NikhilVeeram/MEEN-305-FINAL/best-designs-20/ranked-designs/01_overall_rank__continuous_uniform_both_load_cases_9in_corrected__eval_0370__w_0.02815__fos_1.642/README.md

# Rank 01: continuous_uniform_both_load_cases_9in_corrected eval 370

- Weight-first rank score: `0.028149`
- Weight: `0.02815 lbf`
- Minimum FoS: `1.642`
- Max deflection: `0.09484 in`
- LC2 FoS, x=3..7: mean `2.259`, std `0.426`, range `1.581`
- Print checks: wall `0.040 in`, max opening `0.000`, min ligament `0.105 in`
- Governing case/location: `Load Case 2` at `x = 5.500 in`
- Source run: `continuous_uniform_both_load_cases_9in_corrected`
- Source evaluation id: `370`

This folder is a ranked report artifact generated from a feasible, corrected 9 in design candidate.
