NikhilVeeram/MEEN-305-FINAL/best-designs-20/ranked-designs/02_overall_rank__ultra_light_full_strength_seed2433__eval_1528__w_0.02894__fos_1.732/README.md

# Rank 02: ultra_light_full_strength_seed2433 eval 1528

- Weight-first rank score: `0.028936`
- Weight: `0.02894 lbf`
- Minimum FoS: `1.732`
- Max deflection: `0.16497 in`
- LC2 FoS, x=3..7: mean `2.686`, std `0.476`, range `1.786`
- Print checks: wall `0.040 in`, max opening `0.000`, min ligament `0.112 in`
- Governing case/location: `Load Case 1` at `x = 4.500 in`
- Source run: `ultra_light_full_strength_seed2433`
- Source evaluation id: `1528`

This folder is a ranked report artifact generated from a feasible, corrected 9 in design candidate.
