NikhilVeeram/MEEN-305-FINAL/best-designs-20/ranked-designs/03_overall_rank__ultra_light_run4_asymmetric_seed2427__eval_1102__w_0.02958__fos_2.116/README.md

# Rank 03: ultra_light_run4_asymmetric_seed2427 eval 1102

- Weight-first rank score: `0.029585`
- Weight: `0.02958 lbf`
- Minimum FoS: `2.116`
- Max deflection: `0.09429 in`
- LC2 FoS, x=3..7: mean `2.951`, std `0.675`, range `2.234`
- Print checks: wall `0.040 in`, max opening `0.000`, min ligament `0.147 in`
- Governing case/location: `Load Case 2` at `x = 5.500 in`
- Source run: `ultra_light_run4_asymmetric_seed2427`
- Source evaluation id: `1102`

This folder is a ranked report artifact generated from a feasible, corrected 9 in design candidate.
