NikhilVeeram/MEEN-305-FINAL/best-designs-20/ranked-designs/04_overall_rank__ultra_light_full_strength_seed2433__eval_2458__w_0.02971__fos_1.562/README.md

# Rank 04: ultra_light_full_strength_seed2433 eval 2458

- Weight-first rank score: `0.029710`
- Weight: `0.02971 lbf`
- Minimum FoS: `1.562`
- Max deflection: `0.14261 in`
- LC2 FoS, x=3..7: mean `2.116`, std `0.381`, range `1.238`
- Print checks: wall `0.040 in`, max opening `0.000`, min ligament `0.218 in`
- Governing case/location: `Load Case 2` at `x = 5.500 in`
- Source run: `ultra_light_full_strength_seed2433`
- Source evaluation id: `2458`

This folder is a ranked report artifact generated from a feasible, corrected 9 in design candidate.
