NikhilVeeram/MEEN-305-FINAL/best-designs-20/ranked-designs/05_overall_rank__ultra_light_full_infill_seed2432__eval_2924__w_0.03074__fos_1.789/README.md

# Rank 05: ultra_light_full_infill_seed2432 eval 2924

- Weight-first rank score: `0.030736`
- Weight: `0.03074 lbf`
- Minimum FoS: `1.789`
- Max deflection: `0.08733 in`
- LC2 FoS, x=3..7: mean `2.456`, std `0.451`, range `1.695`
- Print checks: wall `0.040 in`, max opening `0.000`, min ligament `0.199 in`
- Governing case/location: `Load Case 2` at `x = 5.500 in`
- Source run: `ultra_light_full_infill_seed2432`
- Source evaluation id: `2924`

This folder is a ranked report artifact generated from a feasible, corrected 9 in design candidate.
