NikhilVeeram/MEEN-305-FINAL/best-designs-20/ranked-designs/06_overall_rank__ultra_light_full_strength_seed2433__eval_1532__w_0.03127__fos_1.712/README.md

# Rank 06: ultra_light_full_strength_seed2433 eval 1532

- Weight-first rank score: `0.031265`
- Weight: `0.03127 lbf`
- Minimum FoS: `1.712`
- Max deflection: `0.11368 in`
- LC2 FoS, x=3..7: mean `2.360`, std `0.452`, range `1.663`
- Print checks: wall `0.046 in`, max opening `0.000`, min ligament `0.138 in`
- Governing case/location: `Load Case 2` at `x = 5.500 in`
- Source run: `ultra_light_full_strength_seed2433`
- Source evaluation id: `1532`

This folder is a ranked report artifact generated from a feasible, corrected 9 in design candidate.
