NikhilVeeram/MEEN-305-FINAL/best-designs-20/ranked-designs/07_overall_rank__ultra_light_full_infill_seed2432__eval_2497__w_0.03158__fos_1.751/README.md

# Rank 07: ultra_light_full_infill_seed2432 eval 2497

- Weight-first rank score: `0.031578`
- Weight: `0.03158 lbf`
- Minimum FoS: `1.751`
- Max deflection: `0.12404 in`
- LC2 FoS, x=3..7: mean `2.389`, std `0.416`, range `1.544`
- Print checks: wall `0.051 in`, max opening `0.000`, min ligament `0.122 in`
- Governing case/location: `Load Case 2` at `x = 5.500 in`
- Source run: `ultra_light_full_infill_seed2432`
- Source evaluation id: `2497`

This folder is a ranked report artifact generated from a feasible, corrected 9 in design candidate.
