NikhilVeeram/MEEN-305-FINAL/best-designs-20/ranked-designs/08_overall_rank__ultra_light_full_infill_seed2432__eval_2852__w_0.03254__fos_1.713/README.md

# Rank 08: ultra_light_full_infill_seed2432 eval 2852

- Weight-first rank score: `0.032545`
- Weight: `0.03254 lbf`
- Minimum FoS: `1.713`
- Max deflection: `0.14508 in`
- LC2 FoS, x=3..7: mean `2.474`, std `0.432`, range `1.617`
- Print checks: wall `0.052 in`, max opening `0.000`, min ligament `0.096 in`
- Governing case/location: `Load Case 1` at `x = 4.500 in`
- Source run: `ultra_light_full_infill_seed2432`
- Source evaluation id: `2852`

This folder is a ranked report artifact generated from a feasible, corrected 9 in design candidate.
