NikhilVeeram/MEEN-305-FINAL/best-designs-20/ranked-designs/09_overall_rank__ultra_light_full_infill_seed2432__eval_2251__w_0.03329__fos_1.595/README.md

# Rank 09: ultra_light_full_infill_seed2432 eval 2251

- Weight-first rank score: `0.033289`
- Weight: `0.03329 lbf`
- Minimum FoS: `1.595`
- Max deflection: `0.11348 in`
- LC2 FoS, x=3..7: mean `2.198`, std `0.417`, range `1.539`
- Print checks: wall `0.056 in`, max opening `0.000`, min ligament `0.111 in`
- Governing case/location: `Load Case 2` at `x = 5.500 in`
- Source run: `ultra_light_full_infill_seed2432`
- Source evaluation id: `2251`

This folder is a ranked report artifact generated from a feasible, corrected 9 in design candidate.
