NikhilVeeram/MEEN-305-FINAL/best-designs-20/ranked-designs/10_overall_rank__ultra_light_full_infill_seed2432__eval_2514__w_0.03483__fos_1.572/README.md

# Rank 10: ultra_light_full_infill_seed2432 eval 2514

- Weight-first rank score: `0.034829`
- Weight: `0.03483 lbf`
- Minimum FoS: `1.572`
- Max deflection: `0.11648 in`
- LC2 FoS, x=3..7: mean `2.176`, std `0.440`, range `1.578`
- Print checks: wall `0.055 in`, max opening `0.000`, min ligament `0.156 in`
- Governing case/location: `Load Case 2` at `x = 5.500 in`
- Source run: `ultra_light_full_infill_seed2432`
- Source evaluation id: `2514`

This folder is a ranked report artifact generated from a feasible, corrected 9 in design candidate.
