NikhilVeeram/MEEN-305-FINAL/best-designs-20/ranked-designs/11_overall_rank__continuous_uniform_both_load_cases_9in_corrected__eval_0572__w_0.03504__fos_1.877/README.md

# Rank 11: continuous_uniform_both_load_cases_9in_corrected eval 572

- Weight-first rank score: `0.035042`
- Weight: `0.03504 lbf`
- Minimum FoS: `1.877`
- Max deflection: `0.11531 in`
- LC2 FoS, x=3..7: mean `2.533`, std `0.474`, range `1.439`
- Print checks: wall `0.045 in`, max opening `0.000`, min ligament `0.274 in`
- Governing case/location: `Load Case 2` at `x = 5.500 in`
- Source run: `continuous_uniform_both_load_cases_9in_corrected`
- Source evaluation id: `572`

This folder is a ranked report artifact generated from a feasible, corrected 9 in design candidate.
