NikhilVeeram/MEEN-305-FINAL/best-designs-20/ranked-designs/12_overall_rank__continuous_uniform_both_load_cases_9in_corrected__eval_0680__w_0.03546__fos_2.902/README.md

# Rank 12: continuous_uniform_both_load_cases_9in_corrected eval 680

- Weight-first rank score: `0.035456`
- Weight: `0.03546 lbf`
- Minimum FoS: `2.902`
- Max deflection: `0.05080 in`
- LC2 FoS, x=3..7: mean `3.964`, std `0.689`, range `2.585`
- Print checks: wall `0.040 in`, max opening `0.000`, min ligament `0.158 in`
- Governing case/location: `Load Case 2` at `x = 5.500 in`
- Source run: `continuous_uniform_both_load_cases_9in_corrected`
- Source evaluation id: `680`

This folder is a ranked report artifact generated from a feasible, corrected 9 in design candidate.
