NikhilVeeram/MEEN-305-FINAL/best-designs-20/ranked-designs/13_overall_rank__ultra_light_runa_seed2430__eval_2464__w_0.03652__fos_2.154/README.md

# Rank 13: ultra_light_runA_seed2430 eval 2464

- Weight-first rank score: `0.036523`
- Weight: `0.03652 lbf`
- Minimum FoS: `2.154`
- Max deflection: `0.08366 in`
- LC2 FoS, x=3..7: mean `2.841`, std `0.393`, range `1.373`
- Print checks: wall `0.049 in`, max opening `0.000`, min ligament `0.218 in`
- Governing case/location: `Load Case 2` at `x = 5.500 in`
- Source run: `ultra_light_runA_seed2430`
- Source evaluation id: `2464`

This folder is a ranked report artifact generated from a feasible, corrected 9 in design candidate.
