NikhilVeeram/MEEN-305-FINAL/best-designs-20/ranked-designs/14_overall_rank__continuous_uniform_both_load_cases_9in_corrected__eval_0402__w_0.03782__fos_2.022/README.md

# Rank 14: continuous_uniform_both_load_cases_9in_corrected eval 402

- Weight-first rank score: `0.037825`
- Weight: `0.03782 lbf`
- Minimum FoS: `2.022`
- Max deflection: `0.09886 in`
- LC2 FoS, x=3..7: mean `2.773`, std `0.511`, range `1.940`
- Print checks: wall `0.040 in`, max opening `0.000`, min ligament `0.263 in`
- Governing case/location: `Load Case 2` at `x = 5.500 in`
- Source run: `continuous_uniform_both_load_cases_9in_corrected`
- Source evaluation id: `402`

This folder is a ranked report artifact generated from a feasible, corrected 9 in design candidate.
