NikhilVeeram/MEEN-305-FINAL/best-designs-20/ranked-designs/15_overall_rank__continuous_uniform_both_load_cases_9in_corrected__eval_0364__w_0.03983__fos_1.695/README.md

# Rank 15: continuous_uniform_both_load_cases_9in_corrected eval 364

- Weight-first rank score: `0.039828`
- Weight: `0.03983 lbf`
- Minimum FoS: `1.695`
- Max deflection: `0.10435 in`
- LC2 FoS, x=3..7: mean `2.337`, std `0.477`, range `1.711`
- Print checks: wall `0.063 in`, max opening `0.000`, min ligament `0.106 in`
- Governing case/location: `Load Case 2` at `x = 5.500 in`
- Source run: `continuous_uniform_both_load_cases_9in_corrected`
- Source evaluation id: `364`

This folder is a ranked report artifact generated from a feasible, corrected 9 in design candidate.
