NikhilVeeram/MEEN-305-FINAL/best-designs-20/ranked-designs/16_overall_rank__continuous_uniform_both_load_cases_9in_corrected__eval_0219__w_0.03983__fos_1.761/README.md

# Rank 16: continuous_uniform_both_load_cases_9in_corrected eval 219

- Weight-first rank score: `0.039828`
- Weight: `0.03983 lbf`
- Minimum FoS: `1.761`
- Max deflection: `0.11057 in`
- LC2 FoS, x=3..7: mean `2.406`, std `0.427`, range `1.617`
- Print checks: wall `0.061 in`, max opening `0.000`, min ligament `0.175 in`
- Governing case/location: `Load Case 2` at `x = 5.500 in`
- Source run: `continuous_uniform_both_load_cases_9in_corrected`
- Source evaluation id: `219`

This folder is a ranked report artifact generated from a feasible, corrected 9 in design candidate.
