NikhilVeeram/MEEN-305-FINAL/best-designs-20/ranked-designs/18_overall_rank__continuous_uniform_both_load_cases_9in_corrected__eval_0441__w_0.04079__fos_1.503/README.md

# Rank 18: continuous_uniform_both_load_cases_9in_corrected eval 441

- Weight-first rank score: `0.040794`
- Weight: `0.04079 lbf`
- Minimum FoS: `1.503`
- Max deflection: `0.16121 in`
- LC2 FoS, x=3..7: mean `2.118`, std `0.592`, range `2.147`
- Print checks: wall `0.051 in`, max opening `0.000`, min ligament `0.278 in`
- Governing case/location: `Load Case 2` at `x = 5.500 in`
- Source run: `continuous_uniform_both_load_cases_9in_corrected`
- Source evaluation id: `441`

This folder is a ranked report artifact generated from a feasible, corrected 9 in design candidate.
