NikhilVeeram/MEEN-305-FINAL/best-designs-20/ranked-designs/19_overall_rank__ultra_light_full_infill_seed2432__eval_2513__w_0.04121__fos_1.565/README.md

# Rank 19: ultra_light_full_infill_seed2432 eval 2513

- Weight-first rank score: `0.041215`
- Weight: `0.04121 lbf`
- Minimum FoS: `1.565`
- Max deflection: `0.14041 in`
- LC2 FoS, x=3..7: mean `2.134`, std `0.384`, range `1.456`
- Print checks: wall `0.062 in`, max opening `0.000`, min ligament `0.176 in`
- Governing case/location: `Load Case 2` at `x = 5.500 in`
- Source run: `ultra_light_full_infill_seed2432`
- Source evaluation id: `2513`

This folder is a ranked report artifact generated from a feasible, corrected 9 in design candidate.
