NikhilVeeram/MEEN-305-FINAL/best-designs-20/ranked-designs/20_overall_rank__ultra_light_run3_lowheight_seed2426__eval_1611__w_0.04175__fos_2.633/README.md

# Rank 20: ultra_light_run3_lowheight_seed2426 eval 1611

- Weight-first rank score: `0.041748`
- Weight: `0.04175 lbf`
- Minimum FoS: `2.633`
- Max deflection: `0.06265 in`
- LC2 FoS, x=3..7: mean `3.553`, std `0.714`, range `1.912`
- Print checks: wall `0.071 in`, max opening `0.000`, min ligament `0.077 in`
- Governing case/location: `Load Case 2` at `x = 5.500 in`
- Source run: `ultra_light_run3_lowheight_seed2426`
- Source evaluation id: `1611`

This folder is a ranked report artifact generated from a feasible, corrected 9 in design candidate.
