NikhilVeeram/MEEN-305-FINAL/designs/model_exports/continuous_mesh_exports_9in_corrected/README.md

# 3D Beam Models

This folder contains generated 3D models and preview renders for the beam designs found in the repo.

## Generated designs

### continuous_uniform_both_load_cases_9in_corrected

- STL: [continuous_uniform_both_load_cases_9in_corrected.stl](continuous_uniform_both_load_cases_9in_corrected.stl)
- OBJ: [continuous_uniform_both_load_cases_9in_corrected.obj](continuous_uniform_both_load_cases_9in_corrected.obj)
- Preview: [continuous_uniform_both_load_cases_9in_corrected_preview.png](continuous_uniform_both_load_cases_9in_corrected_preview.png)
- DXF sketch: [continuous_uniform_both_load_cases_9in_corrected.dxf](continuous_uniform_both_load_cases_9in_corrected.dxf)

## How to view them

- Double-click an `.obj` or `.stl` file in a local 3D viewer if you have one installed.
- Use the `.png` previews for quick comparison inside the repo.
- Re-run `python scripts/beam_3d_models.py` after optimization updates to refresh the models.
