NikhilVeeram/MEEN-305-FINAL/designs/model_exports/continuous_mesh_exports/README.md

# 3D Beam Models

This folder contains generated 3D models and preview renders for the beam designs found in the repo.

## Generated designs

### continuous_uniform_load_case_1

- STL: [continuous_uniform_load_case_1.stl](continuous_uniform_load_case_1.stl)
- OBJ: [continuous_uniform_load_case_1.obj](continuous_uniform_load_case_1.obj)
- Preview: [continuous_uniform_load_case_1_preview.png](continuous_uniform_load_case_1_preview.png)
- DXF sketch: [continuous_uniform_load_case_1.dxf](continuous_uniform_load_case_1.dxf)

### continuous_uniform_load_case_2

- STL: [continuous_uniform_load_case_2.stl](continuous_uniform_load_case_2.stl)
- OBJ: [continuous_uniform_load_case_2.obj](continuous_uniform_load_case_2.obj)
- Preview: [continuous_uniform_load_case_2_preview.png](continuous_uniform_load_case_2_preview.png)
- DXF sketch: [continuous_uniform_load_case_2.dxf](continuous_uniform_load_case_2.dxf)

### continuous_uniform_both_load_cases

- STL: [continuous_uniform_both_load_cases.stl](continuous_uniform_both_load_cases.stl)
- OBJ: [continuous_uniform_both_load_cases.obj](continuous_uniform_both_load_cases.obj)
- Preview: [continuous_uniform_both_load_cases_preview.png](continuous_uniform_both_load_cases_preview.png)
- DXF sketch: [continuous_uniform_both_load_cases.dxf](continuous_uniform_both_load_cases.dxf)

## How to view them

- Double-click an `.obj` or `.stl` file in a local 3D viewer if you have one installed.
- Use the `.png` previews for quick comparison inside the repo.
- Re-run `python scripts/beam_3d_models.py` after optimization updates to refresh the models.
