NikhilVeeram/MEEN-305-FINAL/best-designs-20/design-packages/01_overall_rank__continuous_uniform_both_load_cases_9in_corrected__eval_0370__w_0.02815__fos_1.642/README.md

# 01_overall_rank__continuous_uniform_both_load_cases_9in_corrected__eval_0370__w_0.02815__fos_1.642

- Included files:
  - `01_overall_rank__continuous_uniform_both_load_cases_9in_corrected__eval_0370__w_0.02815__fos_1.642.stl`
  - `01_overall_rank__continuous_uniform_both_load_cases_9in_corrected__eval_0370__w_0.02815__fos_1.642.obj`
  - `01_overall_rank__continuous_uniform_both_load_cases_9in_corrected__eval_0370__w_0.02815__fos_1.642_preview.png`
  - `01_overall_rank__continuous_uniform_both_load_cases_9in_corrected__eval_0370__w_0.02815__fos_1.642.dxf`
  - `best_design.json`
  - `optimization_report.md`
  - `optimization_report.tex`
  - `beam_parameter_map.png`
  - `best_design/*.png`

The PNG preview is the 3D look. The DXF file is a lightweight 2D sketch export.
