NikhilVeeram/MEEN-305-FINAL/best-designs-20/design-packages/02_overall_rank__ultra_light_full_strength_seed2433__eval_1528__w_0.02894__fos_1.732/README.md

# 02_overall_rank__ultra_light_full_strength_seed2433__eval_1528__w_0.02894__fos_1.732

- Included files:
  - `02_overall_rank__ultra_light_full_strength_seed2433__eval_1528__w_0.02894__fos_1.732.stl`
  - `02_overall_rank__ultra_light_full_strength_seed2433__eval_1528__w_0.02894__fos_1.732.obj`
  - `02_overall_rank__ultra_light_full_strength_seed2433__eval_1528__w_0.02894__fos_1.732_preview.png`
  - `02_overall_rank__ultra_light_full_strength_seed2433__eval_1528__w_0.02894__fos_1.732.dxf`
  - `best_design.json`
  - `optimization_report.md`
  - `optimization_report.tex`
  - `beam_parameter_map.png`
  - `best_design/*.png`

The PNG preview is the 3D look. The DXF file is a lightweight 2D sketch export.
