NikhilVeeram/MEEN-305-FINAL/best-designs-20/design-packages/03_overall_rank__ultra_light_run4_asymmetric_seed2427__eval_1102__w_0.02958__fos_2.116/README.md

# 03_overall_rank__ultra_light_run4_asymmetric_seed2427__eval_1102__w_0.02958__fos_2.116

- Included files:
  - `03_overall_rank__ultra_light_run4_asymmetric_seed2427__eval_1102__w_0.02958__fos_2.116.stl`
  - `03_overall_rank__ultra_light_run4_asymmetric_seed2427__eval_1102__w_0.02958__fos_2.116.obj`
  - `03_overall_rank__ultra_light_run4_asymmetric_seed2427__eval_1102__w_0.02958__fos_2.116_preview.png`
  - `03_overall_rank__ultra_light_run4_asymmetric_seed2427__eval_1102__w_0.02958__fos_2.116.dxf`
  - `best_design.json`
  - `optimization_report.md`
  - `optimization_report.tex`
  - `beam_parameter_map.png`
  - `best_design/*.png`

The PNG preview is the 3D look. The DXF file is a lightweight 2D sketch export.
