NikhilVeeram/MEEN-305-FINAL/best-designs-20/design-packages/04_overall_rank__ultra_light_full_strength_seed2433__eval_2458__w_0.02971__fos_1.562/README.md

# 04_overall_rank__ultra_light_full_strength_seed2433__eval_2458__w_0.02971__fos_1.562

- Included files:
  - `04_overall_rank__ultra_light_full_strength_seed2433__eval_2458__w_0.02971__fos_1.562.stl`
  - `04_overall_rank__ultra_light_full_strength_seed2433__eval_2458__w_0.02971__fos_1.562.obj`
  - `04_overall_rank__ultra_light_full_strength_seed2433__eval_2458__w_0.02971__fos_1.562_preview.png`
  - `04_overall_rank__ultra_light_full_strength_seed2433__eval_2458__w_0.02971__fos_1.562.dxf`
  - `best_design.json`
  - `optimization_report.md`
  - `optimization_report.tex`
  - `beam_parameter_map.png`
  - `best_design/*.png`

The PNG preview is the 3D look. The DXF file is a lightweight 2D sketch export.
