NikhilVeeram/MEEN-305-FINAL/best-designs-20/design-packages/05_overall_rank__ultra_light_full_infill_seed2432__eval_2924__w_0.03074__fos_1.789/README.md

# 05_overall_rank__ultra_light_full_infill_seed2432__eval_2924__w_0.03074__fos_1.789

- Included files:
  - `05_overall_rank__ultra_light_full_infill_seed2432__eval_2924__w_0.03074__fos_1.789.stl`
  - `05_overall_rank__ultra_light_full_infill_seed2432__eval_2924__w_0.03074__fos_1.789.obj`
  - `05_overall_rank__ultra_light_full_infill_seed2432__eval_2924__w_0.03074__fos_1.789_preview.png`
  - `05_overall_rank__ultra_light_full_infill_seed2432__eval_2924__w_0.03074__fos_1.789.dxf`
  - `best_design.json`
  - `optimization_report.md`
  - `optimization_report.tex`
  - `beam_parameter_map.png`
  - `best_design/*.png`

The PNG preview is the 3D look. The DXF file is a lightweight 2D sketch export.
