NikhilVeeram/MEEN-305-FINAL/best-designs-20/design-packages/06_overall_rank__ultra_light_full_strength_seed2433__eval_1532__w_0.03127__fos_1.712/README.md

# 06_overall_rank__ultra_light_full_strength_seed2433__eval_1532__w_0.03127__fos_1.712

- Included files:
  - `06_overall_rank__ultra_light_full_strength_seed2433__eval_1532__w_0.03127__fos_1.712.stl`
  - `06_overall_rank__ultra_light_full_strength_seed2433__eval_1532__w_0.03127__fos_1.712.obj`
  - `06_overall_rank__ultra_light_full_strength_seed2433__eval_1532__w_0.03127__fos_1.712_preview.png`
  - `06_overall_rank__ultra_light_full_strength_seed2433__eval_1532__w_0.03127__fos_1.712.dxf`
  - `best_design.json`
  - `optimization_report.md`
  - `optimization_report.tex`
  - `beam_parameter_map.png`
  - `best_design/*.png`

The PNG preview is the 3D look. The DXF file is a lightweight 2D sketch export.
