NikhilVeeram/MEEN-305-FINAL/best-designs-20/design-packages/07_overall_rank__ultra_light_full_infill_seed2432__eval_2497__w_0.03158__fos_1.751/README.md

# 07_overall_rank__ultra_light_full_infill_seed2432__eval_2497__w_0.03158__fos_1.751

- Included files:
  - `07_overall_rank__ultra_light_full_infill_seed2432__eval_2497__w_0.03158__fos_1.751.stl`
  - `07_overall_rank__ultra_light_full_infill_seed2432__eval_2497__w_0.03158__fos_1.751.obj`
  - `07_overall_rank__ultra_light_full_infill_seed2432__eval_2497__w_0.03158__fos_1.751_preview.png`
  - `07_overall_rank__ultra_light_full_infill_seed2432__eval_2497__w_0.03158__fos_1.751.dxf`
  - `best_design.json`
  - `optimization_report.md`
  - `optimization_report.tex`
  - `beam_parameter_map.png`
  - `best_design/*.png`

The PNG preview is the 3D look. The DXF file is a lightweight 2D sketch export.
