NikhilVeeram/MEEN-305-FINAL/best-designs-20/design-packages/08_overall_rank__ultra_light_full_infill_seed2432__eval_2852__w_0.03254__fos_1.713/README.md

# 08_overall_rank__ultra_light_full_infill_seed2432__eval_2852__w_0.03254__fos_1.713

- Included files:
  - `08_overall_rank__ultra_light_full_infill_seed2432__eval_2852__w_0.03254__fos_1.713.stl`
  - `08_overall_rank__ultra_light_full_infill_seed2432__eval_2852__w_0.03254__fos_1.713.obj`
  - `08_overall_rank__ultra_light_full_infill_seed2432__eval_2852__w_0.03254__fos_1.713_preview.png`
  - `08_overall_rank__ultra_light_full_infill_seed2432__eval_2852__w_0.03254__fos_1.713.dxf`
  - `best_design.json`
  - `optimization_report.md`
  - `optimization_report.tex`
  - `beam_parameter_map.png`
  - `best_design/*.png`

The PNG preview is the 3D look. The DXF file is a lightweight 2D sketch export.
