NikhilVeeram/MEEN-305-FINAL/best-designs-20/design-packages/09_overall_rank__ultra_light_full_infill_seed2432__eval_2251__w_0.03329__fos_1.595/README.md

# 09_overall_rank__ultra_light_full_infill_seed2432__eval_2251__w_0.03329__fos_1.595

- Included files:
  - `09_overall_rank__ultra_light_full_infill_seed2432__eval_2251__w_0.03329__fos_1.595.stl`
  - `09_overall_rank__ultra_light_full_infill_seed2432__eval_2251__w_0.03329__fos_1.595.obj`
  - `09_overall_rank__ultra_light_full_infill_seed2432__eval_2251__w_0.03329__fos_1.595_preview.png`
  - `09_overall_rank__ultra_light_full_infill_seed2432__eval_2251__w_0.03329__fos_1.595.dxf`
  - `best_design.json`
  - `optimization_report.md`
  - `optimization_report.tex`
  - `beam_parameter_map.png`
  - `best_design/*.png`

The PNG preview is the 3D look. The DXF file is a lightweight 2D sketch export.
