NikhilVeeram/MEEN-305-FINAL/best-designs-20/design-packages/10_overall_rank__ultra_light_full_infill_seed2432__eval_2514__w_0.03483__fos_1.572/README.md

# 10_overall_rank__ultra_light_full_infill_seed2432__eval_2514__w_0.03483__fos_1.572

- Included files:
  - `10_overall_rank__ultra_light_full_infill_seed2432__eval_2514__w_0.03483__fos_1.572.stl`
  - `10_overall_rank__ultra_light_full_infill_seed2432__eval_2514__w_0.03483__fos_1.572.obj`
  - `10_overall_rank__ultra_light_full_infill_seed2432__eval_2514__w_0.03483__fos_1.572_preview.png`
  - `10_overall_rank__ultra_light_full_infill_seed2432__eval_2514__w_0.03483__fos_1.572.dxf`
  - `best_design.json`
  - `optimization_report.md`
  - `optimization_report.tex`
  - `beam_parameter_map.png`
  - `best_design/*.png`

The PNG preview is the 3D look. The DXF file is a lightweight 2D sketch export.
