NikhilVeeram/MEEN-305-FINAL/best-designs-20/design-packages/11_overall_rank__continuous_uniform_both_load_cases_9in_corrected__eval_0572__w_0.03504__fos_1.877/README.md

# 11_overall_rank__continuous_uniform_both_load_cases_9in_corrected__eval_0572__w_0.03504__fos_1.877

- Included files:
  - `11_overall_rank__continuous_uniform_both_load_cases_9in_corrected__eval_0572__w_0.03504__fos_1.877.stl`
  - `11_overall_rank__continuous_uniform_both_load_cases_9in_corrected__eval_0572__w_0.03504__fos_1.877.obj`
  - `11_overall_rank__continuous_uniform_both_load_cases_9in_corrected__eval_0572__w_0.03504__fos_1.877_preview.png`
  - `11_overall_rank__continuous_uniform_both_load_cases_9in_corrected__eval_0572__w_0.03504__fos_1.877.dxf`
  - `best_design.json`
  - `optimization_report.md`
  - `optimization_report.tex`
  - `beam_parameter_map.png`
  - `best_design/*.png`

The PNG preview is the 3D look. The DXF file is a lightweight 2D sketch export.
