NikhilVeeram/MEEN-305-FINAL/best-designs-20/design-packages/12_overall_rank__continuous_uniform_both_load_cases_9in_corrected__eval_0680__w_0.03546__fos_2.902/README.md

# 12_overall_rank__continuous_uniform_both_load_cases_9in_corrected__eval_0680__w_0.03546__fos_2.902

- Included files:
  - `12_overall_rank__continuous_uniform_both_load_cases_9in_corrected__eval_0680__w_0.03546__fos_2.902.stl`
  - `12_overall_rank__continuous_uniform_both_load_cases_9in_corrected__eval_0680__w_0.03546__fos_2.902.obj`
  - `12_overall_rank__continuous_uniform_both_load_cases_9in_corrected__eval_0680__w_0.03546__fos_2.902_preview.png`
  - `12_overall_rank__continuous_uniform_both_load_cases_9in_corrected__eval_0680__w_0.03546__fos_2.902.dxf`
  - `best_design.json`
  - `optimization_report.md`
  - `optimization_report.tex`
  - `beam_parameter_map.png`
  - `best_design/*.png`

The PNG preview is the 3D look. The DXF file is a lightweight 2D sketch export.
