NikhilVeeram/MEEN-305-FINAL/best-designs-20/design-packages/13_overall_rank__ultra_light_runa_seed2430__eval_2464__w_0.03652__fos_2.154/README.md

# 13_overall_rank__ultra_light_runa_seed2430__eval_2464__w_0.03652__fos_2.154

- Included files:
  - `13_overall_rank__ultra_light_runa_seed2430__eval_2464__w_0.03652__fos_2.154.stl`
  - `13_overall_rank__ultra_light_runa_seed2430__eval_2464__w_0.03652__fos_2.154.obj`
  - `13_overall_rank__ultra_light_runa_seed2430__eval_2464__w_0.03652__fos_2.154_preview.png`
  - `13_overall_rank__ultra_light_runa_seed2430__eval_2464__w_0.03652__fos_2.154.dxf`
  - `best_design.json`
  - `optimization_report.md`
  - `optimization_report.tex`
  - `beam_parameter_map.png`
  - `best_design/*.png`

The PNG preview is the 3D look. The DXF file is a lightweight 2D sketch export.
