NikhilVeeram/MEEN-305-FINAL/best-designs-20/design-packages/14_overall_rank__continuous_uniform_both_load_cases_9in_corrected__eval_0402__w_0.03782__fos_2.022/README.md

# 14_overall_rank__continuous_uniform_both_load_cases_9in_corrected__eval_0402__w_0.03782__fos_2.022

- Included files:
  - `14_overall_rank__continuous_uniform_both_load_cases_9in_corrected__eval_0402__w_0.03782__fos_2.022.stl`
  - `14_overall_rank__continuous_uniform_both_load_cases_9in_corrected__eval_0402__w_0.03782__fos_2.022.obj`
  - `14_overall_rank__continuous_uniform_both_load_cases_9in_corrected__eval_0402__w_0.03782__fos_2.022_preview.png`
  - `14_overall_rank__continuous_uniform_both_load_cases_9in_corrected__eval_0402__w_0.03782__fos_2.022.dxf`
  - `best_design.json`
  - `optimization_report.md`
  - `optimization_report.tex`
  - `beam_parameter_map.png`
  - `best_design/*.png`

The PNG preview is the 3D look. The DXF file is a lightweight 2D sketch export.
