NikhilVeeram/MEEN-305-FINAL/best-designs-20/design-packages/15_overall_rank__continuous_uniform_both_load_cases_9in_corrected__eval_0364__w_0.03983__fos_1.695/README.md

# 15_overall_rank__continuous_uniform_both_load_cases_9in_corrected__eval_0364__w_0.03983__fos_1.695

- Included files:
  - `15_overall_rank__continuous_uniform_both_load_cases_9in_corrected__eval_0364__w_0.03983__fos_1.695.stl`
  - `15_overall_rank__continuous_uniform_both_load_cases_9in_corrected__eval_0364__w_0.03983__fos_1.695.obj`
  - `15_overall_rank__continuous_uniform_both_load_cases_9in_corrected__eval_0364__w_0.03983__fos_1.695_preview.png`
  - `15_overall_rank__continuous_uniform_both_load_cases_9in_corrected__eval_0364__w_0.03983__fos_1.695.dxf`
  - `best_design.json`
  - `optimization_report.md`
  - `optimization_report.tex`
  - `beam_parameter_map.png`
  - `best_design/*.png`

The PNG preview is the 3D look. The DXF file is a lightweight 2D sketch export.
