NikhilVeeram/MEEN-305-FINAL/best-designs-20/design-packages/16_overall_rank__continuous_uniform_both_load_cases_9in_corrected__eval_0219__w_0.03983__fos_1.761/README.md

# 16_overall_rank__continuous_uniform_both_load_cases_9in_corrected__eval_0219__w_0.03983__fos_1.761

- Included files:
  - `16_overall_rank__continuous_uniform_both_load_cases_9in_corrected__eval_0219__w_0.03983__fos_1.761.stl`
  - `16_overall_rank__continuous_uniform_both_load_cases_9in_corrected__eval_0219__w_0.03983__fos_1.761.obj`
  - `16_overall_rank__continuous_uniform_both_load_cases_9in_corrected__eval_0219__w_0.03983__fos_1.761_preview.png`
  - `16_overall_rank__continuous_uniform_both_load_cases_9in_corrected__eval_0219__w_0.03983__fos_1.761.dxf`
  - `best_design.json`
  - `optimization_report.md`
  - `optimization_report.tex`
  - `beam_parameter_map.png`
  - `best_design/*.png`

The PNG preview is the 3D look. The DXF file is a lightweight 2D sketch export.
