NikhilVeeram/MEEN-305-FINAL/best-designs-20/design-packages/18_overall_rank__continuous_uniform_both_load_cases_9in_corrected__eval_0441__w_0.04079__fos_1.503/README.md

# 18_overall_rank__continuous_uniform_both_load_cases_9in_corrected__eval_0441__w_0.04079__fos_1.503

- Included files:
  - `18_overall_rank__continuous_uniform_both_load_cases_9in_corrected__eval_0441__w_0.04079__fos_1.503.stl`
  - `18_overall_rank__continuous_uniform_both_load_cases_9in_corrected__eval_0441__w_0.04079__fos_1.503.obj`
  - `18_overall_rank__continuous_uniform_both_load_cases_9in_corrected__eval_0441__w_0.04079__fos_1.503_preview.png`
  - `18_overall_rank__continuous_uniform_both_load_cases_9in_corrected__eval_0441__w_0.04079__fos_1.503.dxf`
  - `best_design.json`
  - `optimization_report.md`
  - `optimization_report.tex`
  - `beam_parameter_map.png`
  - `best_design/*.png`

The PNG preview is the 3D look. The DXF file is a lightweight 2D sketch export.
