NikhilVeeram/MEEN-305-FINAL/best-designs-20/design-packages/19_overall_rank__ultra_light_full_infill_seed2432__eval_2513__w_0.04121__fos_1.565/README.md

# 19_overall_rank__ultra_light_full_infill_seed2432__eval_2513__w_0.04121__fos_1.565

- Included files:
  - `19_overall_rank__ultra_light_full_infill_seed2432__eval_2513__w_0.04121__fos_1.565.stl`
  - `19_overall_rank__ultra_light_full_infill_seed2432__eval_2513__w_0.04121__fos_1.565.obj`
  - `19_overall_rank__ultra_light_full_infill_seed2432__eval_2513__w_0.04121__fos_1.565_preview.png`
  - `19_overall_rank__ultra_light_full_infill_seed2432__eval_2513__w_0.04121__fos_1.565.dxf`
  - `best_design.json`
  - `optimization_report.md`
  - `optimization_report.tex`
  - `beam_parameter_map.png`
  - `best_design/*.png`

The PNG preview is the 3D look. The DXF file is a lightweight 2D sketch export.
