NikhilVeeram/MEEN-305-FINAL/best-designs-20/design-packages/20_overall_rank__ultra_light_run3_lowheight_seed2426__eval_1611__w_0.04175__fos_2.633/README.md

# 20_overall_rank__ultra_light_run3_lowheight_seed2426__eval_1611__w_0.04175__fos_2.633

- Included files:
  - `20_overall_rank__ultra_light_run3_lowheight_seed2426__eval_1611__w_0.04175__fos_2.633.stl`
  - `20_overall_rank__ultra_light_run3_lowheight_seed2426__eval_1611__w_0.04175__fos_2.633.obj`
  - `20_overall_rank__ultra_light_run3_lowheight_seed2426__eval_1611__w_0.04175__fos_2.633_preview.png`
  - `20_overall_rank__ultra_light_run3_lowheight_seed2426__eval_1611__w_0.04175__fos_2.633.dxf`
  - `best_design.json`
  - `optimization_report.md`
  - `optimization_report.tex`
  - `beam_parameter_map.png`
  - `best_design/*.png`

The PNG preview is the 3D look. The DXF file is a lightweight 2D sketch export.
