NikhilVeeram/MEEN-305-FINAL/designs/packages/continuous_design_deliverables_9in_practical_buffer/continuous_uniform_both_load_cases_9in_practical_buffer/README.md

# continuous_uniform_both_load_cases_9in_practical_buffer

- Included files:
  - `continuous_uniform_both_load_cases_9in_practical_buffer.stl`
  - `continuous_uniform_both_load_cases_9in_practical_buffer.obj`
  - `continuous_uniform_both_load_cases_9in_practical_buffer_preview.png`
  - `continuous_uniform_both_load_cases_9in_practical_buffer.dxf`
  - `best_design.json`
  - `optimization_report.md`
  - `optimization_report.tex`
  - `beam_parameter_map.png`
  - `best_design/*.png`

The PNG preview is the 3D look. The DXF file is a lightweight 2D sketch export.
