NikhilVeeram/MEEN-305-FINAL/designs/packages/continuous_design_deliverables_9in_corrected/continuous_uniform_both_load_cases_9in_corrected/README.md

# continuous_uniform_both_load_cases_9in_corrected

- Included files:
  - `continuous_uniform_both_load_cases_9in_corrected.stl`
  - `continuous_uniform_both_load_cases_9in_corrected.obj`
  - `continuous_uniform_both_load_cases_9in_corrected_preview.png`
  - `continuous_uniform_both_load_cases_9in_corrected.dxf`
  - `best_design.json`
  - `optimization_report.md`
  - `optimization_report.tex`
  - `beam_parameter_map.png`
  - `best_design/*.png`

The PNG preview is the 3D look. The DXF file is a lightweight 2D sketch export.
