NikhilVeeram/MEEN-305-FINAL/designs/packages/continuous_design_deliverables/continuous_uniform_both_load_cases/README.md

# continuous_uniform_both_load_cases

- Included files:
  - `continuous_uniform_both_load_cases.stl`
  - `continuous_uniform_both_load_cases.obj`
  - `continuous_uniform_both_load_cases_preview.png`
  - `continuous_uniform_both_load_cases.dxf`
  - `best_design.json`
  - `optimization_report.md`
  - `optimization_report.tex`
  - `beam_parameter_map.png`
  - `best_design/*.png`

The PNG preview is the 3D look. The DXF file is a lightweight 2D sketch export.
