NikhilVeeram/MEEN-305-FINAL/designs/packages/continuous_design_deliverables/continuous_uniform_load_case_1/README.md

# continuous_uniform_load_case_1

- Included files:
  - `continuous_uniform_load_case_1.stl`
  - `continuous_uniform_load_case_1.obj`
  - `continuous_uniform_load_case_1_preview.png`
  - `continuous_uniform_load_case_1.dxf`
  - `best_design.json`
  - `optimization_report.md`
  - `optimization_report.tex`
  - `beam_parameter_map.png`
  - `best_design/*.png`

The PNG preview is the 3D look. The DXF file is a lightweight 2D sketch export.
