NikhilVeeram/MEEN-305-FINAL/optimization_smoke_test/optimization_report.md

# Beam Optimization Report

## Search Summary

- Search method: stratified global sampling with elite local refinement
- Total evaluated designs: 144
- Feasible designs found: 144
- Minimum required factor of safety: 1.500
- Maximum allowed deflection: not enforced in this run
- Random seed: 305

## Best Design

- Weight: 0.10285 lbf
- Minimum factor of safety: 13.855
- Maximum deflection: 0.00763 in
- Constraint status: feasible

### Geometry Variables

| Variable | Value |
| --- | ---: |
| $L$ [in] | 8.000 |
| $L_{total}$ [in] | 9.000 |
| $b_L$ [in] | 0.755 |
| $b_M$ [in] | 1.205 |
| $b_R$ [in] | 1.162 |
| $h_L$ [in] | 0.700 |
| $h_M$ [in] | 0.706 |
| $h_R$ [in] | 1.222 |
| $t$ [in] | 0.082 |
| $E_{eff}$ [psi] | 297500.0 |
| $\sigma_{allow,eff}$ [psi] | 2380.0 |

### Best-Design Load-Case Metrics

| Load Case | Orientation | Load [lbf] | Location [in] | Min FoS | Max Deflection [in] | Max von Mises [psi] |
| --- | --- | ---: | ---: | ---: | ---: | ---: |
| Load Case 1 | upright | 5.000 | 4.000 | 13.855 | 0.00763 | 171.8 |
| Load Case 2 | side | 3.000 | 2.500 | 29.869 | 0.00214 | 79.7 |

## Beam Structure and Parameters

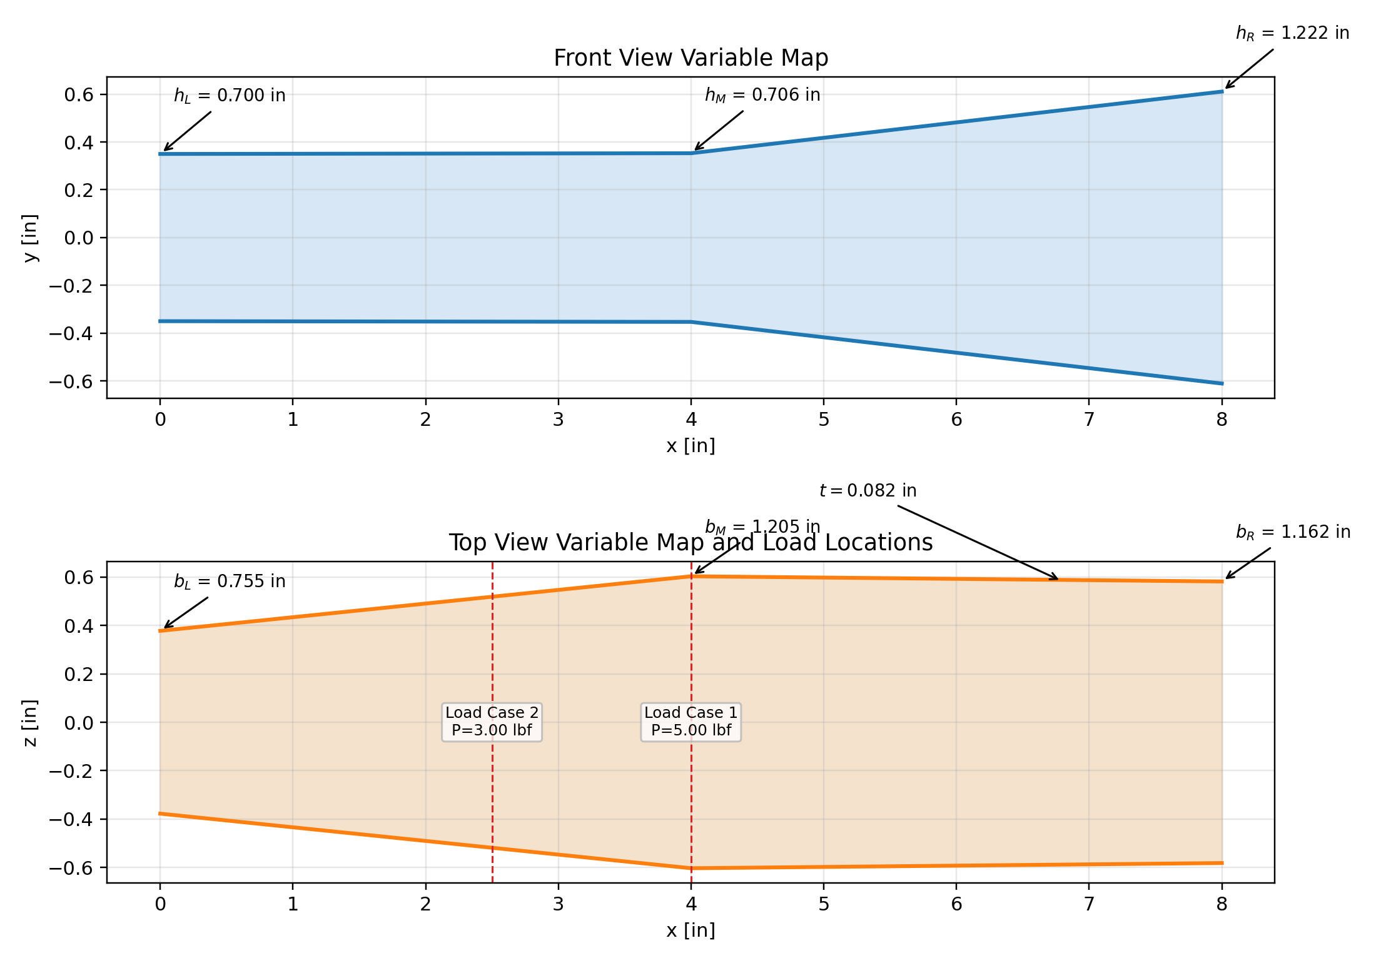
[picture p70: optimization_smoke_test/beam_parameter_map.png]
Beam parameter map


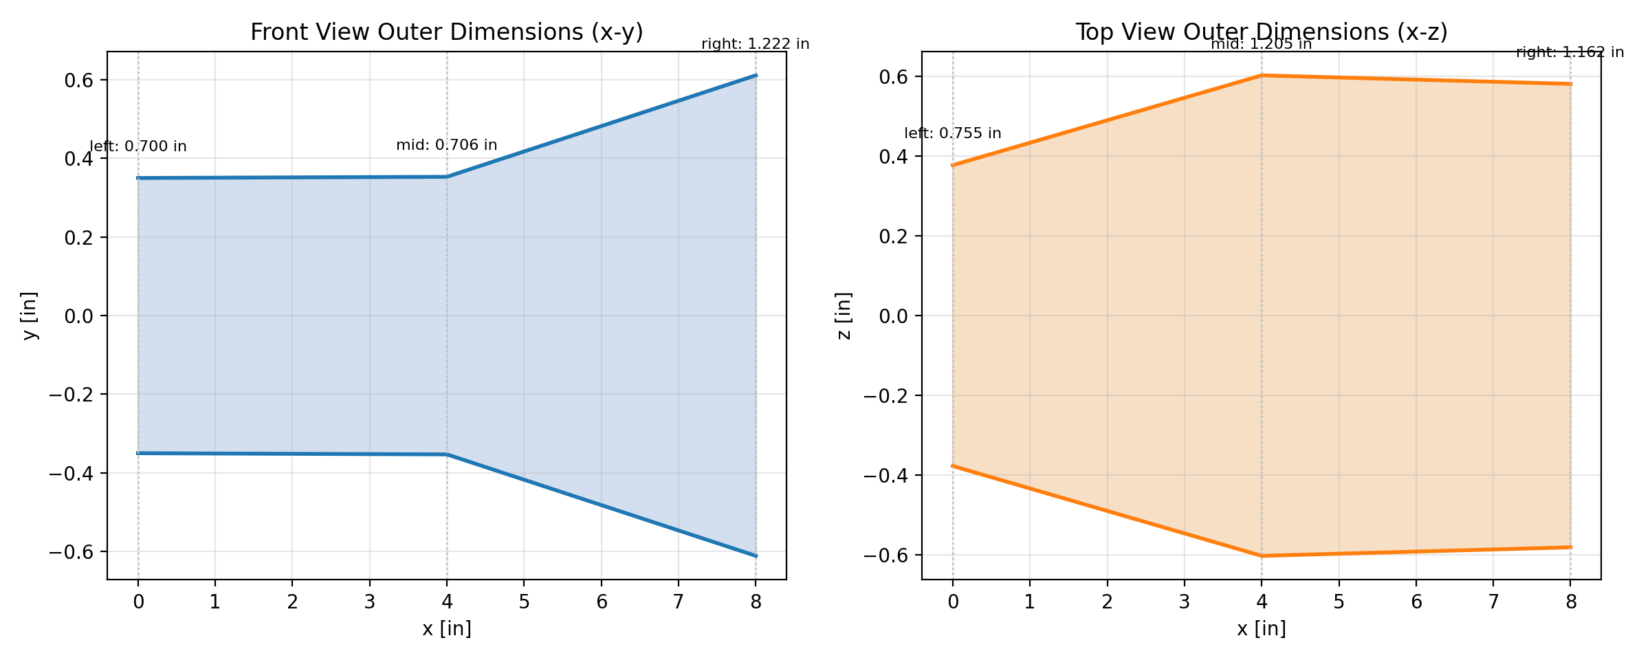
[picture p71: optimization_smoke_test/best_design/outer_dimension_views.png]
Outer dimension views


## General Equations

### Geometry

- $$b(x)=\begin{cases}0.7545 + (0.1126)x, & 0 \le x \le 4.0000\\1.2051 + (-0.0107)(x-4.0000), & 4.0000 < x \le 8.0000\end{cases}$$
- $$h(x)=\begin{cases}0.7000 + (0.0015)x, & 0 \le x \le 4.0000\\0.7060 + (0.1290)(x-4.0000), & 4.0000 < x \le 8.0000\end{cases}$$
- Hollow tube area: $A(x)=b(x)h(x)-[b(x)-2t][h(x)-2t]$
- Upright bending second moment: $I(x)=\frac{b(x)h(x)^3-[b(x)-2t][h(x)-2t]^3}{12}$
- Side-rotated bending second moment: $I_{side}(x)=\frac{h(x)b(x)^3-[h(x)-2t][b(x)-2t]^3}{12}$
- Section modulus: $S(x)=I(x)/c(x)$ with $c(x)=\text{outer vertical dimension}/2$

### Statics and Stress

- Reactions for a point load $P$ at $x=a$: $R_A=P(L-a)/L$, $R_B=Pa/L$
- Shear and moment: $V(x)$ and $M(x)$ are computed piecewise from the reactions and applied load
- Bending stress: $\sigma_b(x)=|M(x)|/S(x)$
- Shear stress estimate: $\tau(x)=|V(x)|/A_{shear}(x)$ with $A_{shear}(x)=2t\,h_{clear}(x)$ for the active orientation
- von Mises stress: $\sigma_{vm}(x)=\sqrt{\sigma_b(x)^2+3\tau(x)^2}$
- Factor of safety: $FoS(x)=\sigma_{allow,eff}/\sigma_{vm}(x)$

### Deflection and Objective

- Euler-Bernoulli relation: $E_{eff}I(x)v''(x)=M(x)$
- Weight objective: $W=\rho\int_0^L A(x)\,dx$
- Search objective used here: minimize weight while enforcing factor-of-safety and optional deflection constraints

## Automatic Trail of Tried Designs

- Full design study table: `design_study.csv`
- Best design record: `best_design.json`
- Best-design plots folder: `best_design/`
