NikhilVeeram/MEEN-305-FINAL/designs/active_runs/ultra_light_run4_asymmetric_seed2427/optimization_report.tex

\documentclass[11pt]{article}
\usepackage[margin=1in]{geometry}
\usepackage{amsmath}
\usepackage{booktabs}
\usepackage{graphicx}
\usepackage{float}
\title{Beam Optimization Report}
\date{}
\begin{document}
\maketitle

\section*{Search Summary}
\begin{itemize}
\item Search method: stratified global sampling with elite local refinement
\item Total evaluated designs: 1880
\item Feasible designs found: 465
\item Minimum required factor of safety: 1.500
\item Objective shaping: penalize excess FoS margin and underutilized stress envelope so the design approaches the 1.5 target more closely
\item Maximum allowed deflection: not enforced
\item Random seed: 2427
\end{itemize}

\section*{Best Design}
\begin{itemize}
\item Weight: 0.02225 lbf
\item Minimum factor of safety: 1.687
\item Excess FoS above target: 0.187
\item Governing minimum-FoS load case: Load Case 1 at $x=4.500$ in
\item Maximum deflection: 0.15763 in
\item Uniformity score toward FoS target (0 is best): 0.245114
\item Symmetry score (0 is best): 0.192914
\item Smoothness score (0 is best): 0.075101
\item Durability score (0 is best): 0.000000
\item Effective modulus: 297500.0 psi
\item Effective allowable stress: 2380.0 psi
\end{itemize}

\subsection*{Geometry Variables}
\begin{center}
\begin{tabular}{lr}
\toprule
Variable & Value \\
\midrule
Support span $L$ [in] & 8.000 \\
Total beam length $L_{total}$ [in] & 9.000 \\
$x_A$ [in] & 0.500 \\
$x_B$ [in] & 8.500 \\
$b_L$ [in] & 0.220 \\
$b_M$ [in] & 0.800 \\
$b_R$ [in] & 0.220 \\
$h_L$ [in] & 0.358 \\
$h_M$ [in] & 0.292 \\
$h_R$ [in] & 0.512 \\
$t$ [in] & 0.040 \\
$r_L$ [-] & 0.000 \\
$r_M$ [-] & 0.387 \\
$r_R$ [-] & 0.629 \\
\bottomrule
\end{tabular}
\end{center}

\subsection*{Beam Structure and Parameters}
\begin{figure}[H]
\centering

\caption{Variable map used in the optimization run.}
\end{figure}

\begin{figure}[H]
\centering

\caption{Outer dimension views for the best design.}
\end{figure}

\subsection*{Best-Design Load-Case Metrics}
\begin{center}
\begin{tabular}{lllllllll}
\toprule
Load Case & Orientation & Load [lbf] & From A [in] & Global $x$ [in] & Min FoS & FoS x [in] & Max Defl. [in] & Max $\sigma_{vm}$ [psi] \\
\midrule
Load Case 1 & upright & 5.000 & 4.000 & 4.500 & 1.687 & 4.500 & 0.15763 & 1410.5 \\
Load Case 2 & side & 8.000 & 5.000 & 5.500 & 1.787 & 8.500 & 0.07752 & 1331.8 \\
\bottomrule
\end{tabular}
\end{center}
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
