NikhilVeeram/MEEN-305-FINAL/best-designs-20/3d-models/02_overall_rank__ultra_light_full_strength_seed2433__eval_1528__w_0.02894__fos_1.732_preview.png

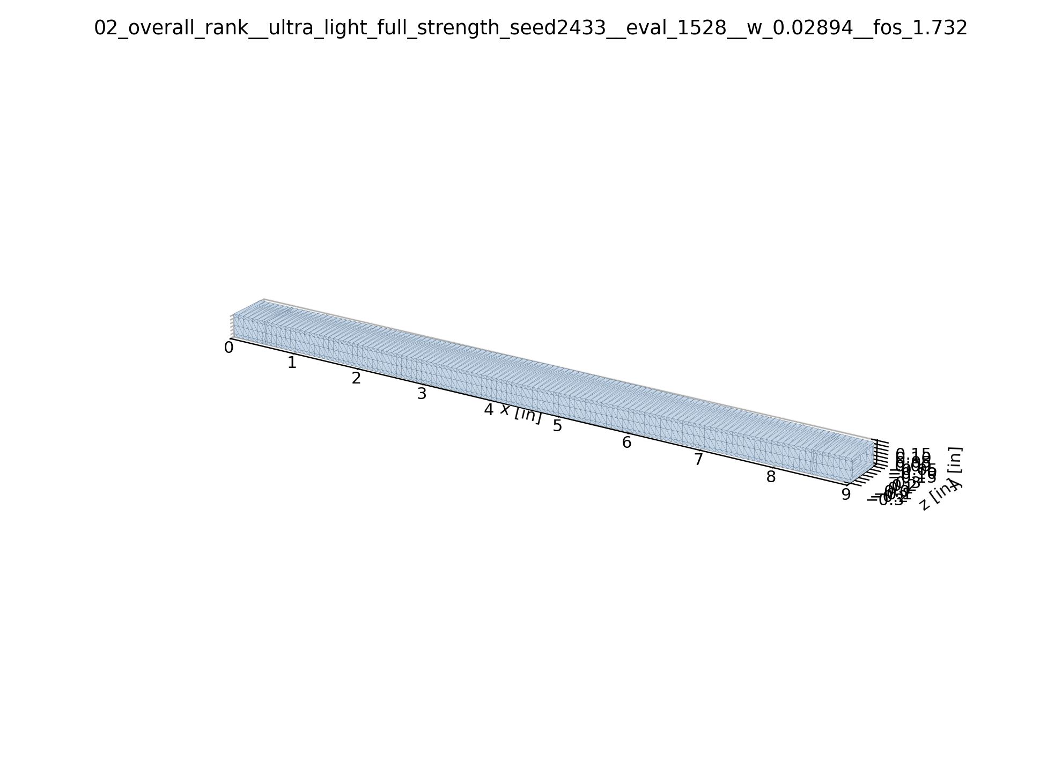
best-designs-20/3d-models/02_overall_rank__ultra_light_full_strength_seed2433__eval_1528__w_0.02894__fos_1.732_preview.png
