NikhilVeeram/MEEN-305-FINAL/best-designs-20/design-packages/02_overall_rank__ultra_light_full_strength_seed2433__eval_1528__w_0.02894__fos_1.732/best_design/geometry_properties.png

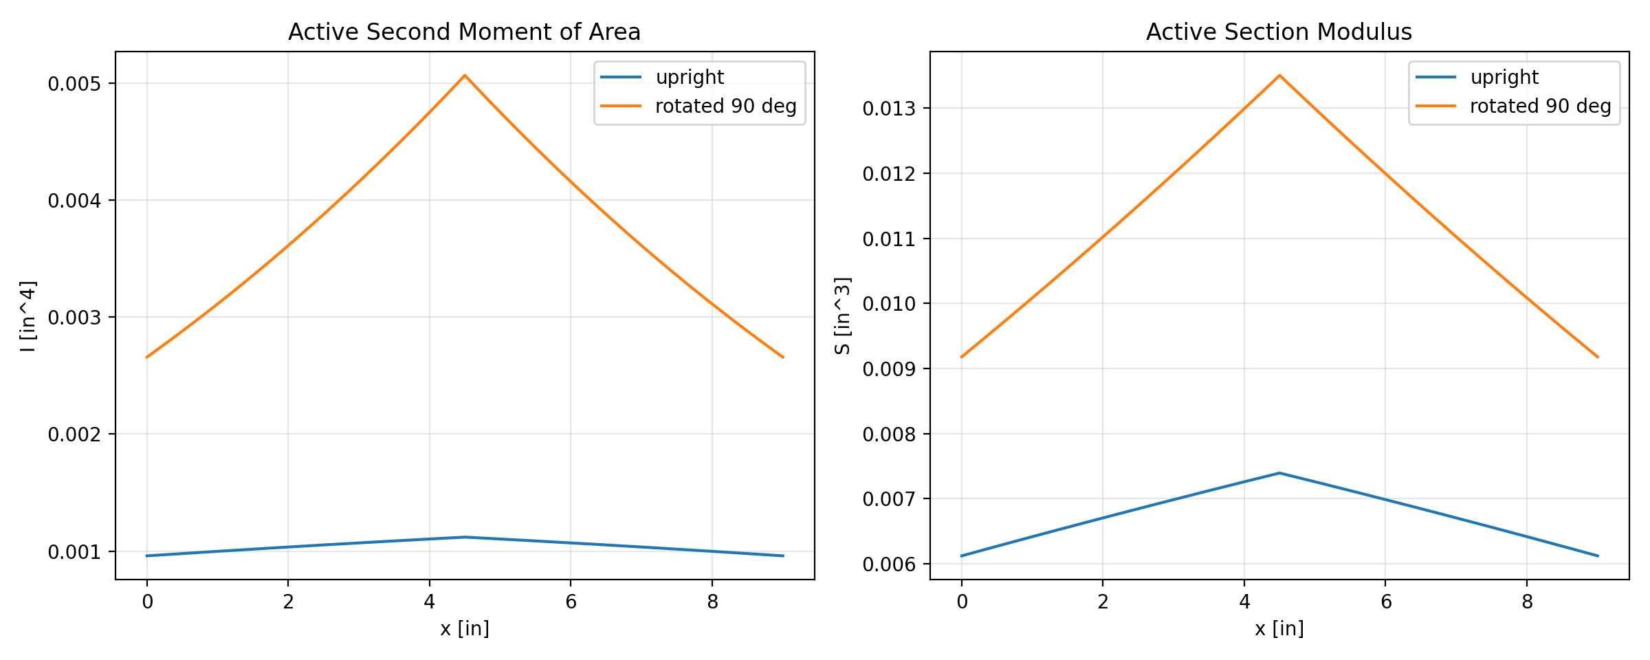
best-designs-20/design-packages/02_overall_rank__ultra_light_full_strength_seed2433__eval_1528__w_0.02894__fos_1.732/best_design/geometry_properties.png
