NikhilVeeram/MEEN-305-FINAL/best-designs-20/design-packages/03_overall_rank__ultra_light_run4_asymmetric_seed2427__eval_1102__w_0.02958__fos_2.116/best_design/geometry_properties.png

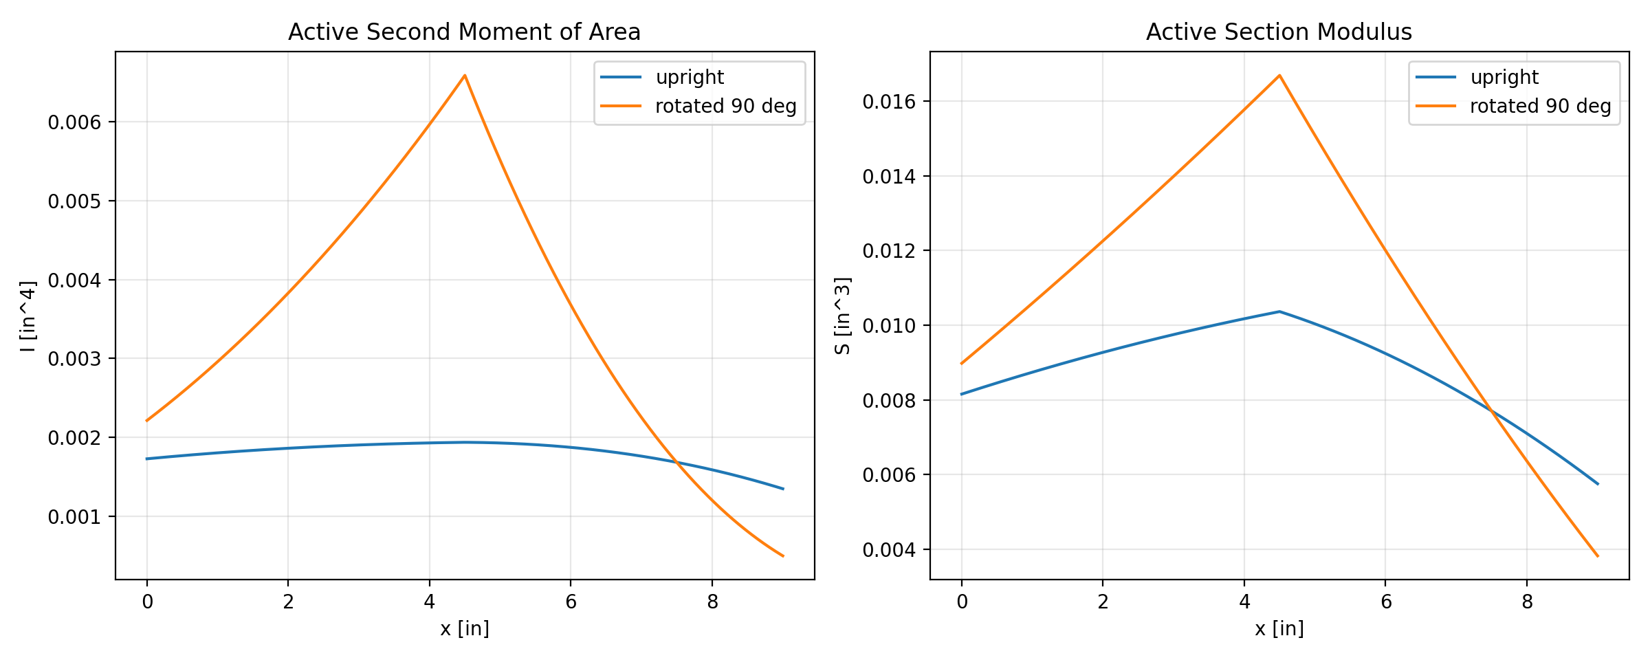
best-designs-20/design-packages/03_overall_rank__ultra_light_run4_asymmetric_seed2427__eval_1102__w_0.02958__fos_2.116/best_design/geometry_properties.png
