NikhilVeeram/MEEN-305-FINAL/best-designs-20/design-packages/04_overall_rank__ultra_light_full_strength_seed2433__eval_2458__w_0.02971__fos_1.562/beam_parameter_map.png

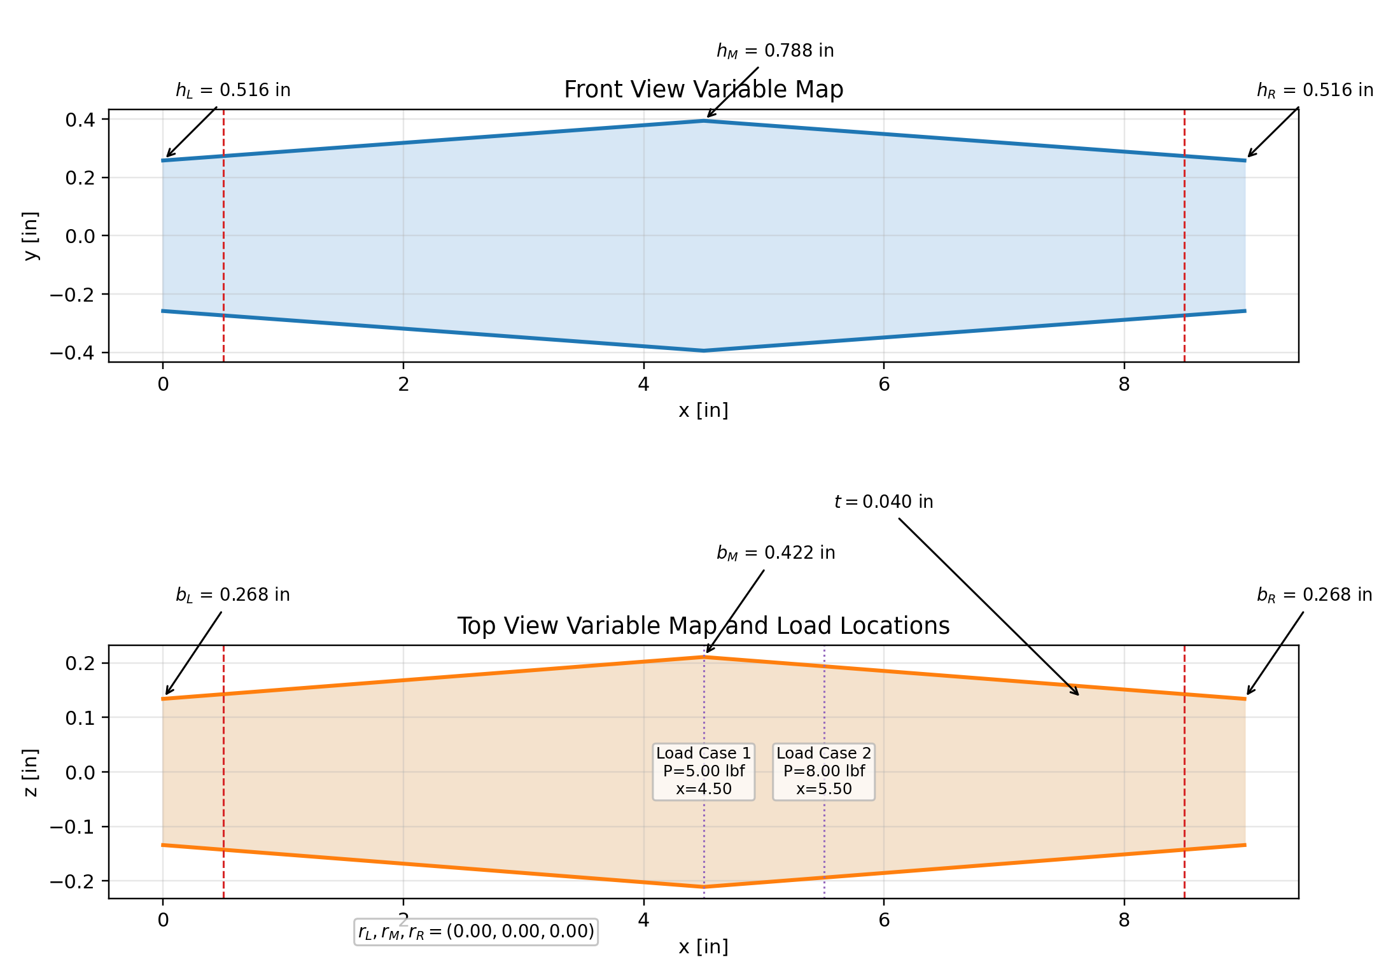
best-designs-20/design-packages/04_overall_rank__ultra_light_full_strength_seed2433__eval_2458__w_0.02971__fos_1.562/beam_parameter_map.png
