NikhilVeeram/MEEN-305-FINAL/best-designs-20/design-packages/06_overall_rank__ultra_light_full_strength_seed2433__eval_1532__w_0.03127__fos_1.712/best_design/geometry_properties.png

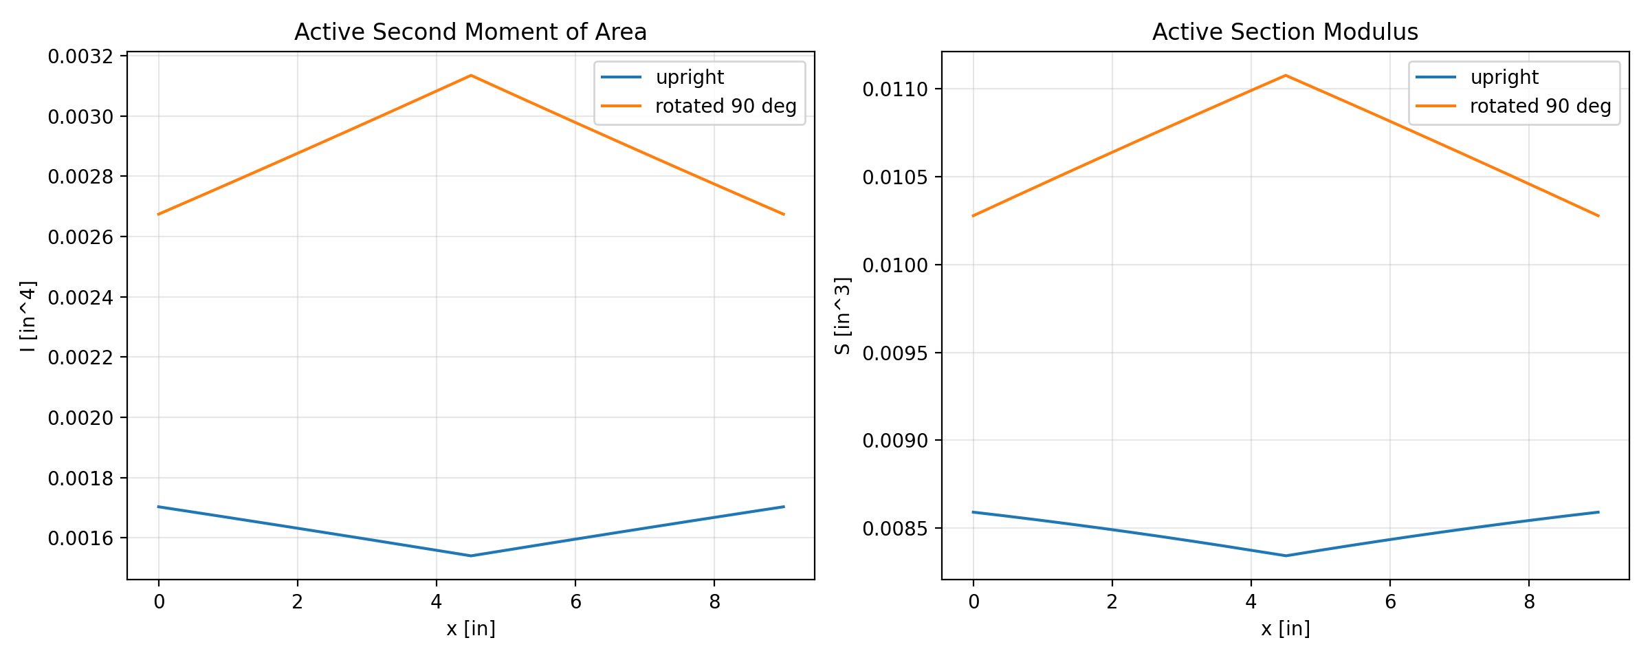
best-designs-20/design-packages/06_overall_rank__ultra_light_full_strength_seed2433__eval_1532__w_0.03127__fos_1.712/best_design/geometry_properties.png
