NikhilVeeram/MEEN-305-FINAL/best-designs-20/design-packages/07_overall_rank__ultra_light_full_infill_seed2432__eval_2497__w_0.03158__fos_1.751/beam_parameter_map.png

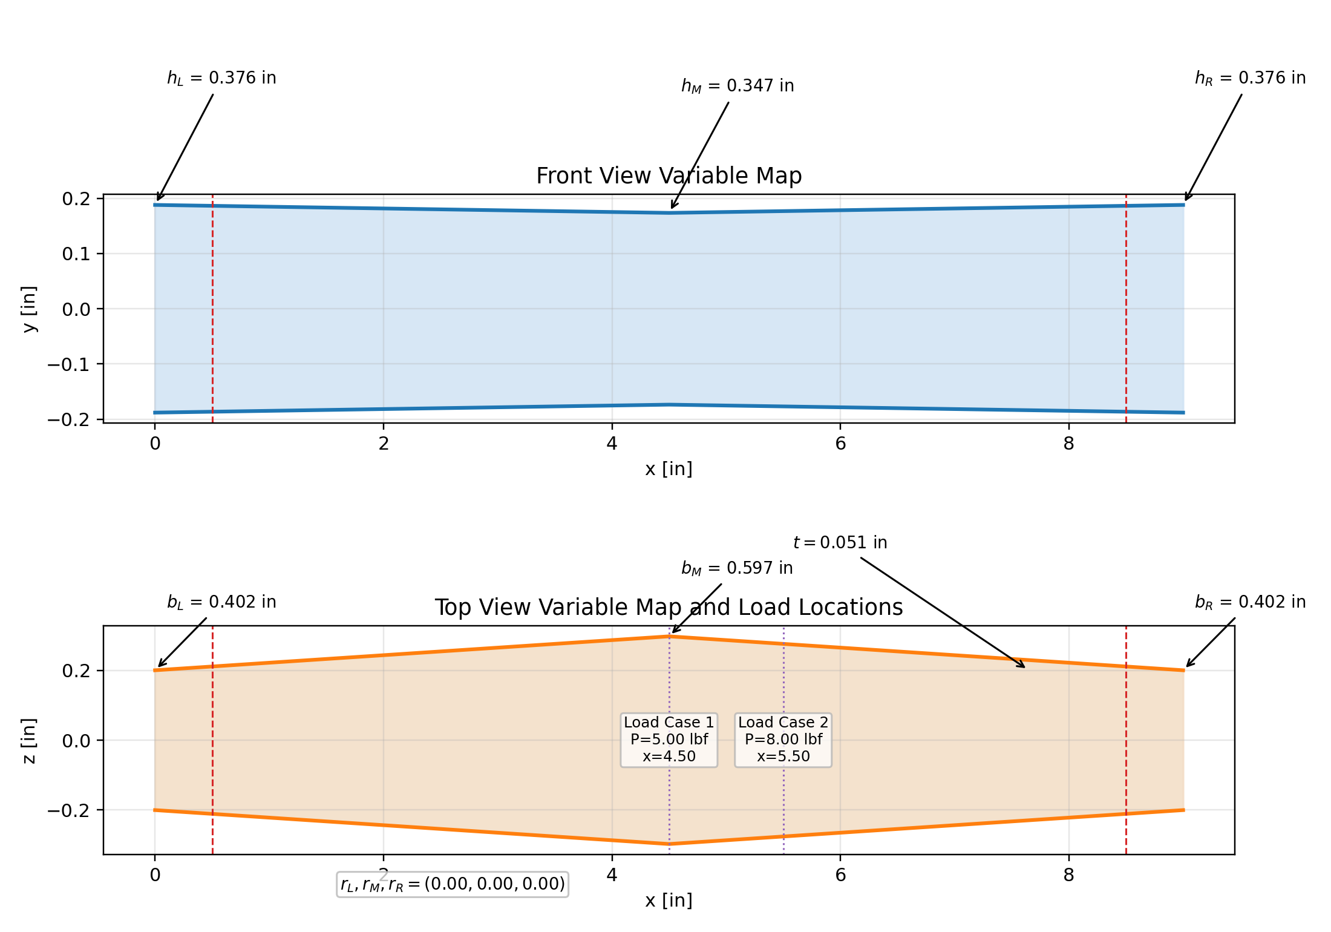
best-designs-20/design-packages/07_overall_rank__ultra_light_full_infill_seed2432__eval_2497__w_0.03158__fos_1.751/beam_parameter_map.png
