NikhilVeeram/MEEN-305-FINAL/best-designs-20/design-packages/09_overall_rank__ultra_light_full_infill_seed2432__eval_2251__w_0.03329__fos_1.595/best_design/geometry_properties.png

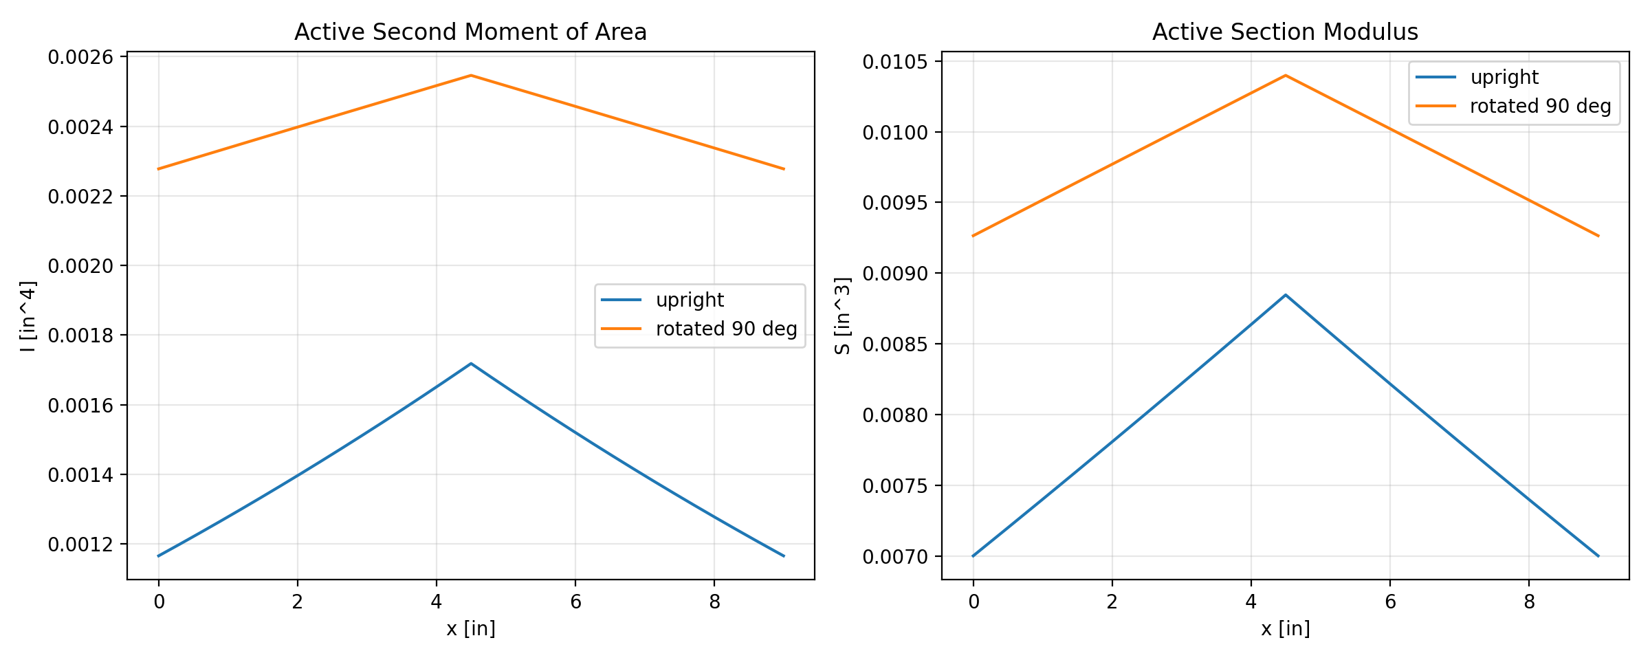
best-designs-20/design-packages/09_overall_rank__ultra_light_full_infill_seed2432__eval_2251__w_0.03329__fos_1.595/best_design/geometry_properties.png
