NikhilVeeram/MEEN-305-FINAL/best-designs-20/design-packages/10_overall_rank__ultra_light_full_infill_seed2432__eval_2514__w_0.03483__fos_1.572/best_design/geometry_properties.png

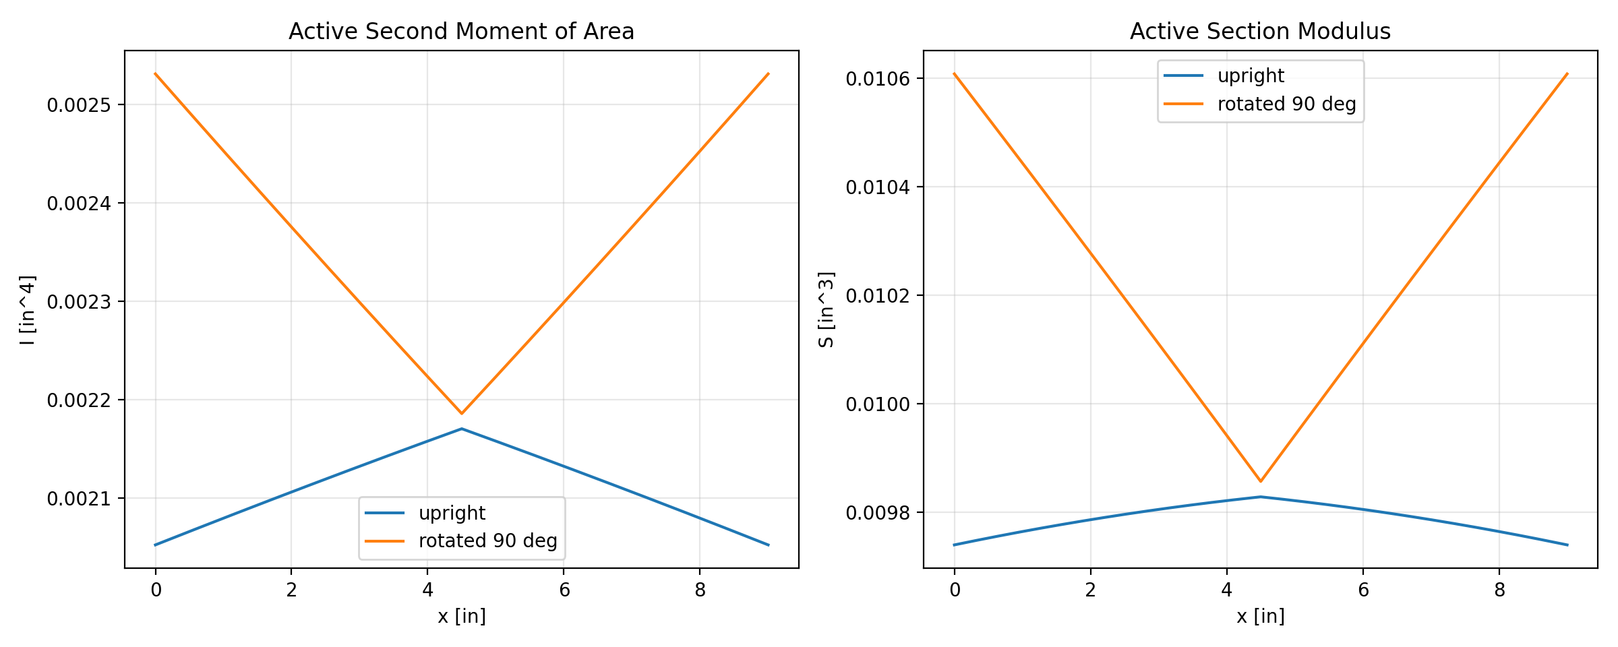
best-designs-20/design-packages/10_overall_rank__ultra_light_full_infill_seed2432__eval_2514__w_0.03483__fos_1.572/best_design/geometry_properties.png
