NikhilVeeram/MEEN-305-FINAL/best-designs-20/design-packages/12_overall_rank__continuous_uniform_both_load_cases_9in_corrected__eval_0680__w_0.03546__fos_2.902/best_design/geometry_properties.png

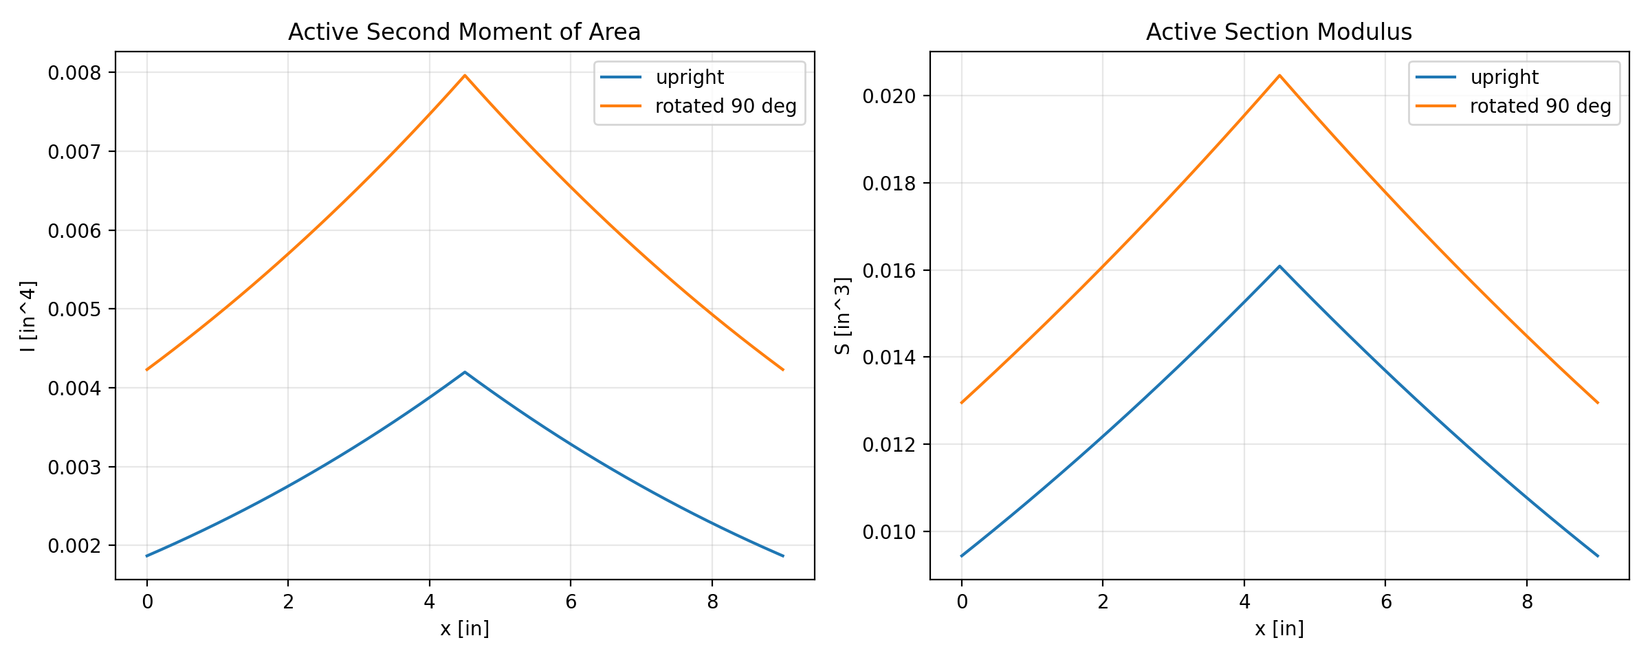
best-designs-20/design-packages/12_overall_rank__continuous_uniform_both_load_cases_9in_corrected__eval_0680__w_0.03546__fos_2.902/best_design/geometry_properties.png
