NikhilVeeram/MEEN-305-FINAL/best-designs-20/design-packages/14_overall_rank__continuous_uniform_both_load_cases_9in_corrected__eval_0402__w_0.03782__fos_2.022/best_design/geometry_properties.png

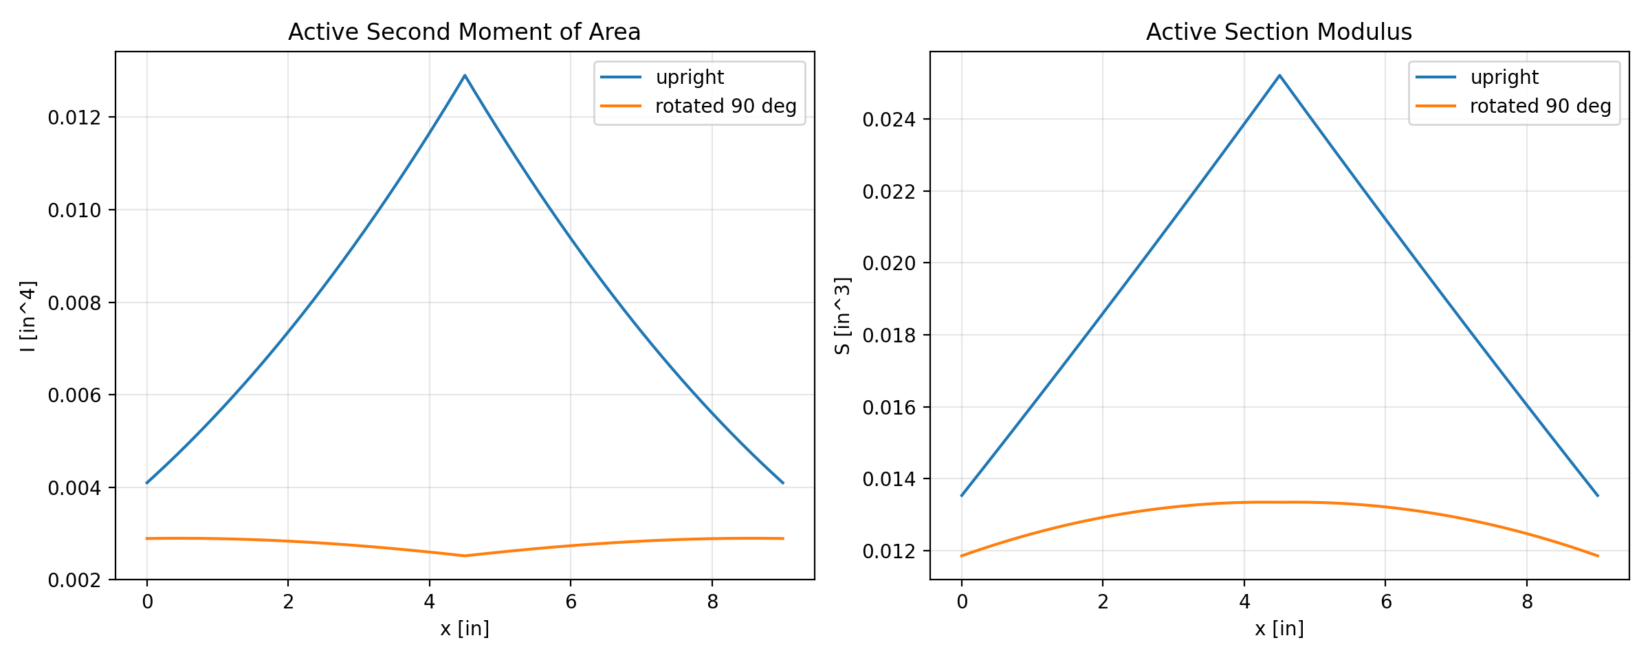
best-designs-20/design-packages/14_overall_rank__continuous_uniform_both_load_cases_9in_corrected__eval_0402__w_0.03782__fos_2.022/best_design/geometry_properties.png
