NikhilVeeram/MEEN-305-FINAL/best-designs-20/design-packages/17_overall_rank__print_safe_contiguous_closed_tube_seed2502__eval_1066__w_0.04048__fos_1.674/best_design/geometry_properties.png

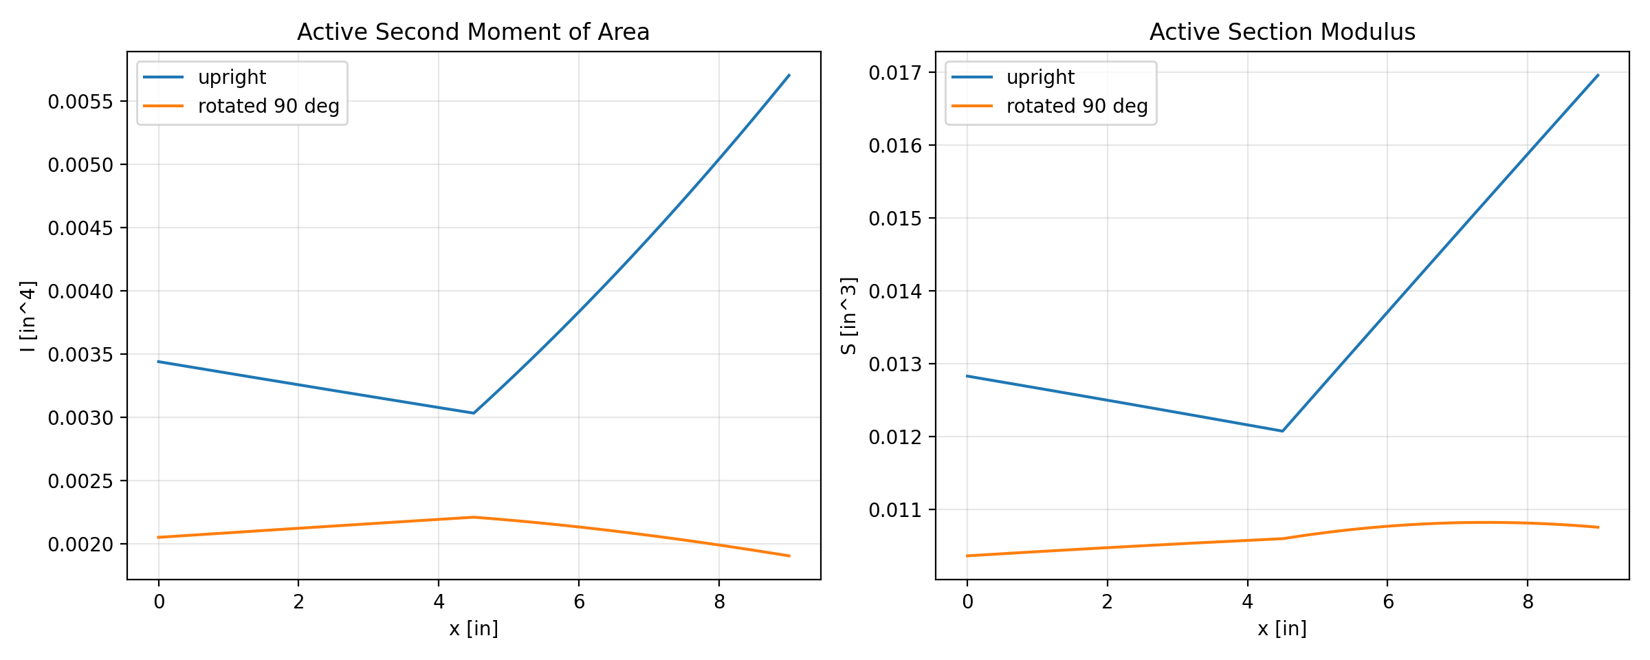
best-designs-20/design-packages/17_overall_rank__print_safe_contiguous_closed_tube_seed2502__eval_1066__w_0.04048__fos_1.674/best_design/geometry_properties.png
