NikhilVeeram/MEEN-305-FINAL/best-designs-20/design-packages/18_overall_rank__continuous_uniform_both_load_cases_9in_corrected__eval_0441__w_0.04079__fos_1.503/best_design/outer_dimension_views.png

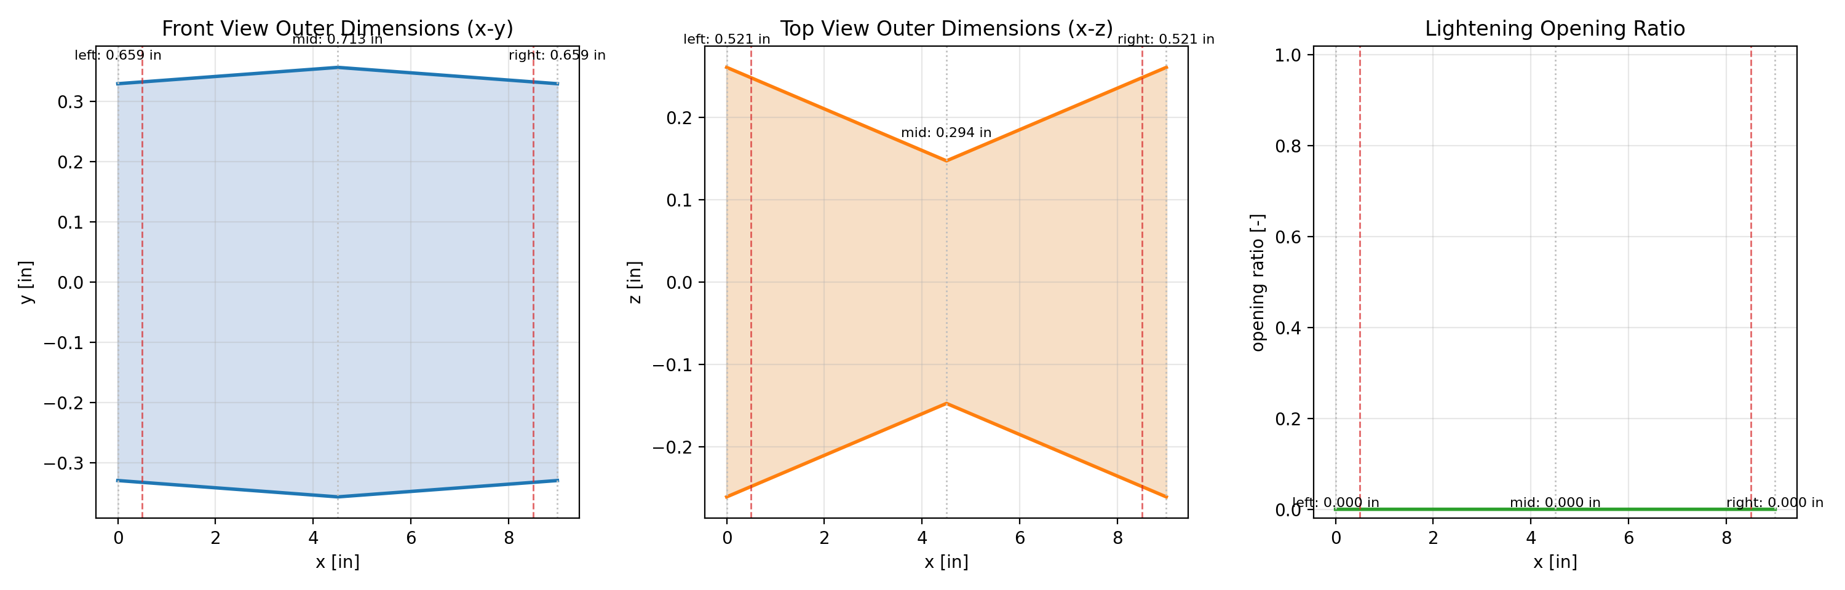
best-designs-20/design-packages/18_overall_rank__continuous_uniform_both_load_cases_9in_corrected__eval_0441__w_0.04079__fos_1.503/best_design/outer_dimension_views.png
