NikhilVeeram/MEEN-305-FINAL/best-designs-20/design-packages/19_overall_rank__ultra_light_full_infill_seed2432__eval_2513__w_0.04121__fos_1.565/beam_parameter_map.png

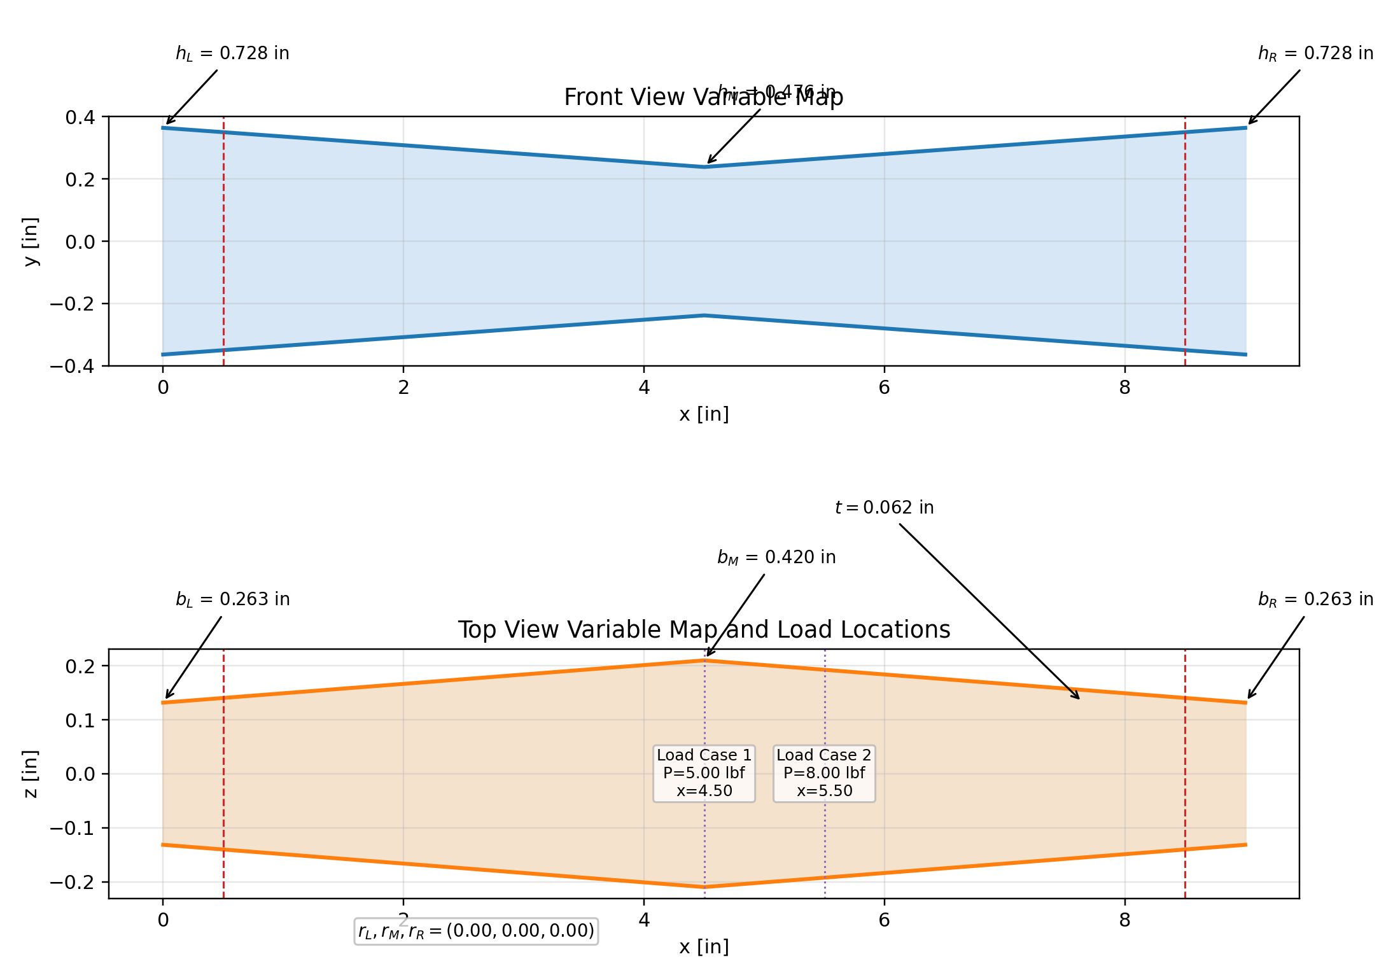
best-designs-20/design-packages/19_overall_rank__ultra_light_full_infill_seed2432__eval_2513__w_0.04121__fos_1.565/beam_parameter_map.png
