NikhilVeeram/MEEN-305-FINAL/best-designs-20/design-packages/20_overall_rank__ultra_light_run3_lowheight_seed2426__eval_1611__w_0.04175__fos_2.633/best_design/geometry_properties.png

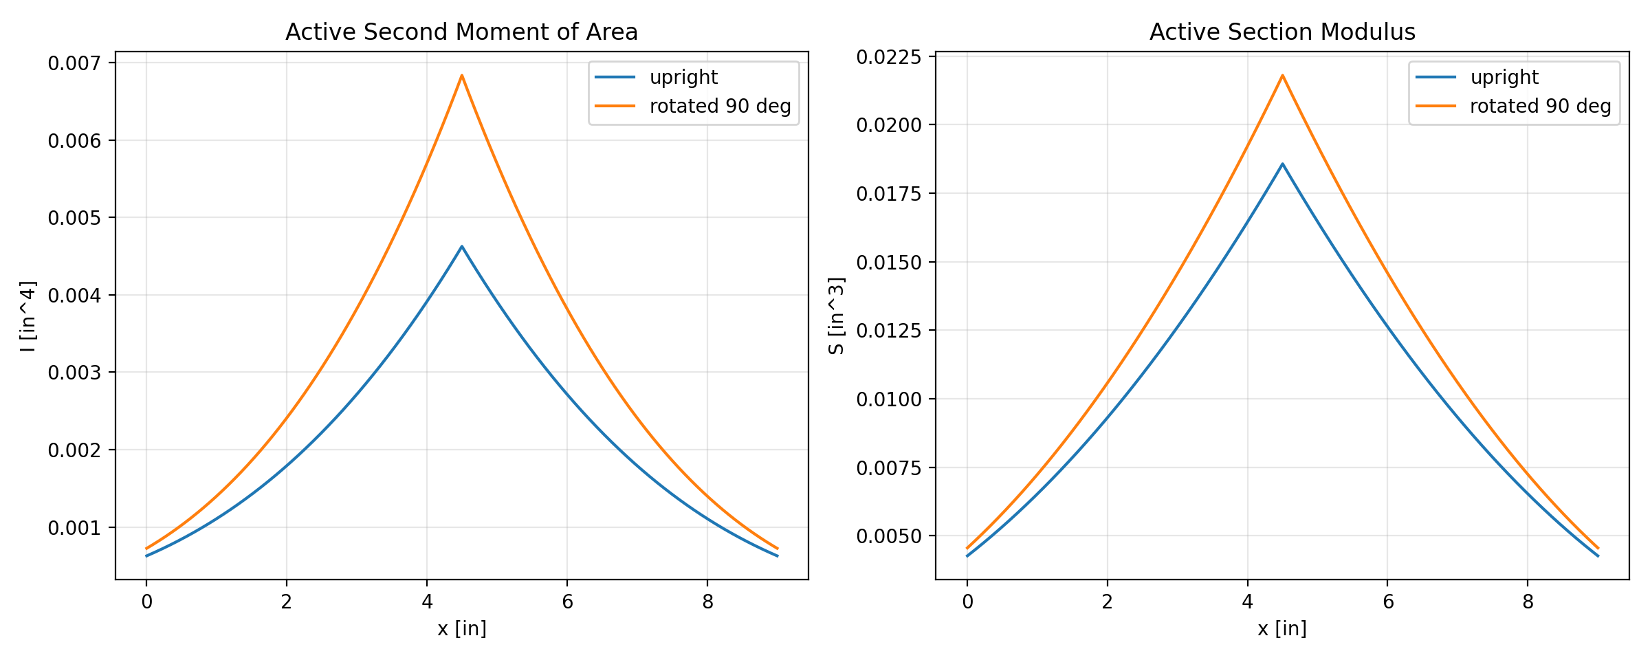
best-designs-20/design-packages/20_overall_rank__ultra_light_run3_lowheight_seed2426__eval_1611__w_0.04175__fos_2.633/best_design/geometry_properties.png
