NikhilVeeram/MEEN-305-FINAL/best-designs-20/ranked-designs/01_overall_rank__continuous_uniform_both_load_cases_9in_corrected__eval_0370__w_0.02815__fos_1.642/beam_parameter_map.png

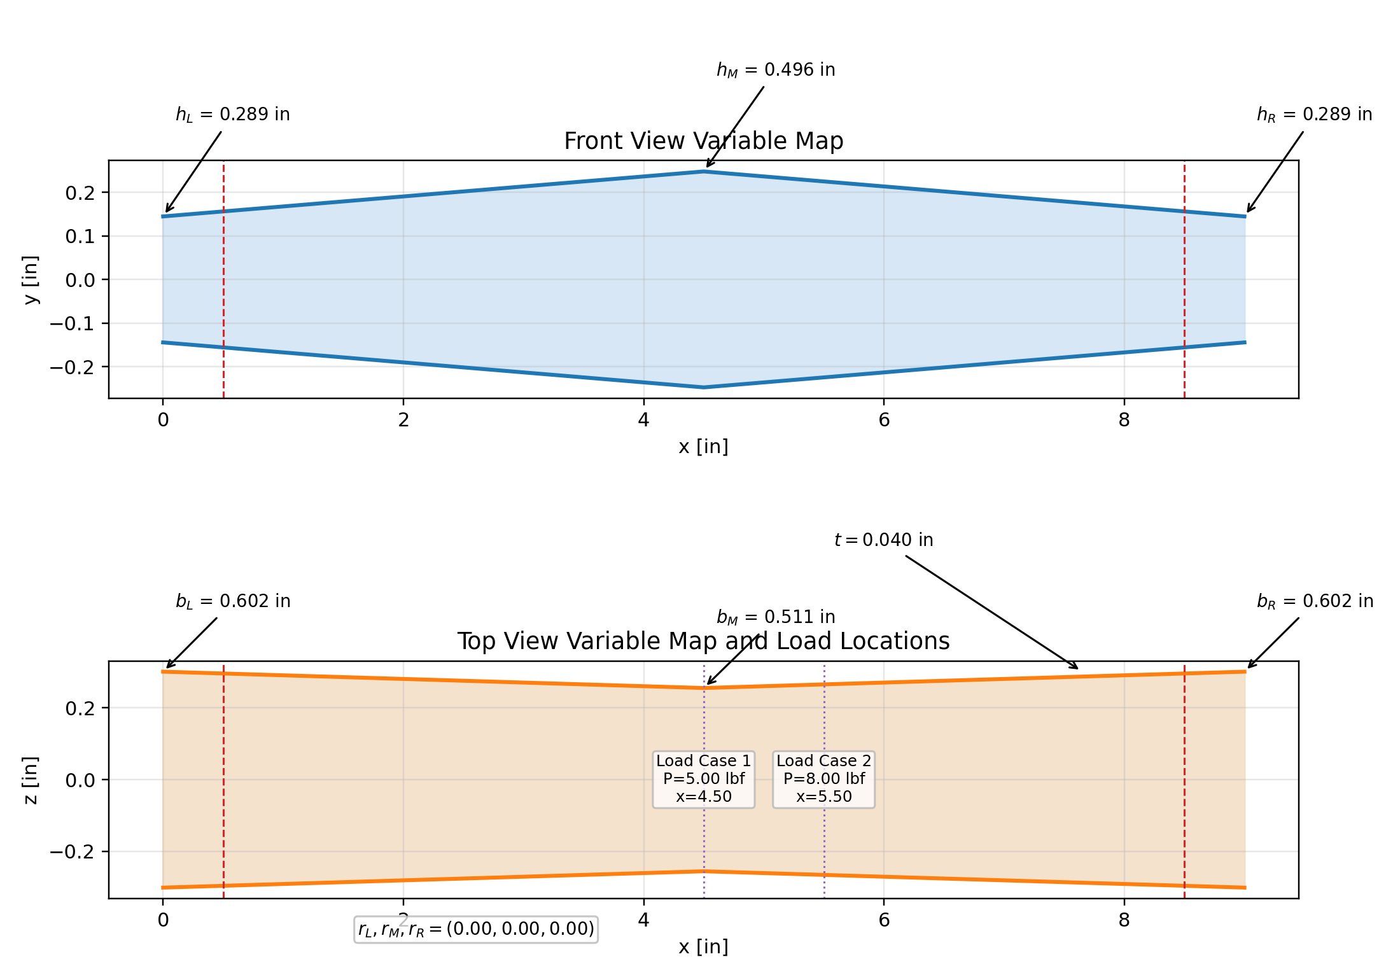
best-designs-20/ranked-designs/01_overall_rank__continuous_uniform_both_load_cases_9in_corrected__eval_0370__w_0.02815__fos_1.642/beam_parameter_map.png
