NikhilVeeram/MEEN-305-FINAL/best-designs-20/ranked-designs/05_overall_rank__ultra_light_full_infill_seed2432__eval_2924__w_0.03074__fos_1.789/beam_parameter_map.png

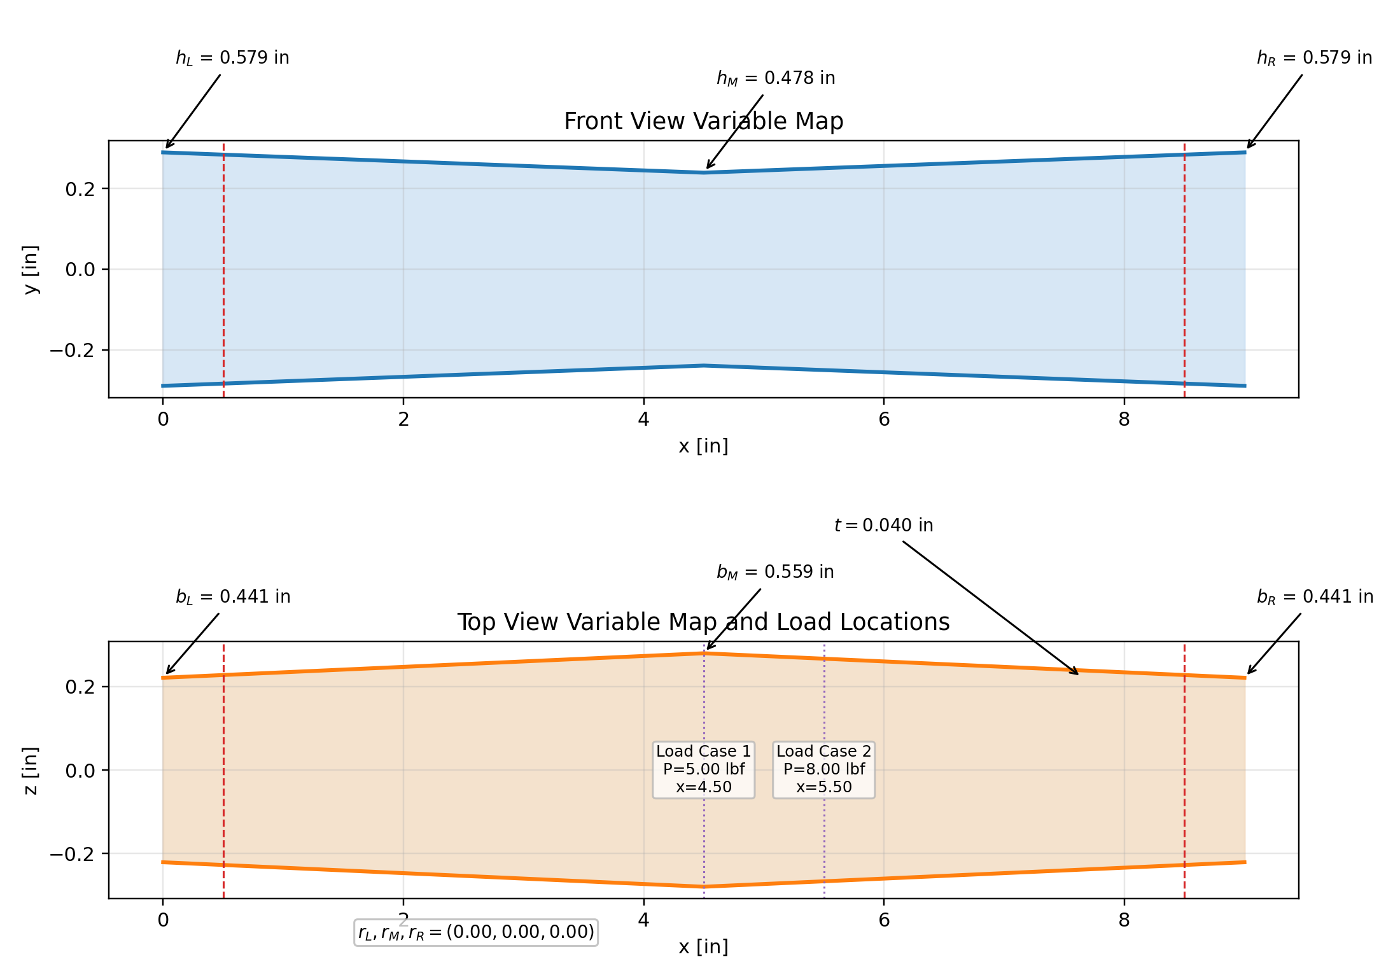
best-designs-20/ranked-designs/05_overall_rank__ultra_light_full_infill_seed2432__eval_2924__w_0.03074__fos_1.789/beam_parameter_map.png
