NikhilVeeram/MEEN-305-FINAL/best-designs-20/ranked-designs/07_overall_rank__ultra_light_full_infill_seed2432__eval_2497__w_0.03158__fos_1.751/best_design/geometry_properties.png

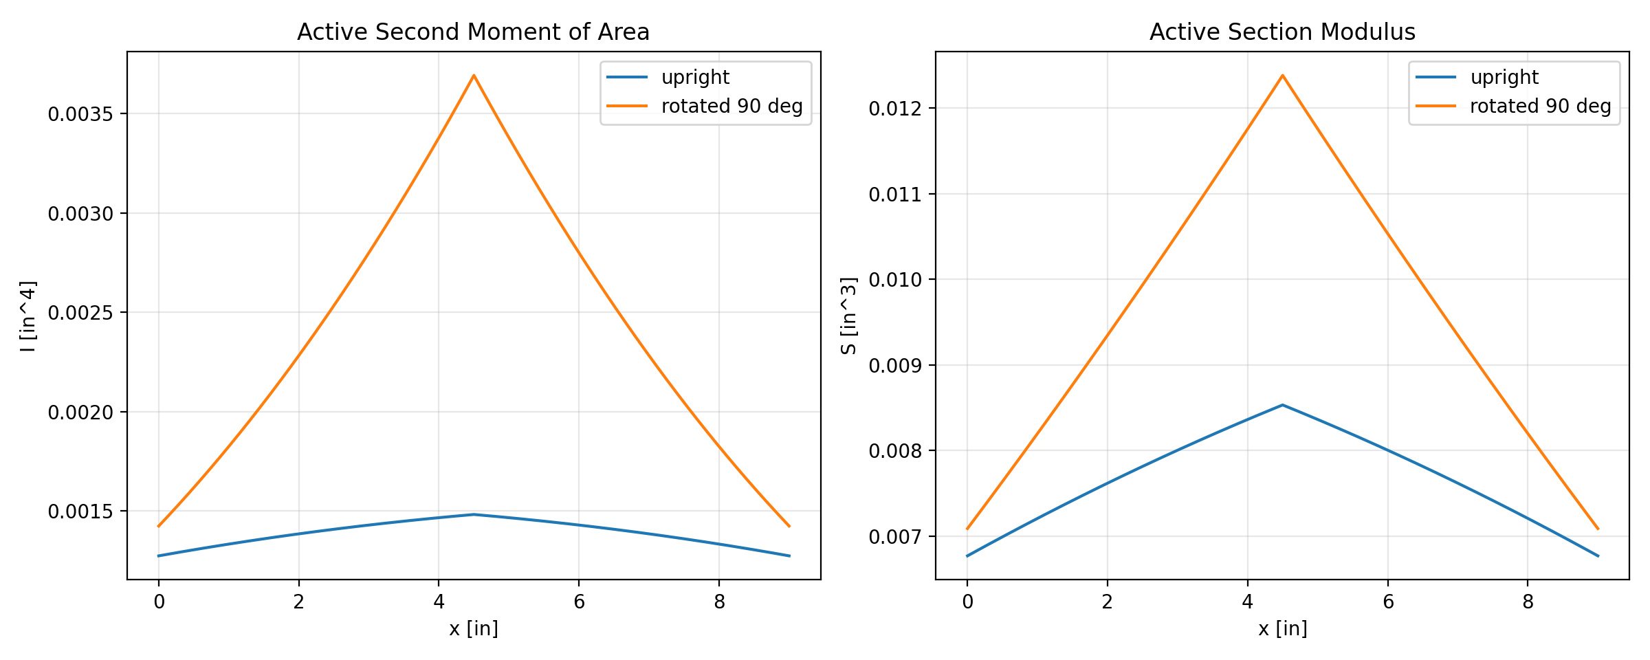
best-designs-20/ranked-designs/07_overall_rank__ultra_light_full_infill_seed2432__eval_2497__w_0.03158__fos_1.751/best_design/geometry_properties.png
