NikhilVeeram/MEEN-305-FINAL/best-designs-20/ranked-designs/08_overall_rank__ultra_light_full_infill_seed2432__eval_2852__w_0.03254__fos_1.713/beam_parameter_map.png

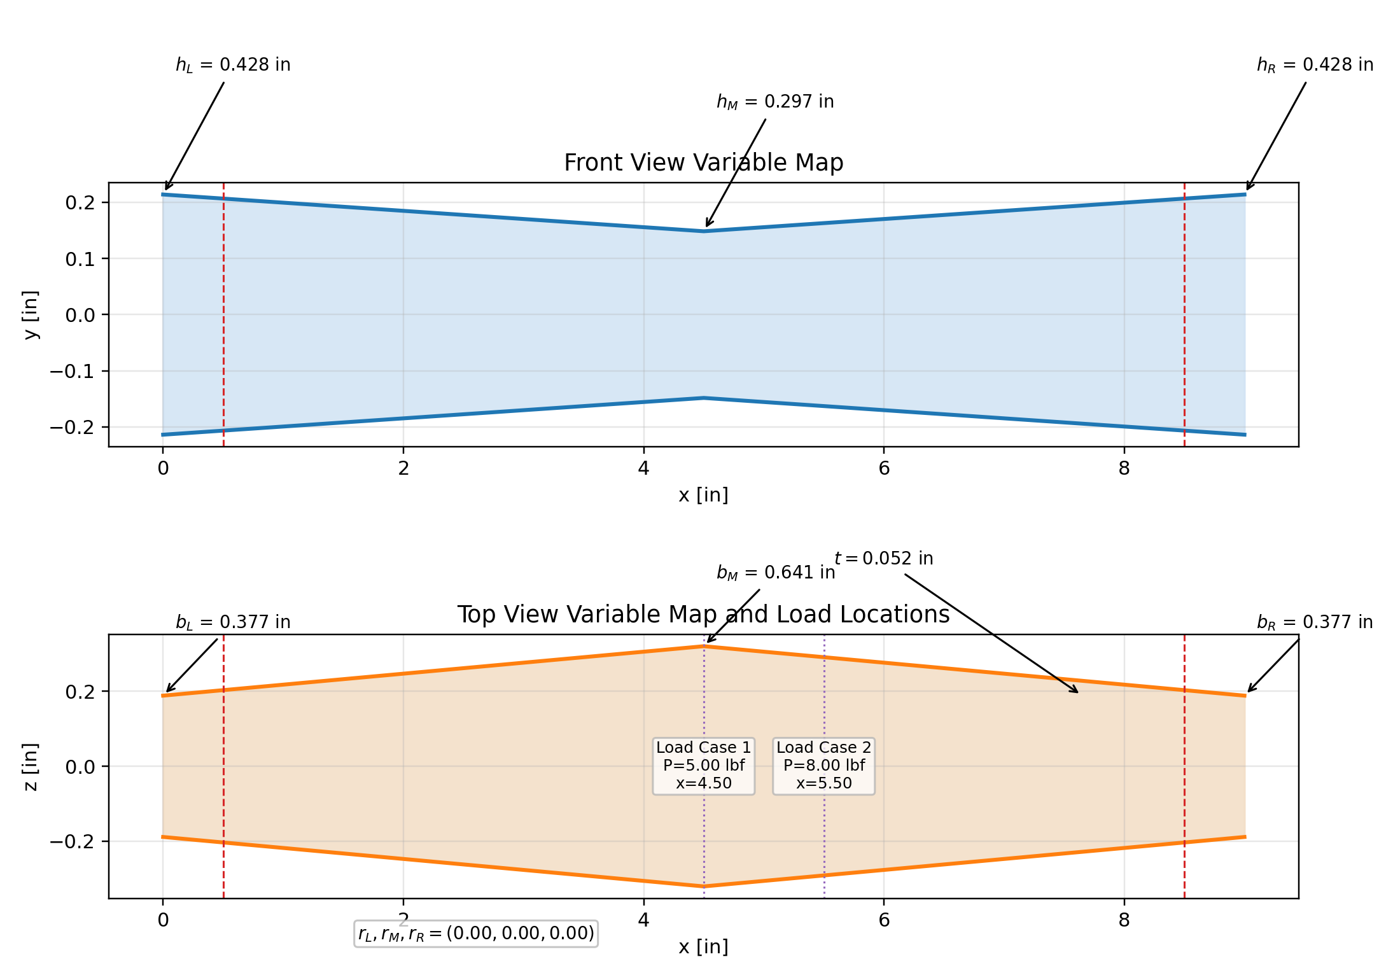
best-designs-20/ranked-designs/08_overall_rank__ultra_light_full_infill_seed2432__eval_2852__w_0.03254__fos_1.713/beam_parameter_map.png
