NikhilVeeram/MEEN-305-FINAL/best-designs-20/ranked-designs/14_overall_rank__continuous_uniform_both_load_cases_9in_corrected__eval_0402__w_0.03782__fos_2.022/best_design/outer_dimension_views.png

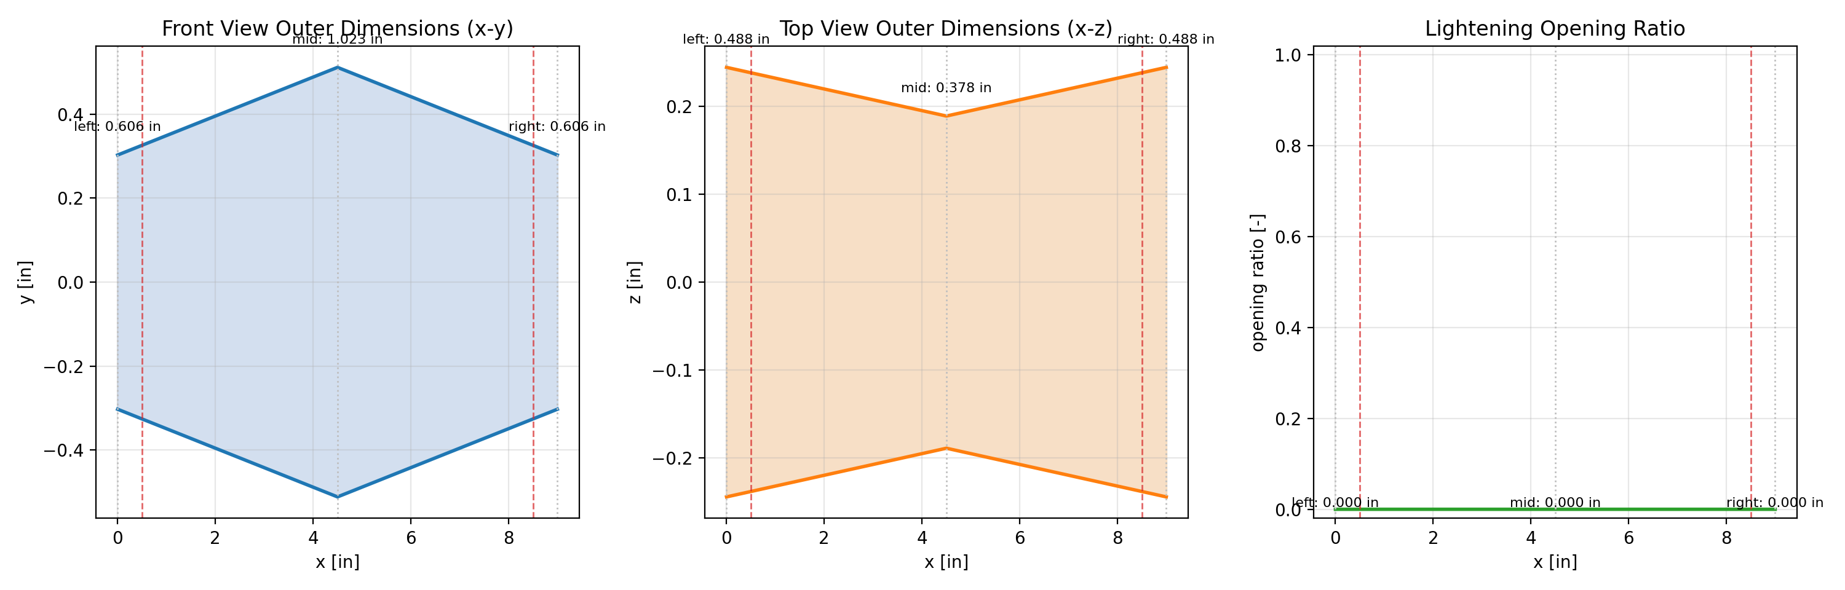
best-designs-20/ranked-designs/14_overall_rank__continuous_uniform_both_load_cases_9in_corrected__eval_0402__w_0.03782__fos_2.022/best_design/outer_dimension_views.png
