NikhilVeeram/MEEN-305-FINAL/best-designs-20/ranked-designs/15_overall_rank__continuous_uniform_both_load_cases_9in_corrected__eval_0364__w_0.03983__fos_1.695/best_design/geometry_properties.png

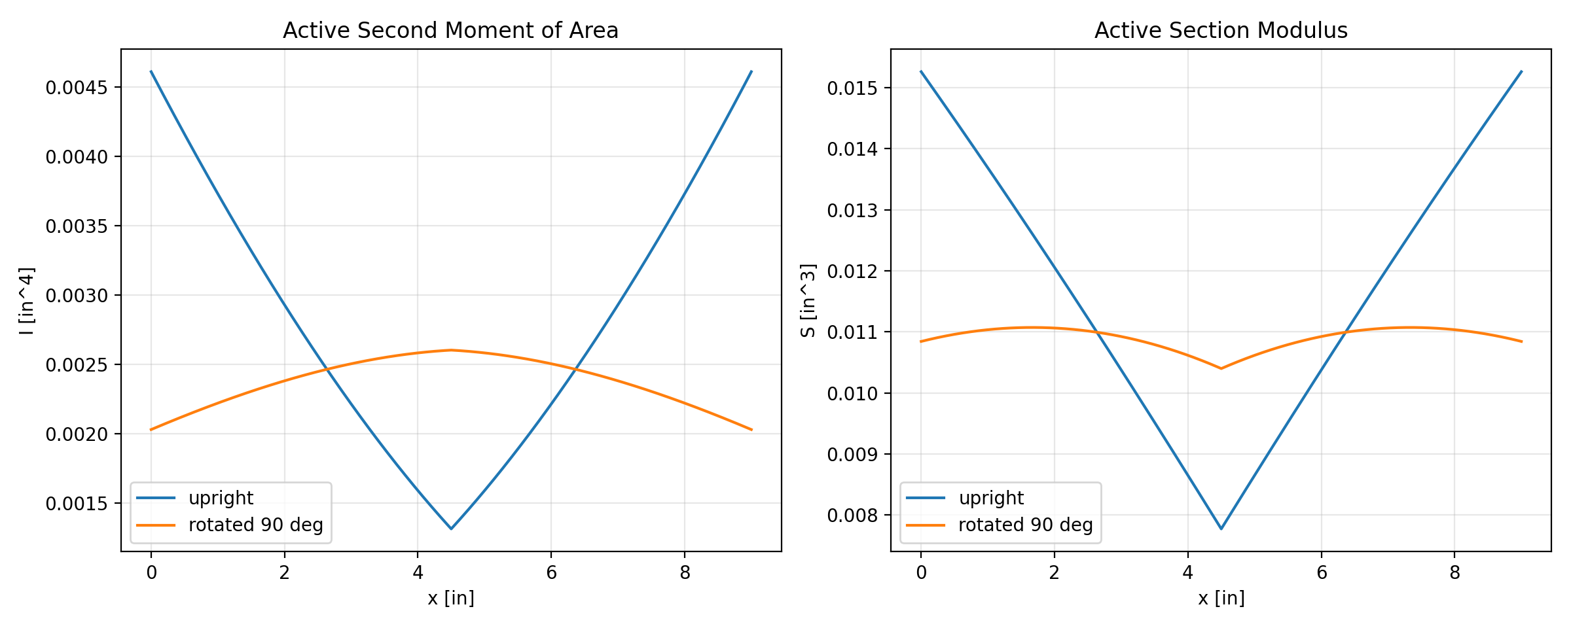
best-designs-20/ranked-designs/15_overall_rank__continuous_uniform_both_load_cases_9in_corrected__eval_0364__w_0.03983__fos_1.695/best_design/geometry_properties.png
