NikhilVeeram/MEEN-305-FINAL/best-designs-20/ranked-designs/18_overall_rank__continuous_uniform_both_load_cases_9in_corrected__eval_0441__w_0.04079__fos_1.503/best_design/geometry_properties.png

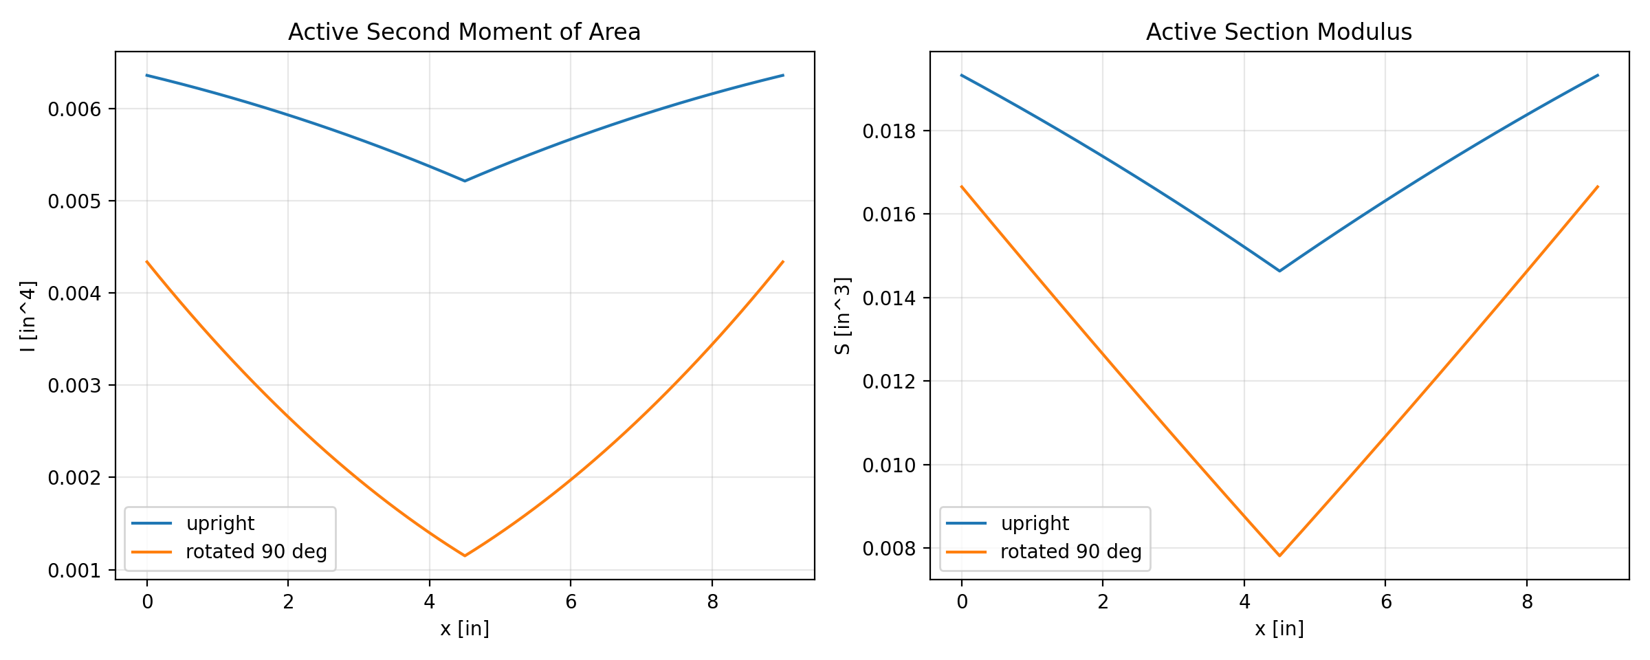
best-designs-20/ranked-designs/18_overall_rank__continuous_uniform_both_load_cases_9in_corrected__eval_0441__w_0.04079__fos_1.503/best_design/geometry_properties.png
