NikhilVeeram/MEEN-305-FINAL/designs/active_runs/continuous_uniform_both_load_cases/best_design/geometry_properties.png

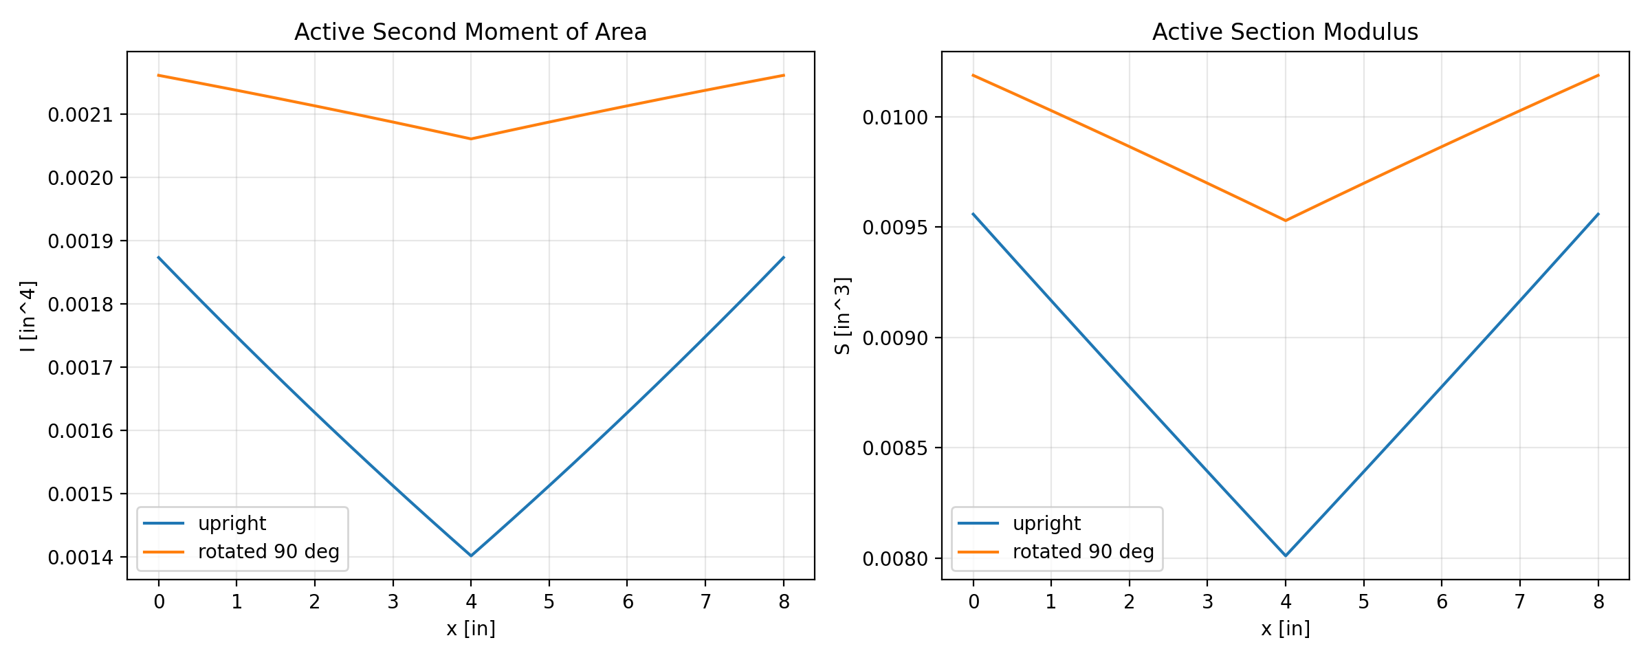
designs/active_runs/continuous_uniform_both_load_cases/best_design/geometry_properties.png
