NikhilVeeram/MEEN-305-FINAL/designs/active_runs/continuous_uniform_both_load_cases_9in_practical_buffer/best_design/geometry_properties.png

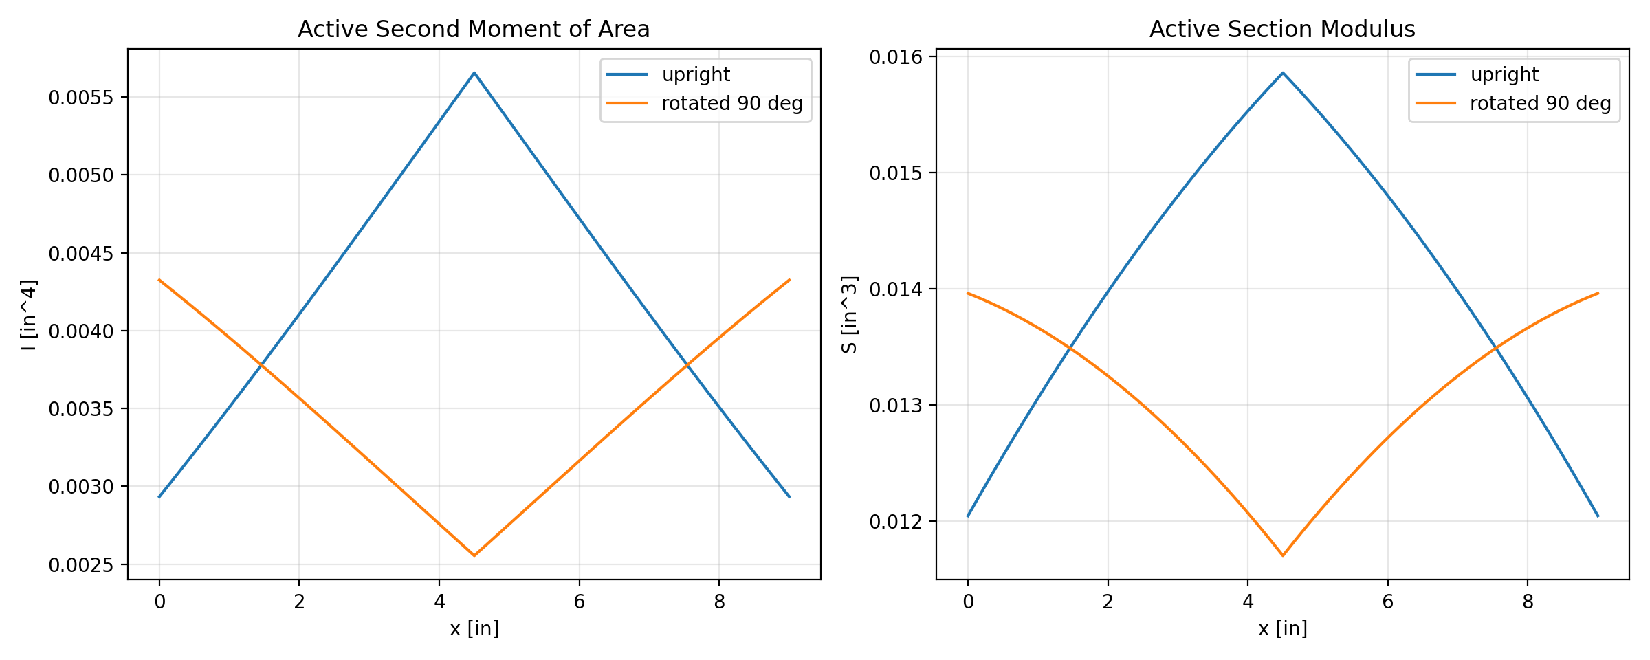
designs/active_runs/continuous_uniform_both_load_cases_9in_practical_buffer/best_design/geometry_properties.png
