NikhilVeeram/MEEN-305-FINAL/designs/active_runs/continuous_uniform_load_case_1/beam_parameter_map.png

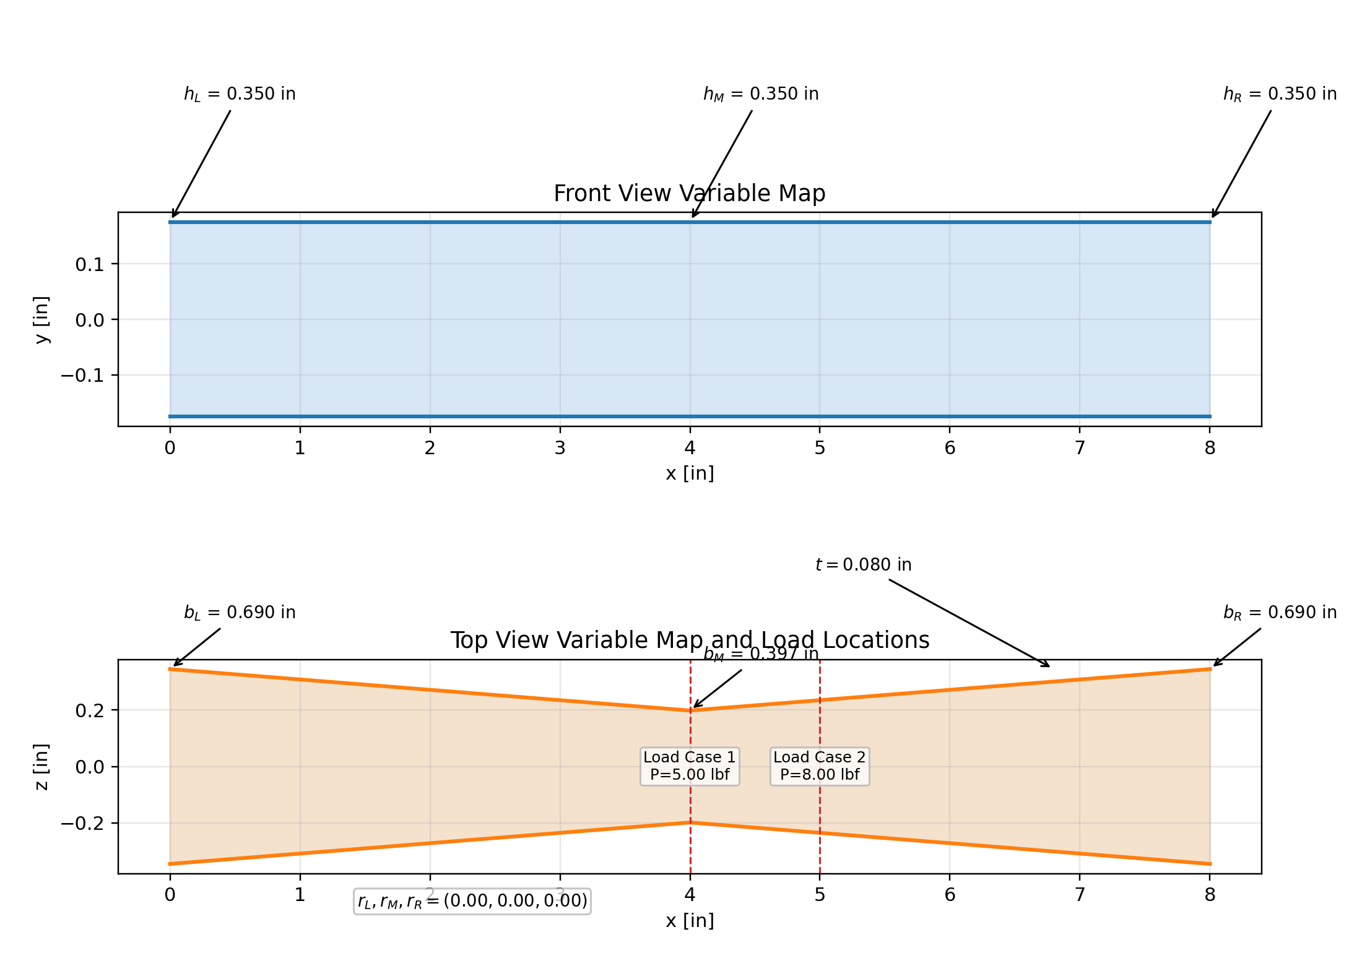
designs/active_runs/continuous_uniform_load_case_1/beam_parameter_map.png
