NikhilVeeram/MEEN-305-FINAL/designs/active_runs/continuous_uniform_load_case_1/best_design/outer_dimension_views.png

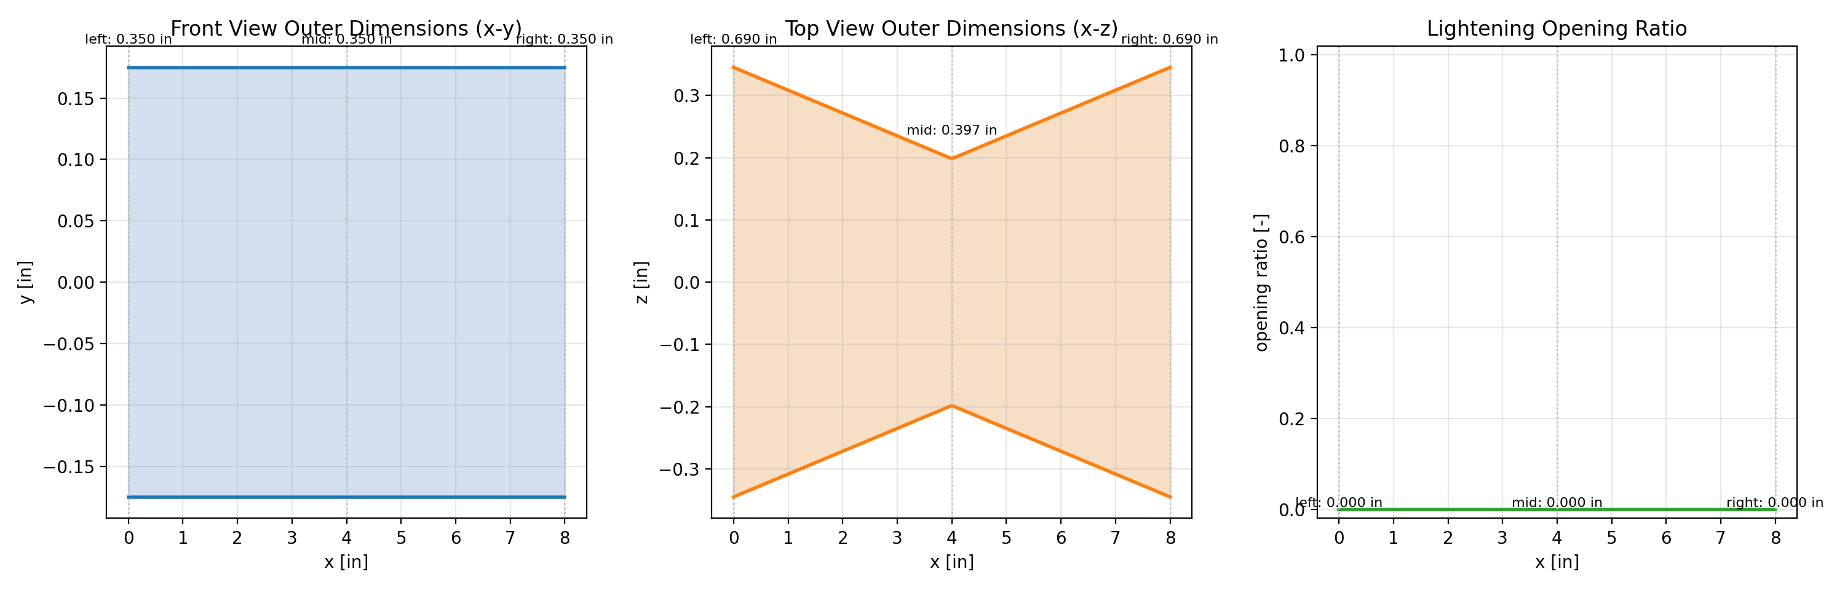
designs/active_runs/continuous_uniform_load_case_1/best_design/outer_dimension_views.png
