NikhilVeeram/MEEN-305-FINAL/designs/active_runs/continuous_uniform_load_case_2/beam_parameter_map.png

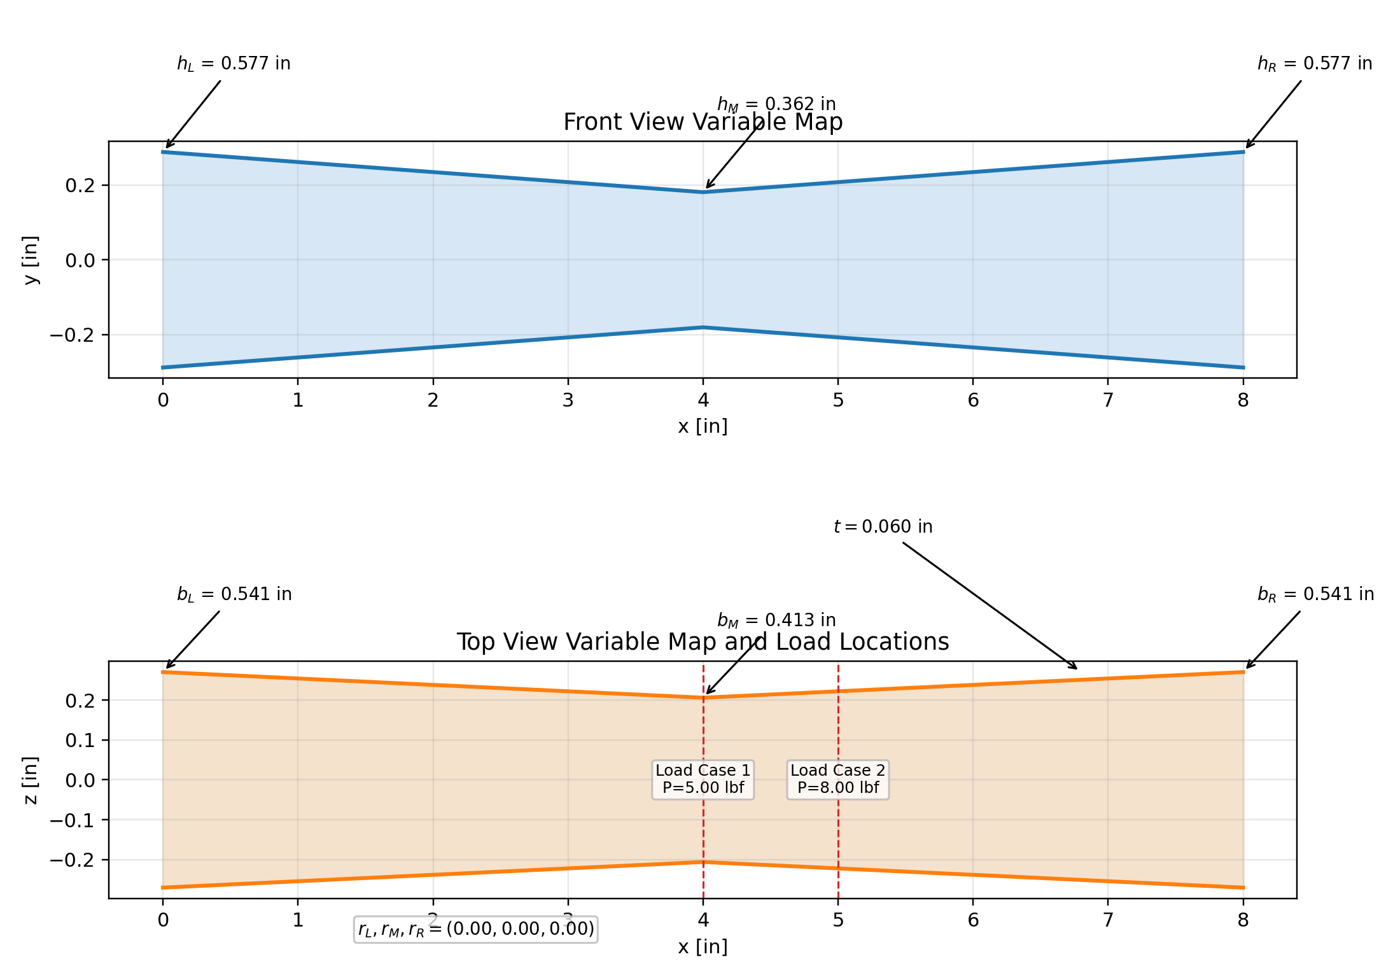
designs/active_runs/continuous_uniform_load_case_2/beam_parameter_map.png
