NikhilVeeram/MEEN-305-FINAL/designs/active_runs/flat_3to7_lc2_ranksearch_high_flatness_seed2404/beam_parameter_map.png

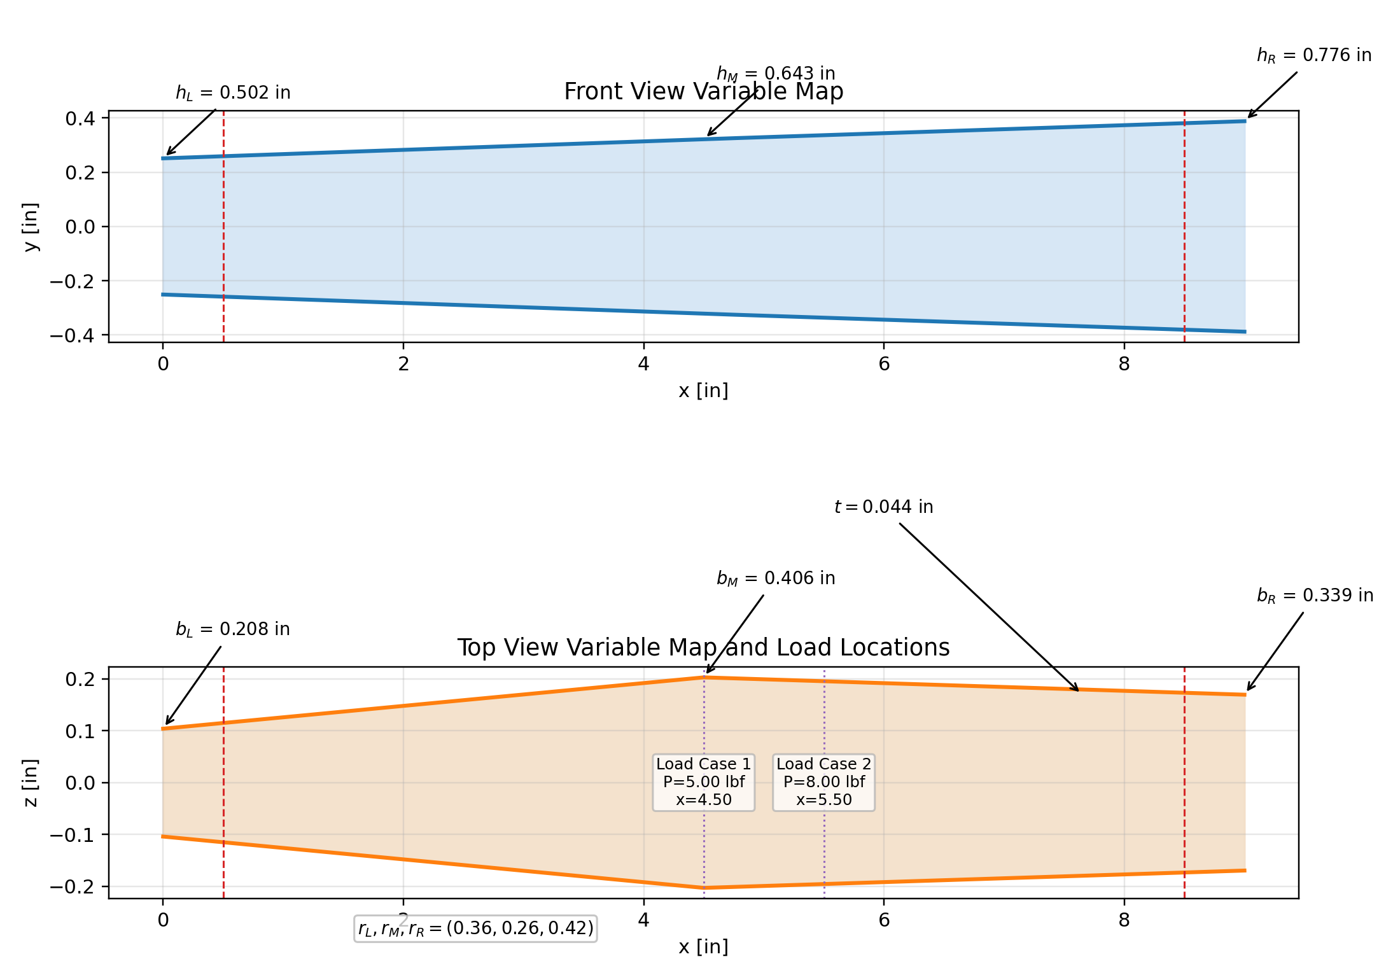
designs/active_runs/flat_3to7_lc2_ranksearch_high_flatness_seed2404/beam_parameter_map.png
