NikhilVeeram/MEEN-305-FINAL/designs/active_runs/flat_3to7_lc2_ranksearch_open_light_seed2401/best_design/geometry_properties.png

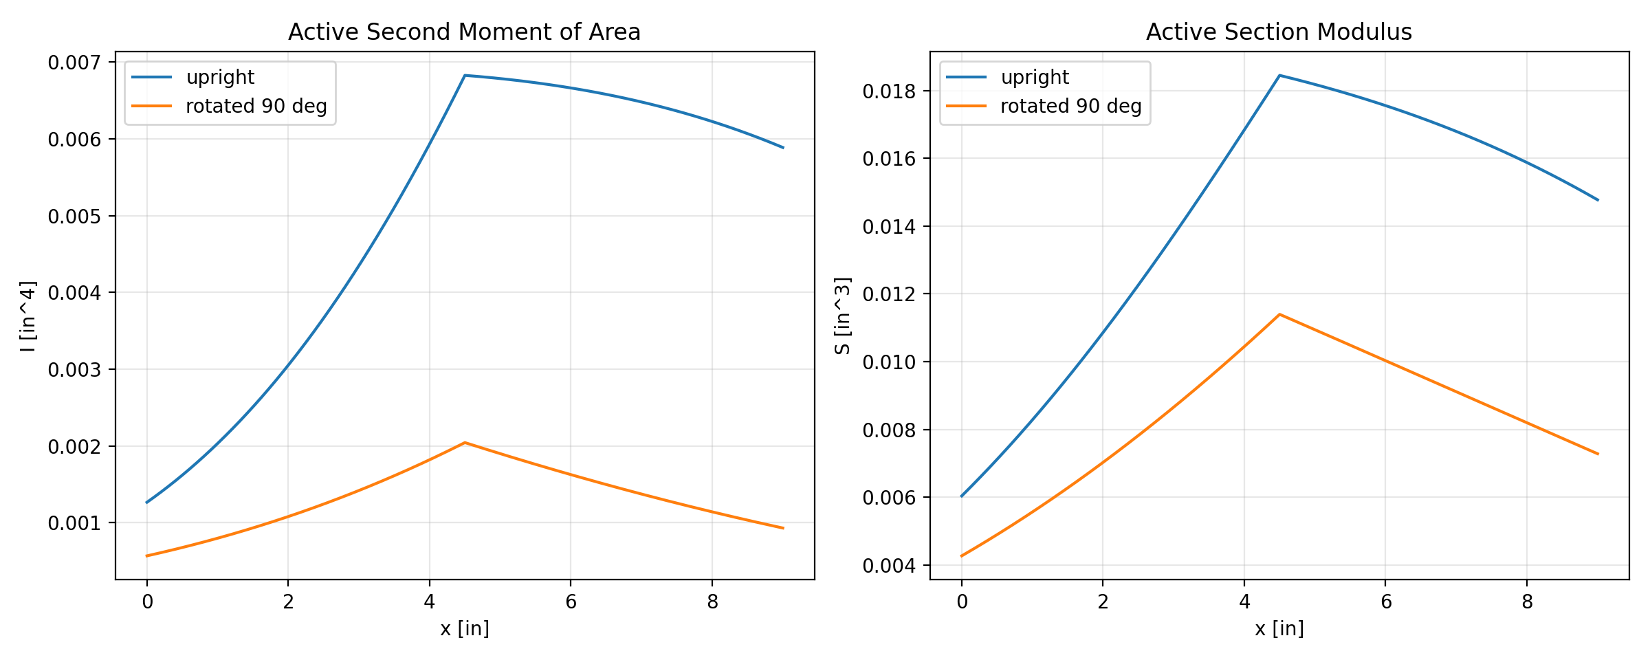
designs/active_runs/flat_3to7_lc2_ranksearch_open_light_seed2401/best_design/geometry_properties.png
