NikhilVeeram/MEEN-305-FINAL/designs/active_runs/flat_3to7_lc2_ranksearch_stiffer_seed2402/best_design/geometry_properties.png

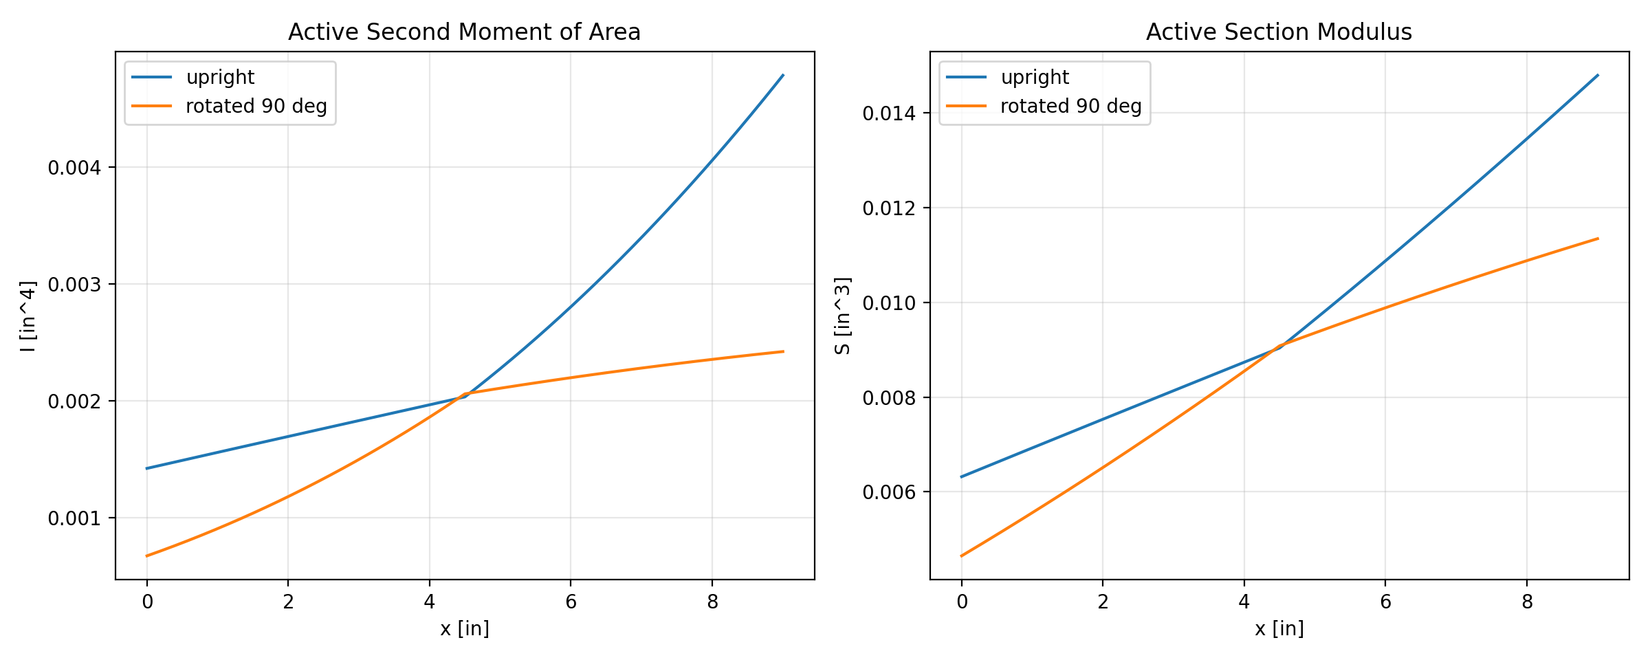
designs/active_runs/flat_3to7_lc2_ranksearch_stiffer_seed2402/best_design/geometry_properties.png
