NikhilVeeram/MEEN-305-FINAL/designs/active_runs/lc2_8lb_edge_support_trial_a/best_design/geometry_properties.png

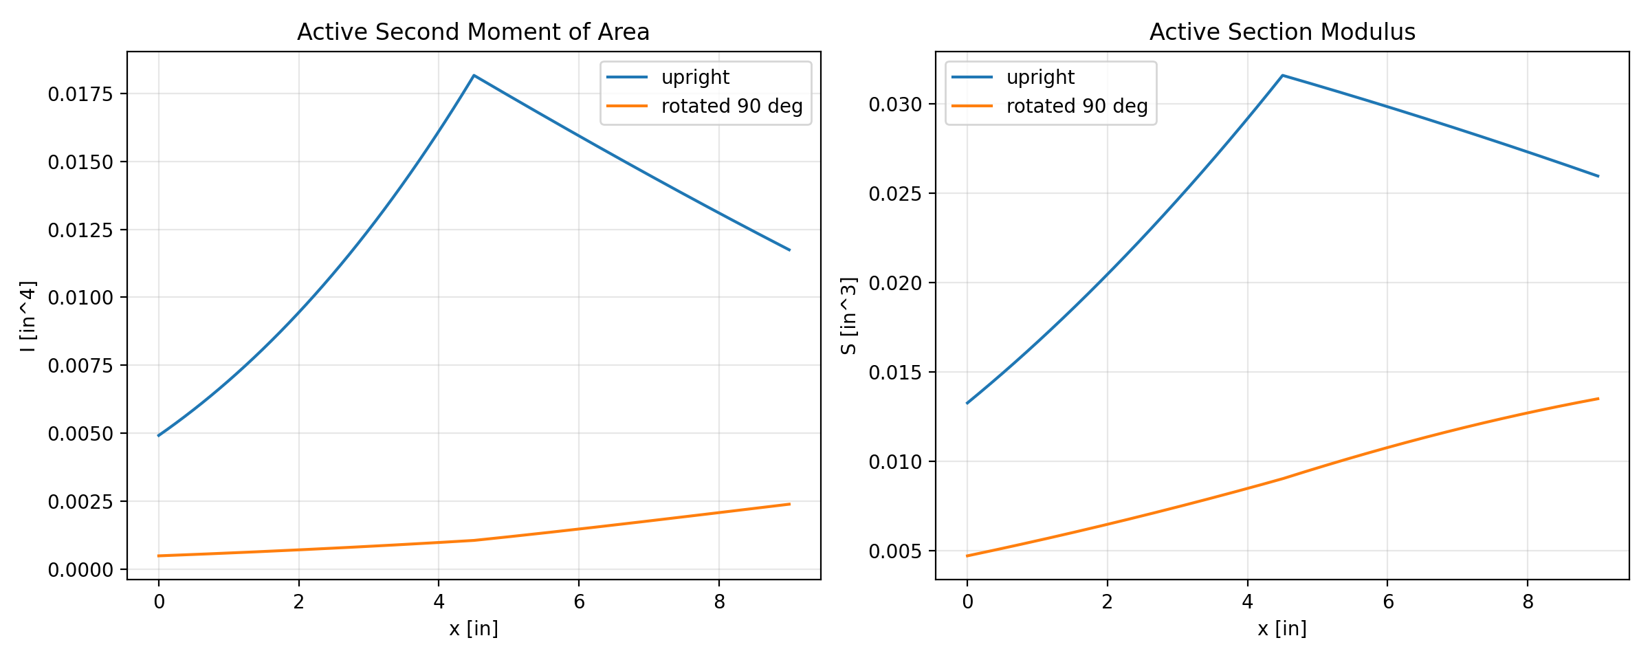
designs/active_runs/lc2_8lb_edge_support_trial_a/best_design/geometry_properties.png
