NikhilVeeram/MEEN-305-FINAL/designs/active_runs/print_safe_contiguous_low_opening_seed2501/best_design/outer_dimension_views.png

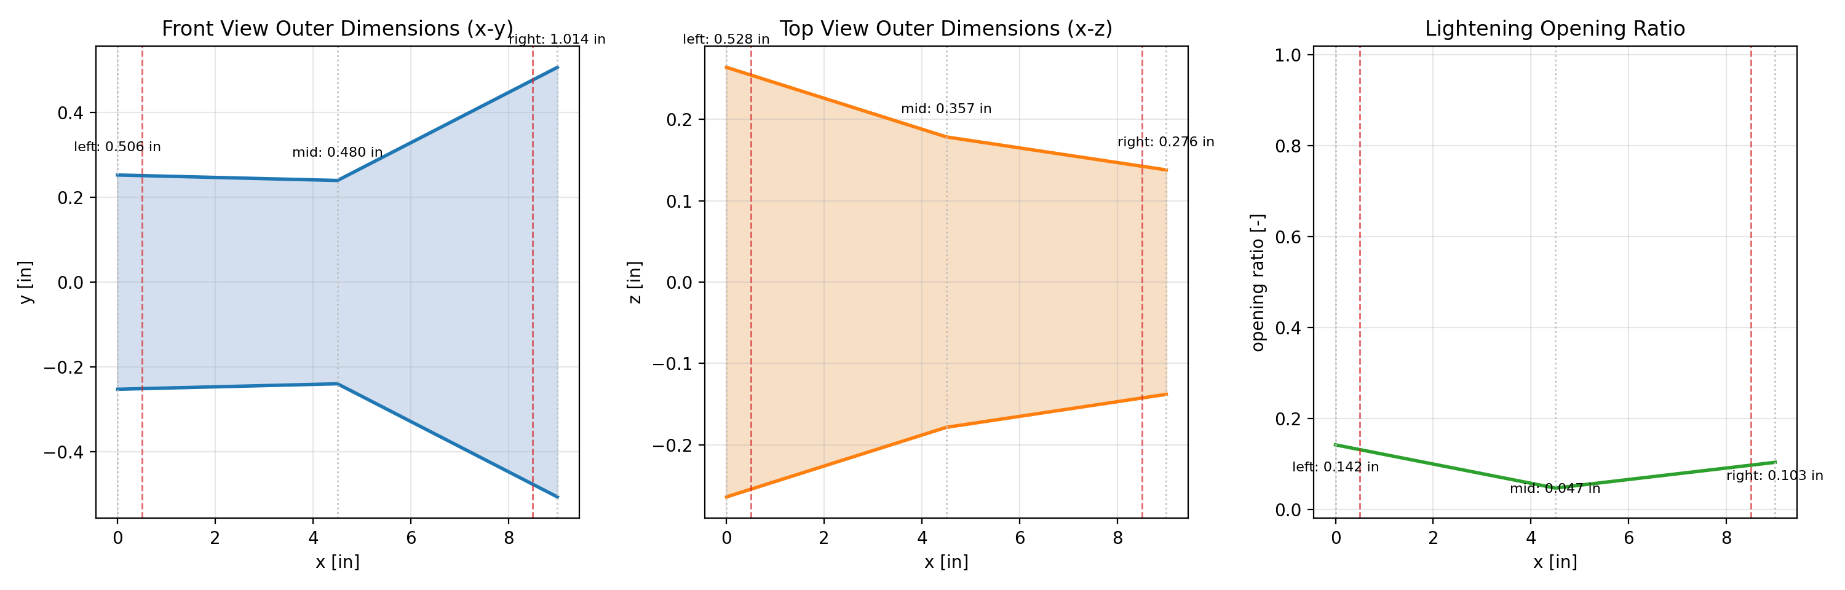
designs/active_runs/print_safe_contiguous_low_opening_seed2501/best_design/outer_dimension_views.png
