NikhilVeeram/MEEN-305-FINAL/designs/active_runs/print_safe_contiguous_stiff_seed2503/best_design/geometry_properties.png

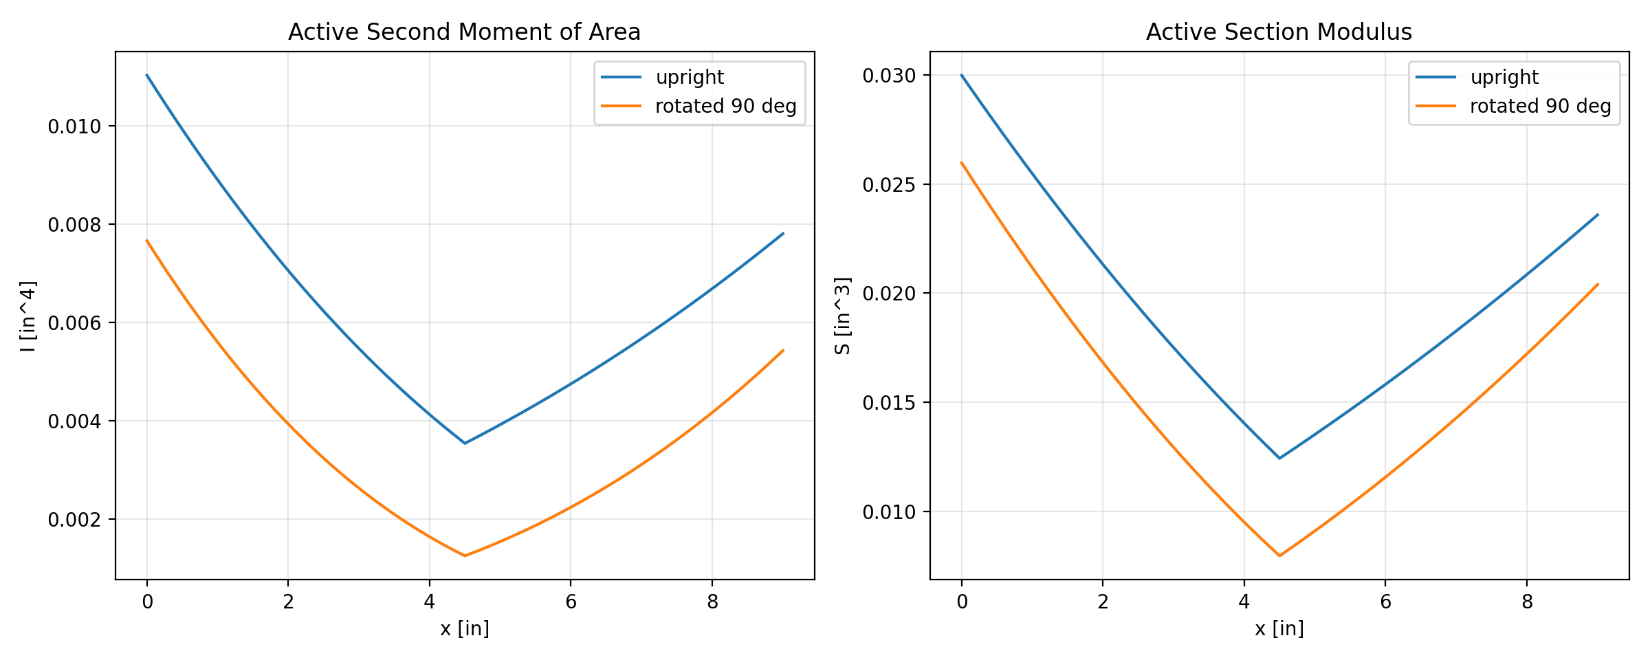
designs/active_runs/print_safe_contiguous_stiff_seed2503/best_design/geometry_properties.png
