NikhilVeeram/MEEN-305-FINAL/designs/active_runs/pure_weight_tight_seed2441/best_design/geometry_properties.png

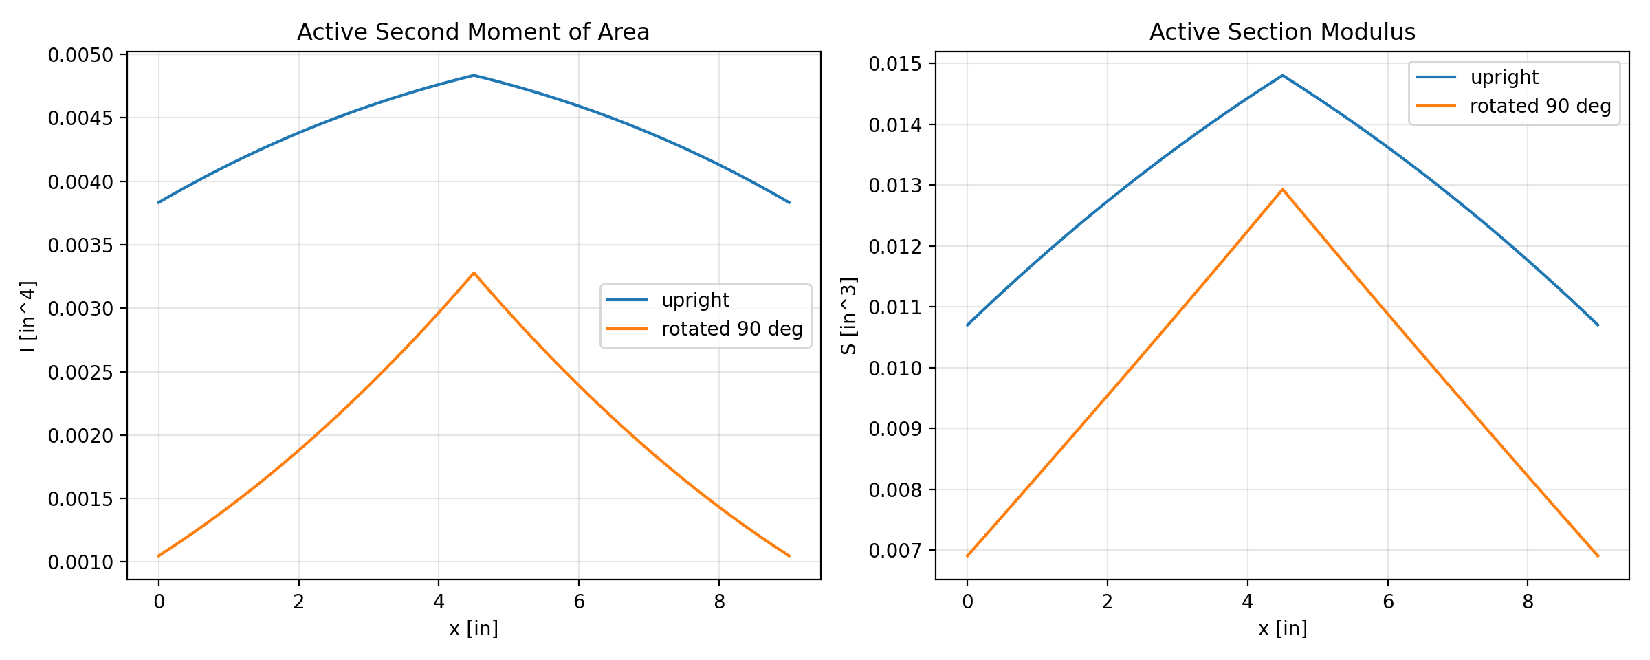
designs/active_runs/pure_weight_tight_seed2441/best_design/geometry_properties.png
