NikhilVeeram/MEEN-305-FINAL/designs/active_runs/ultra_light_full_strength_seed2433/best_design/geometry_properties.png

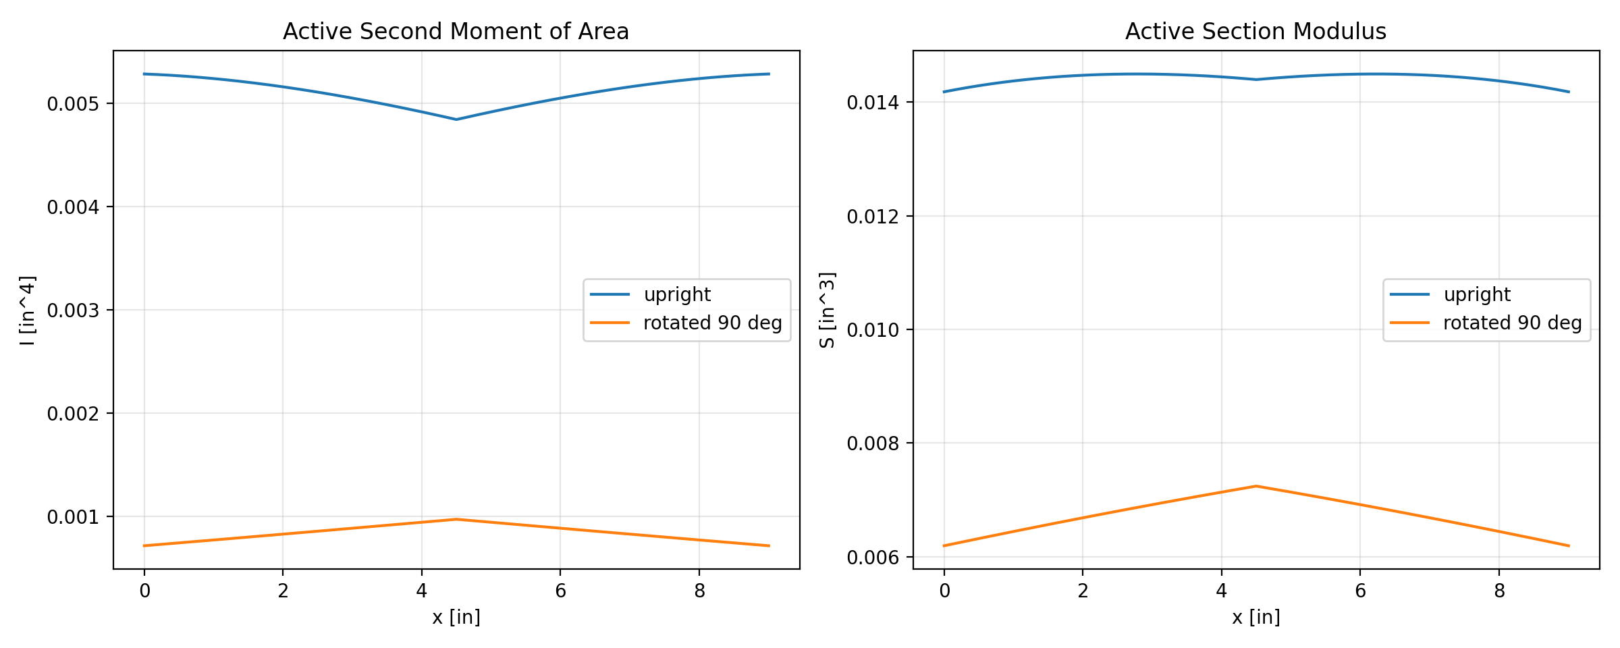
designs/active_runs/ultra_light_full_strength_seed2433/best_design/geometry_properties.png
