NikhilVeeram/MEEN-305-FINAL/designs/active_runs/ultra_light_open_symmetric_seed2424/best_design/geometry_properties.png

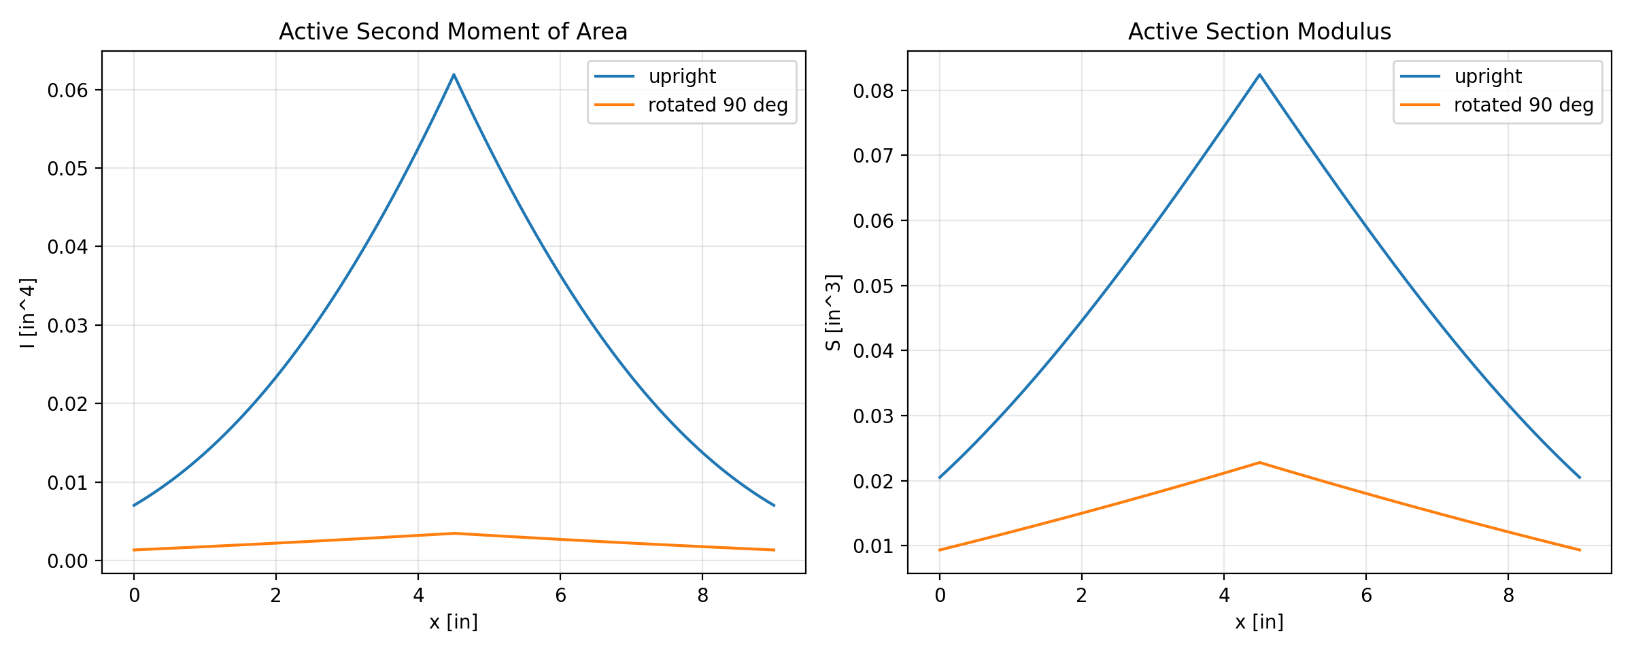
designs/active_runs/ultra_light_open_symmetric_seed2424/best_design/geometry_properties.png
