NikhilVeeram/MEEN-305-FINAL/designs/active_runs/ultra_light_run4_asymmetric_seed2427/best_design/geometry_properties.png

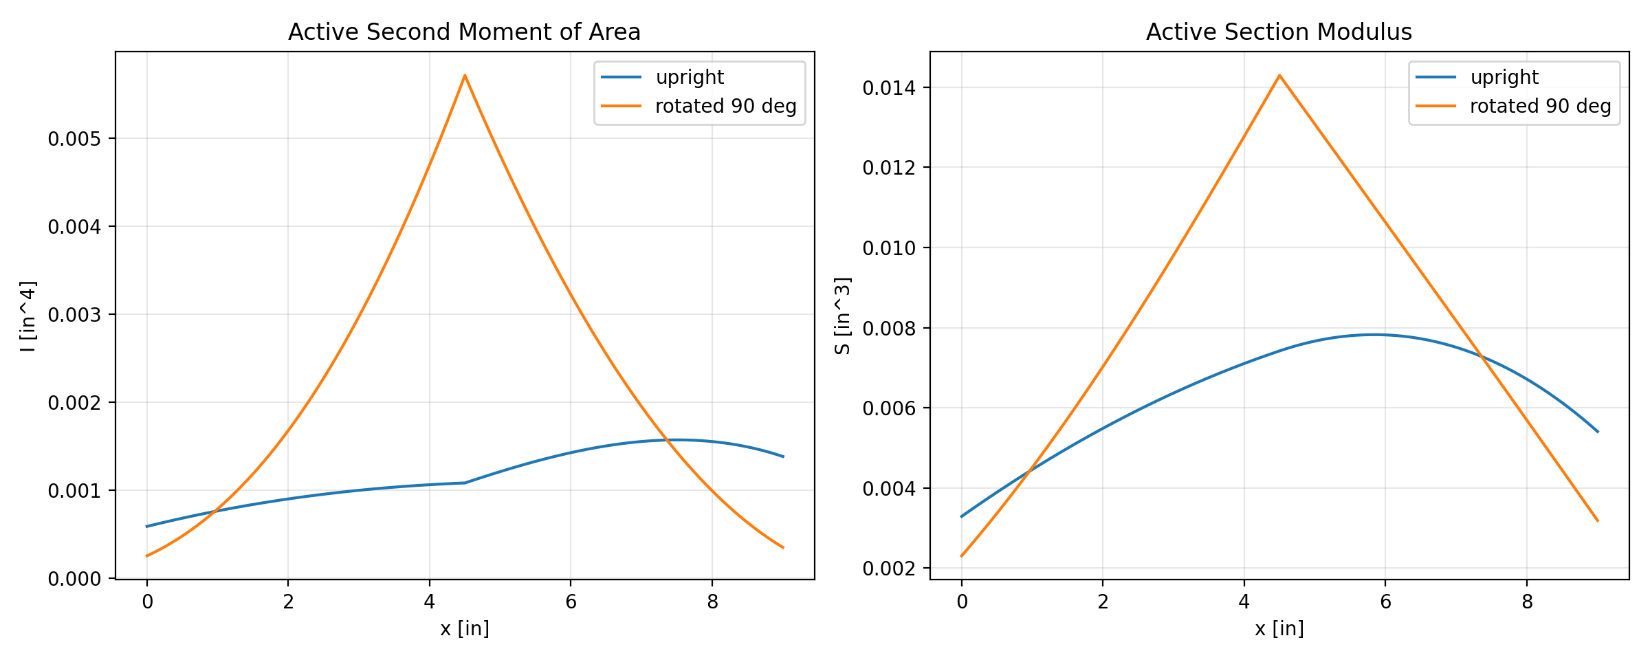
designs/active_runs/ultra_light_run4_asymmetric_seed2427/best_design/geometry_properties.png
