NikhilVeeram/MEEN-305-FINAL/designs/active_runs/ultra_light_runA_seed2430/beam_parameter_map.png

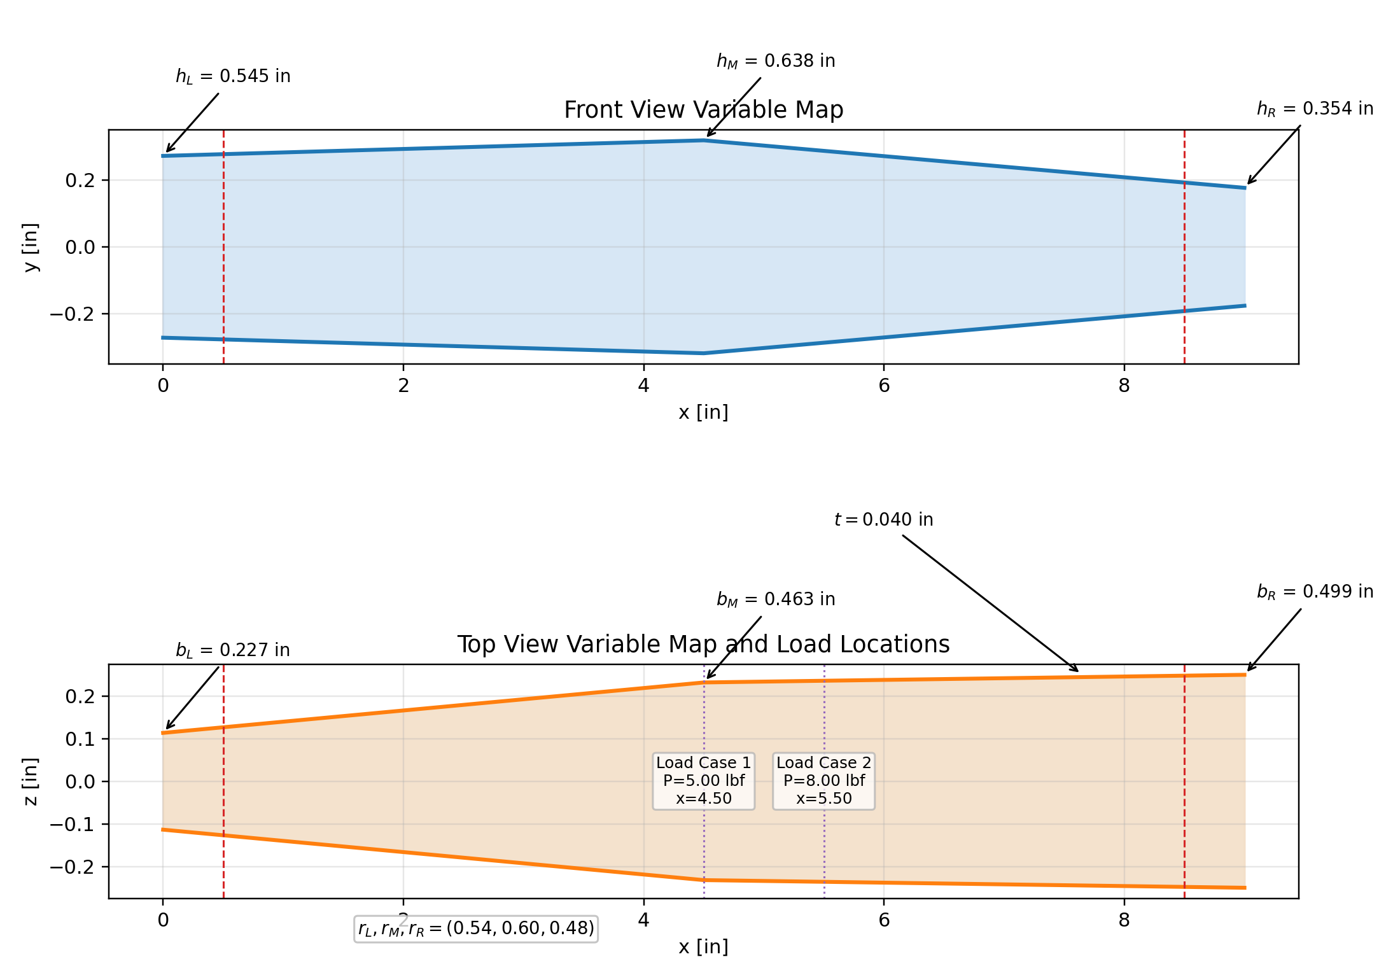
designs/active_runs/ultra_light_runA_seed2430/beam_parameter_map.png
