NikhilVeeram/MEEN-305-FINAL/designs/active_runs/ultra_light_runA_seed2430/best_design/geometry_properties.png

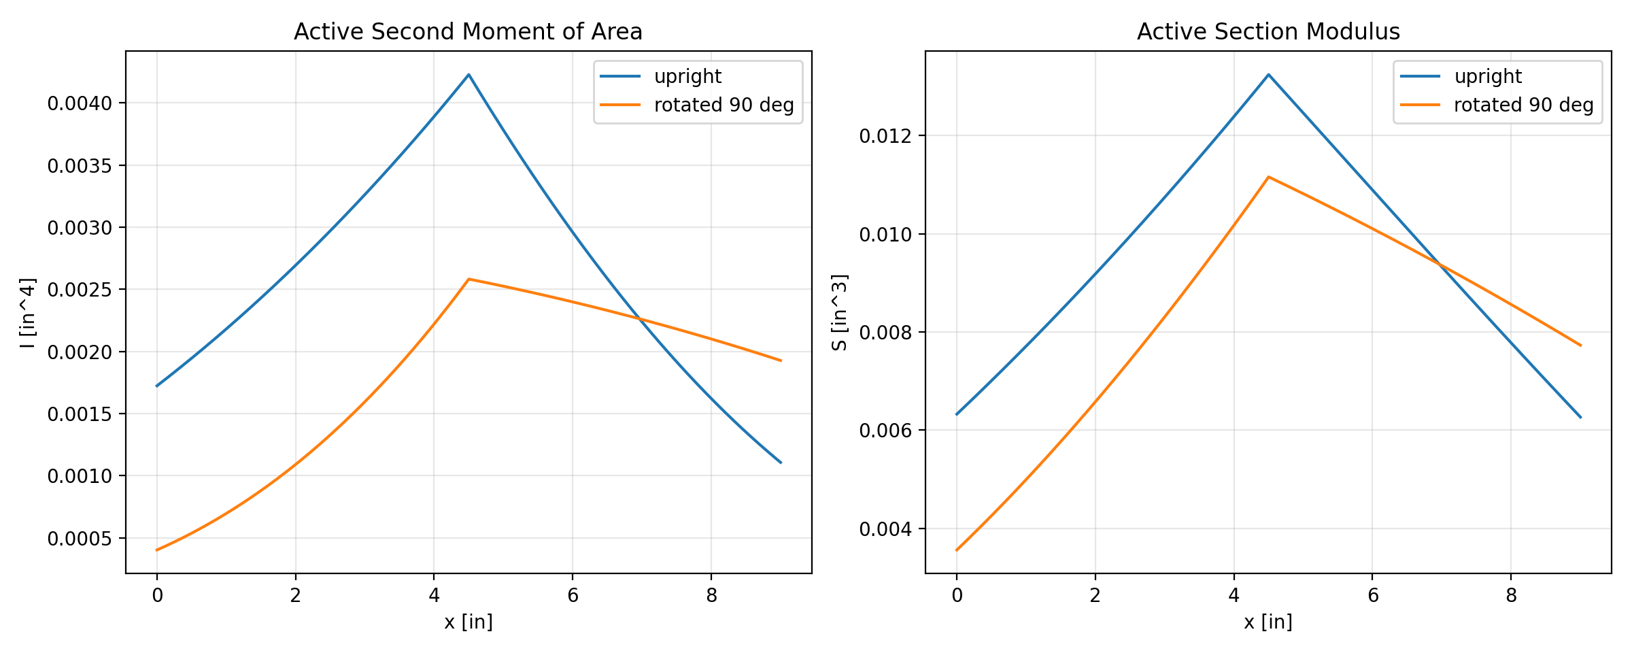
designs/active_runs/ultra_light_runA_seed2430/best_design/geometry_properties.png
