NikhilVeeram/MEEN-305-FINAL/designs/active_runs/ultra_light_runB_seed2431/best_design/geometry_properties.png

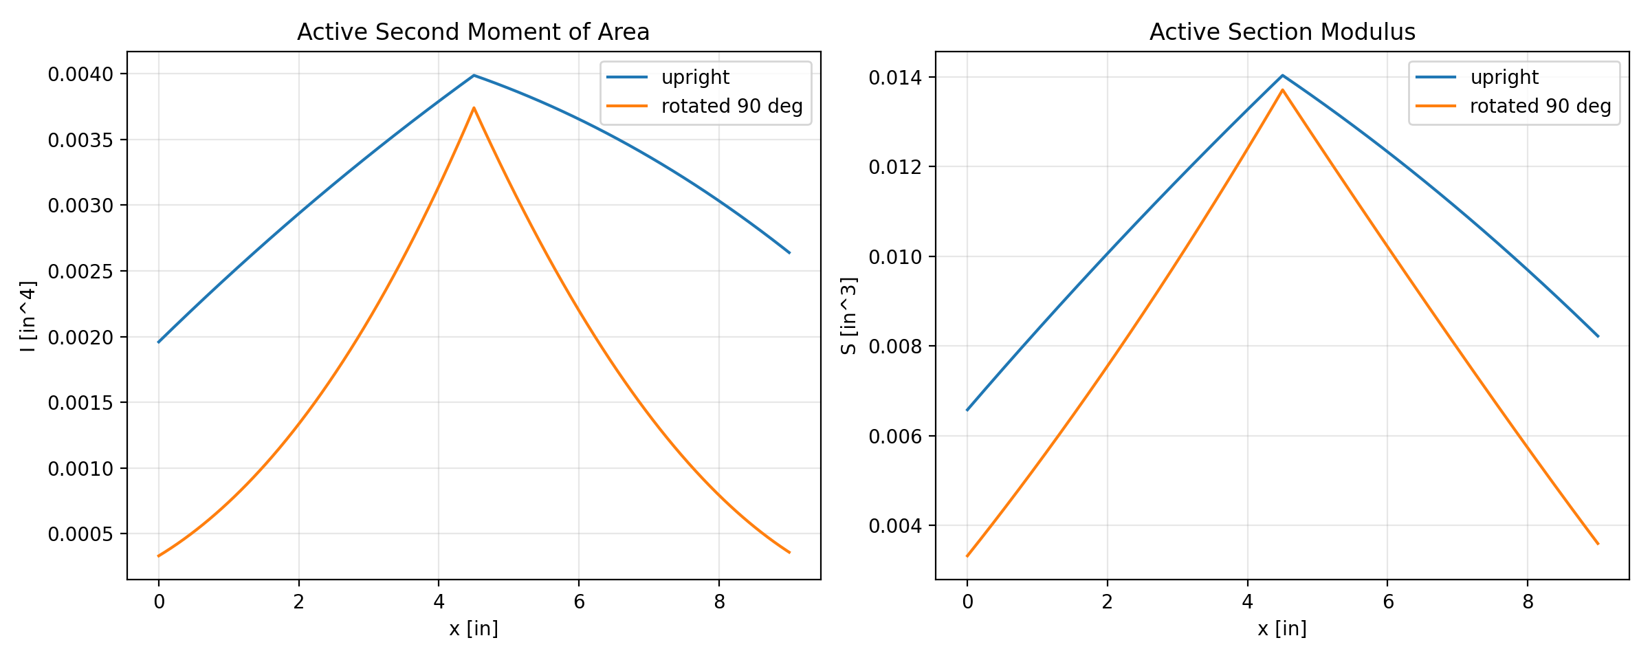
designs/active_runs/ultra_light_runB_seed2431/best_design/geometry_properties.png
