NikhilVeeram/MEEN-305-FINAL/designs/packages/continuous_design_deliverables/continuous_uniform_both_load_cases/beam_parameter_map.png

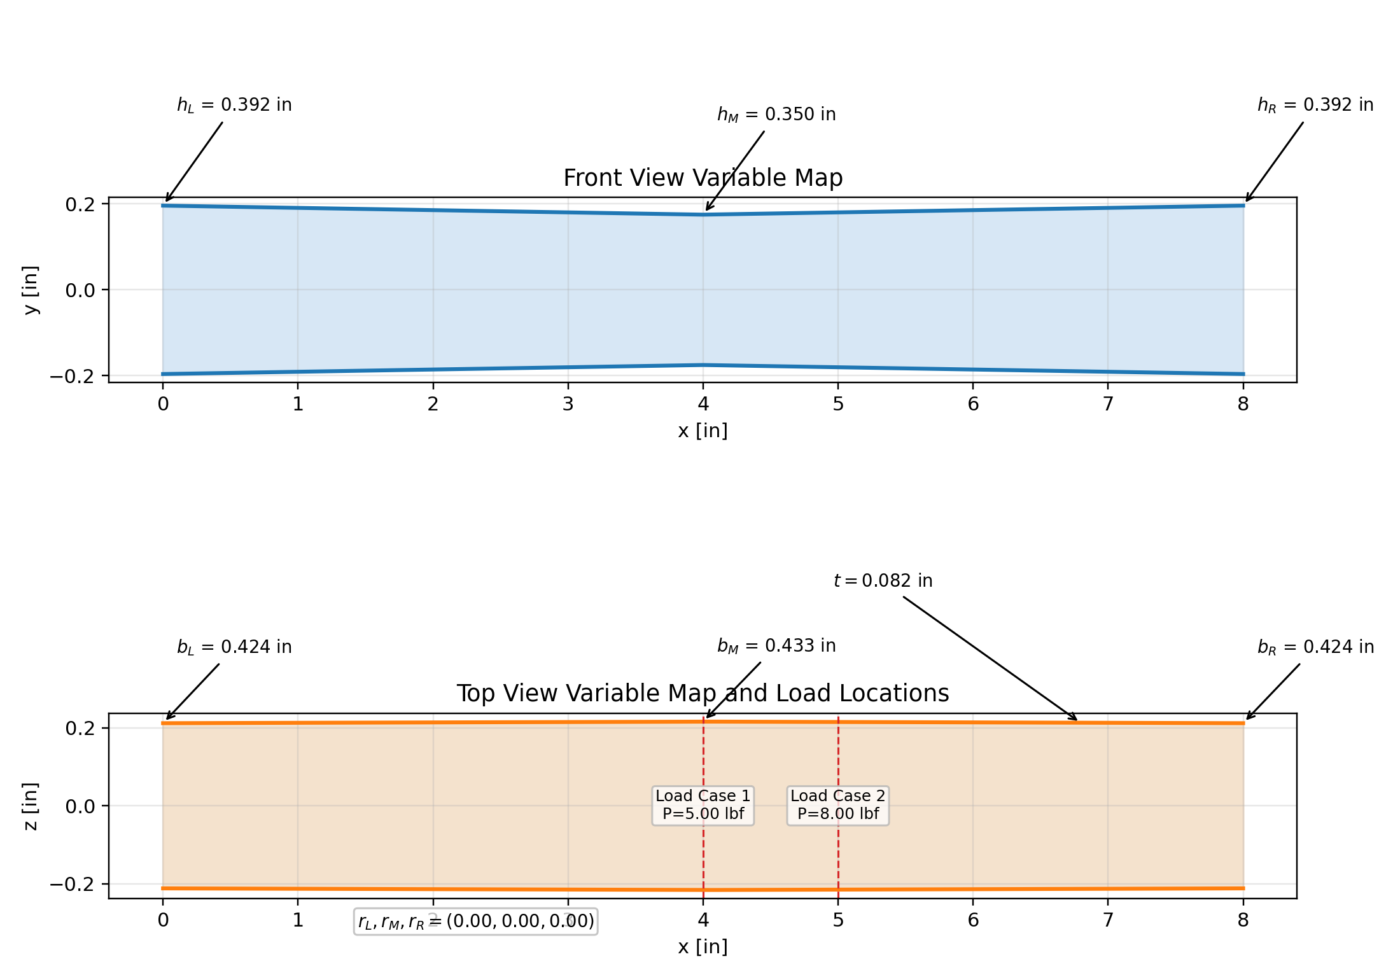
designs/packages/continuous_design_deliverables/continuous_uniform_both_load_cases/beam_parameter_map.png
