NikhilVeeram/MEEN-305-FINAL/designs/packages/continuous_design_deliverables_9in_corrected/continuous_uniform_both_load_cases_9in_corrected/beam_parameter_map.png

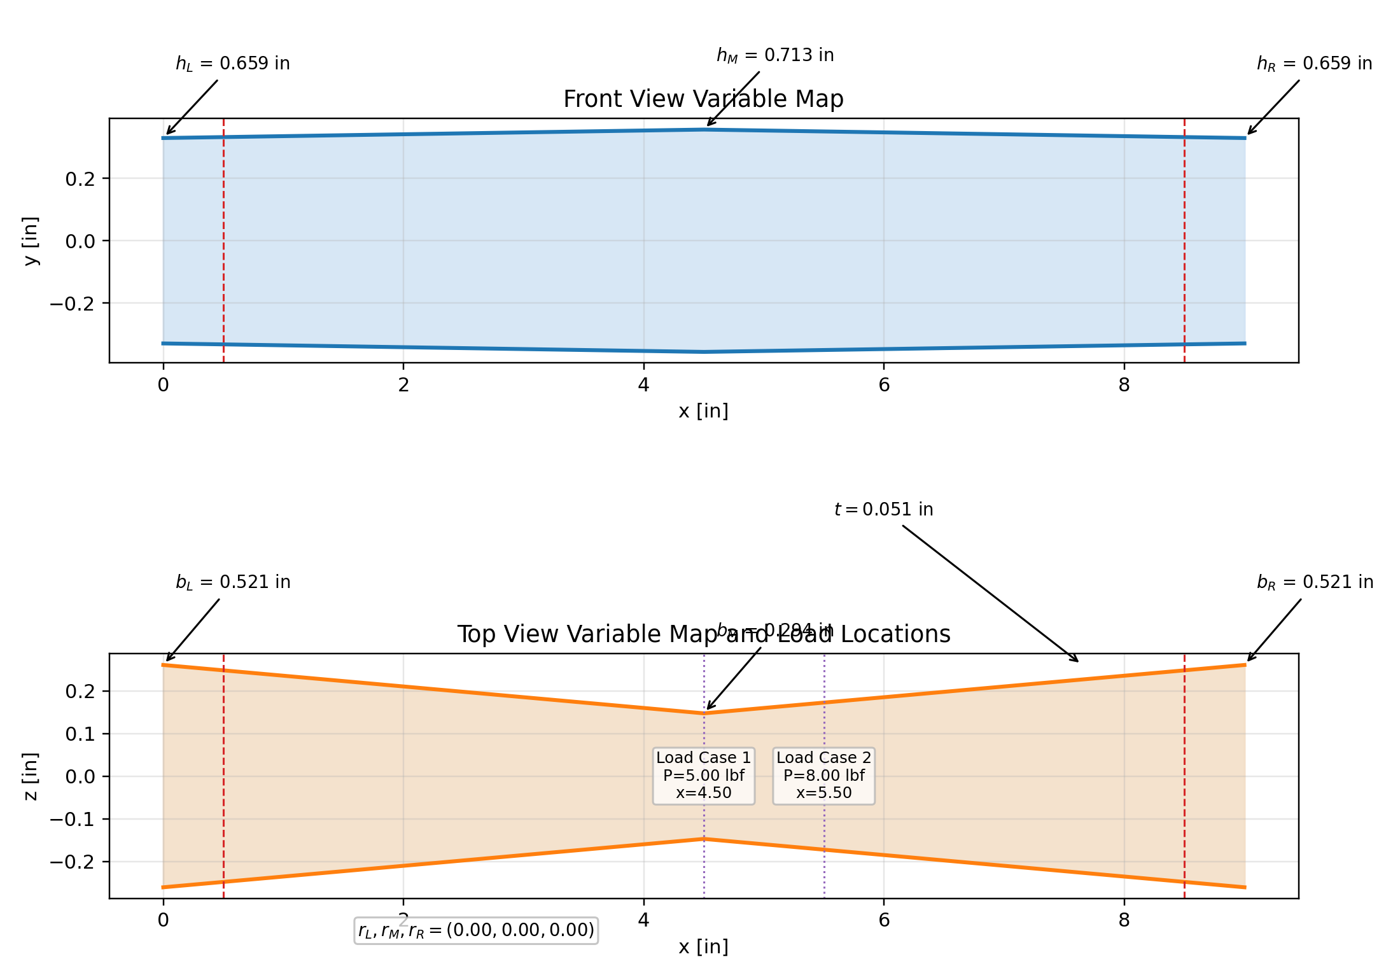
designs/packages/continuous_design_deliverables_9in_corrected/continuous_uniform_both_load_cases_9in_corrected/beam_parameter_map.png
