NikhilVeeram/MEEN-305-FINAL/docs/reports/figures/beam02/model_preview.png

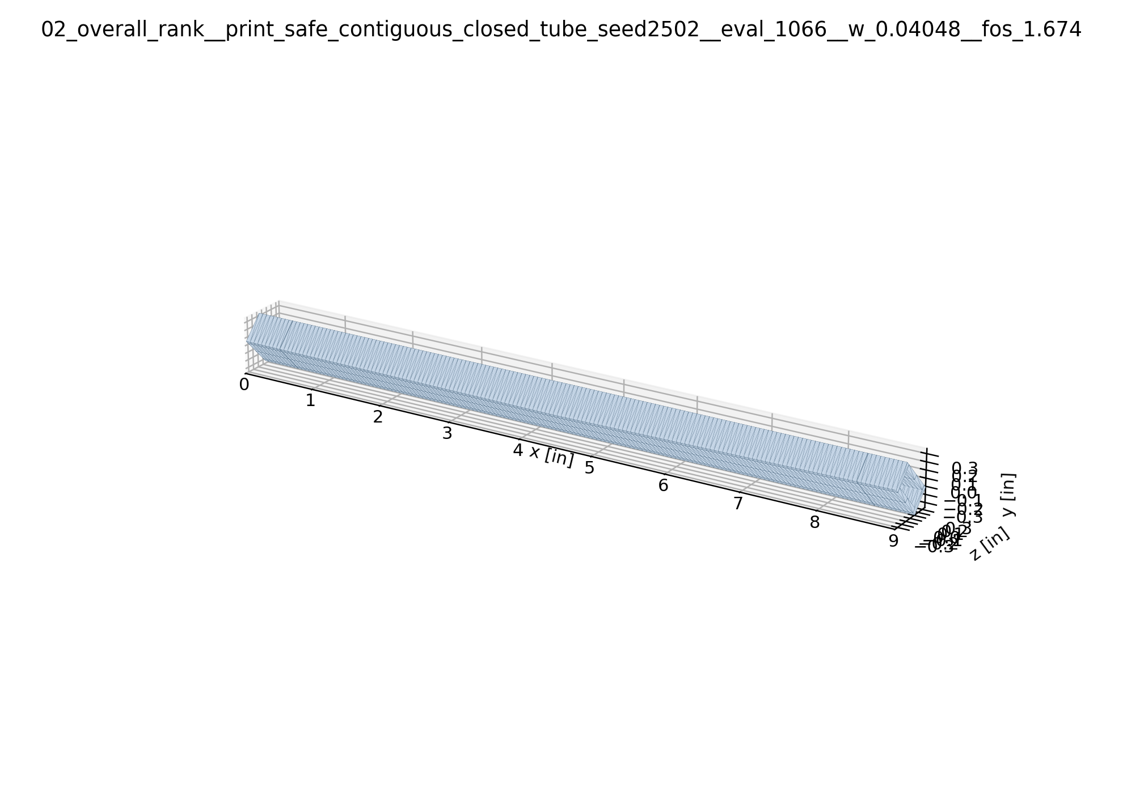
docs/reports/figures/beam02/model_preview.png
