NikhilVeeram/MEEN-305-FINAL/optimization_connected_2026/best_design/geometry_properties.png

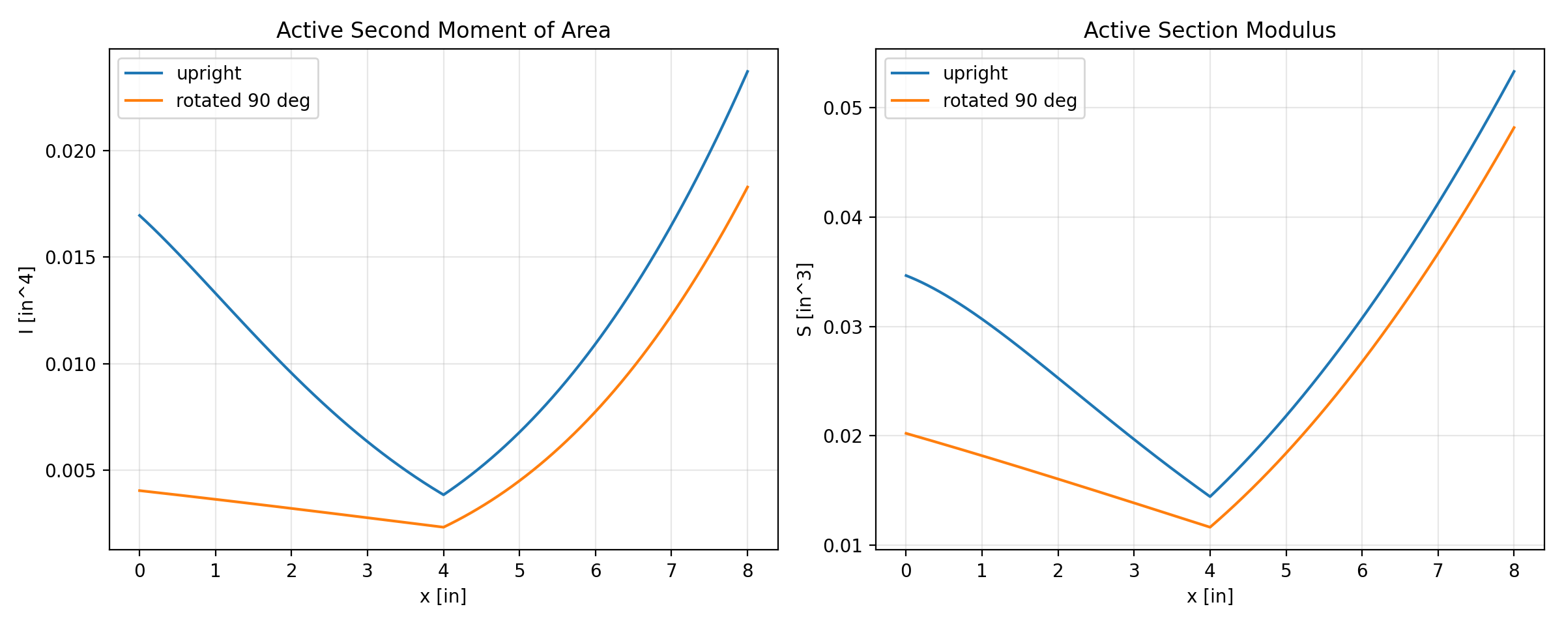
optimization_connected_2026/best_design/geometry_properties.png
