NikhilVeeram/MEEN-305-FINAL/optimization_connected_7777/best_design/geometry_properties.png

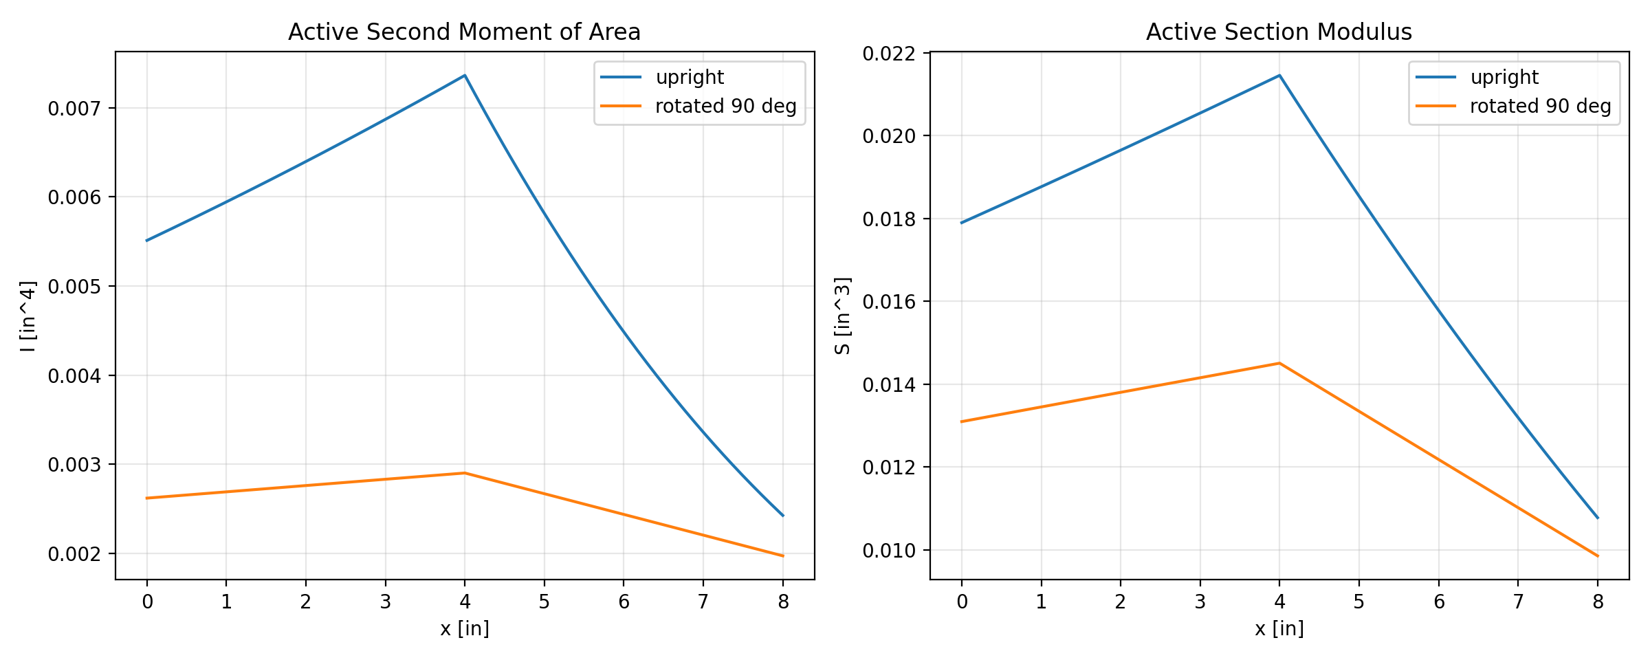
optimization_connected_7777/best_design/geometry_properties.png
