NikhilVeeram/MEEN-305-FINAL/optimization_opening_smoke/best_design/geometry_properties.png

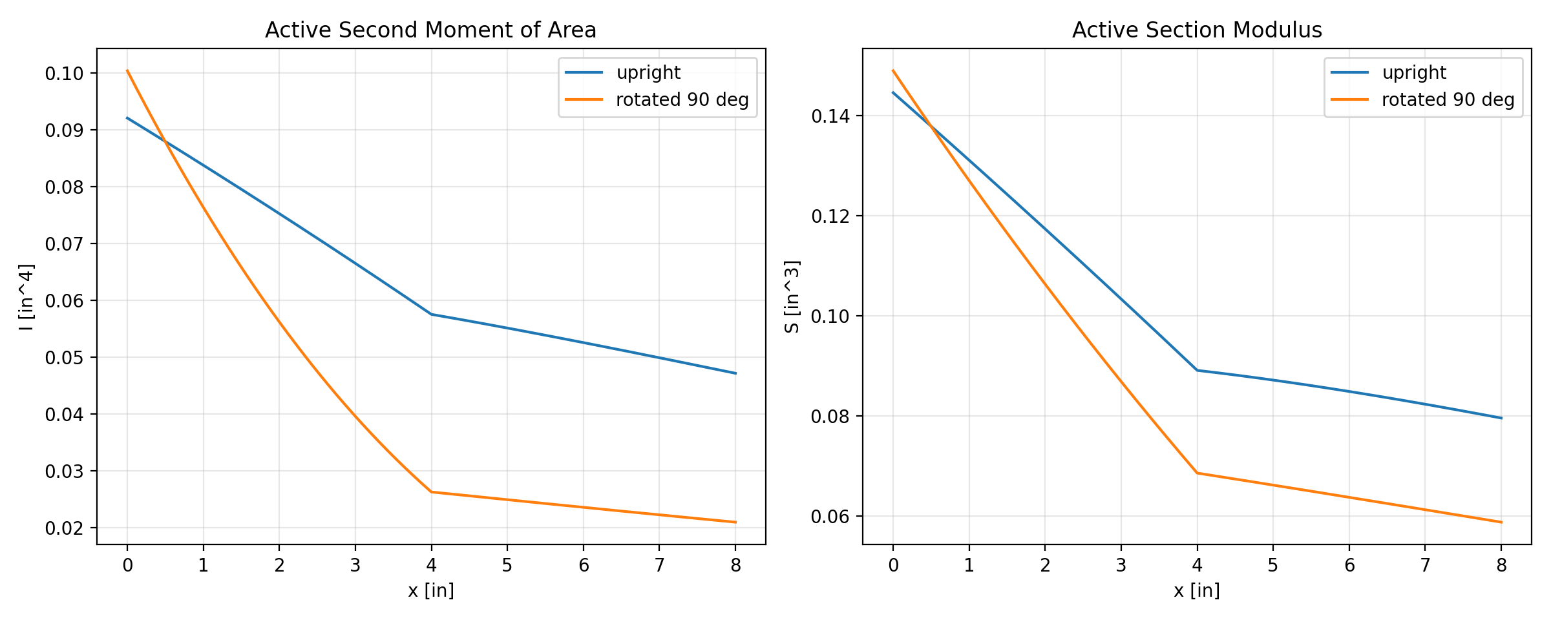
optimization_opening_smoke/best_design/geometry_properties.png
