NikhilVeeram/MEEN-305-FINAL/optimization_targeted/best_design/geometry_properties.png

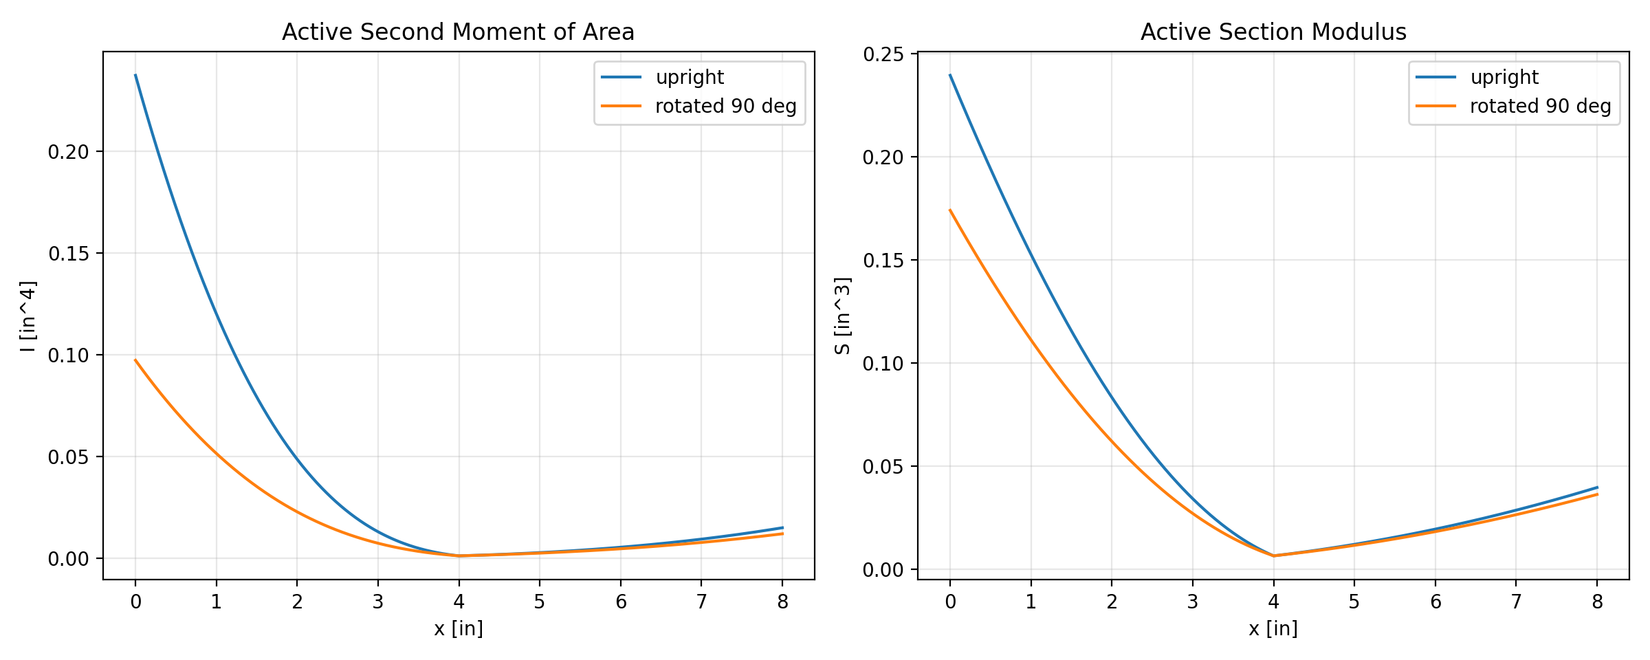
optimization_targeted/best_design/geometry_properties.png
