NikhilVeeram/MEEN-305-FINAL/optimization_v2_E/best_design/geometry_properties.png

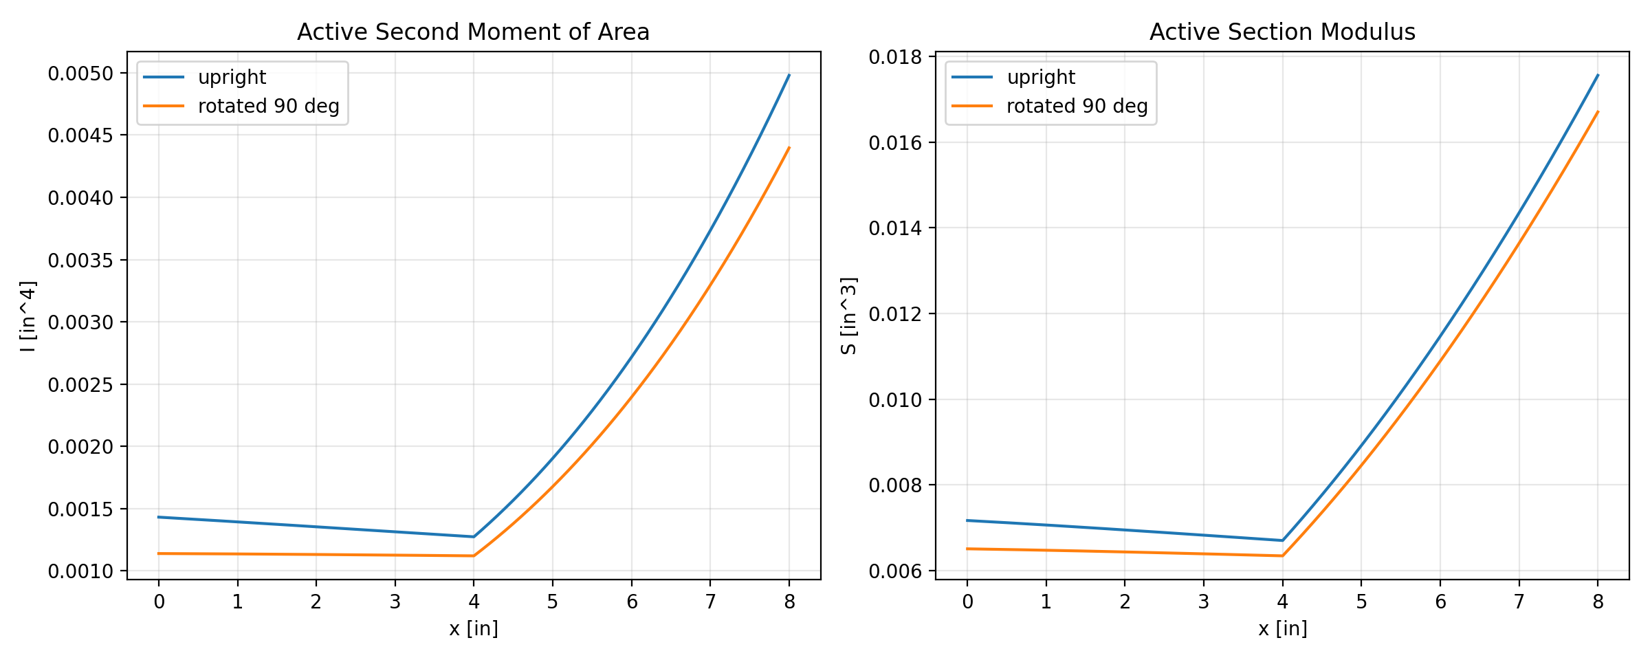
optimization_v2_E/best_design/geometry_properties.png
