NikhilVeeram/MEEN-305-FINAL/best-designs-20/3d-models/14_overall_rank__continuous_uniform_both_load_cases_9in_corrected__eval_0402__w_0.03782__fos_2.022.stl

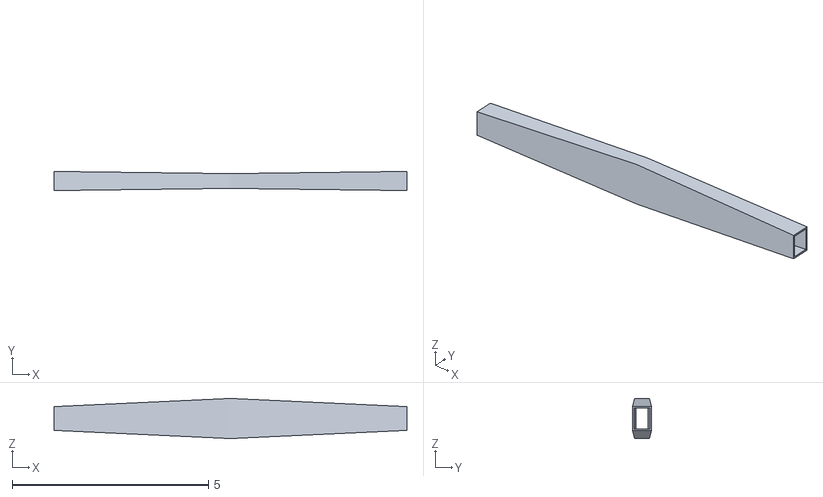
[picture p170: CAD file, 2026-04-24]
best-designs-20/design-packages/14_overall_rank__continuous_uniform_both_load_cases_9in_corrected__eval_0402__w_0.03782__fos_2.022/14_overall_rank__continuous_uniform_both_load_cases_9in_corrected__e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
9.00 x 0.488 x 1.02
