NikhilVeeram/MEEN-305-FINAL/best-designs-20/3d-models/16_overall_rank__continuous_uniform_both_load_cases_9in_corrected__eval_0219__w_0.03983__fos_1.761.stl

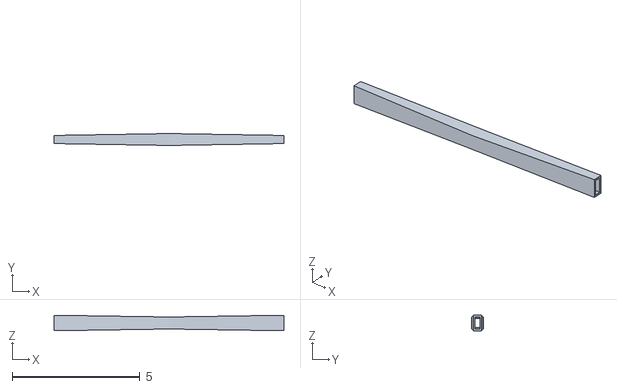
[picture p172: CAD file, 2026-04-24]
best-designs-20/design-packages/16_overall_rank__continuous_uniform_both_load_cases_9in_corrected__eval_0219__w_0.03983__fos_1.761/16_overall_rank__continuous_uniform_both_load_cases_9in_corrected__e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
9.00 x 0.465 x 0.607
