NikhilVeeram/MEEN-305-FINAL/best-designs-20/3d-models/17_overall_rank__print_safe_contiguous_closed_tube_seed2502__eval_1066__w_0.04048__fos_1.674.stl

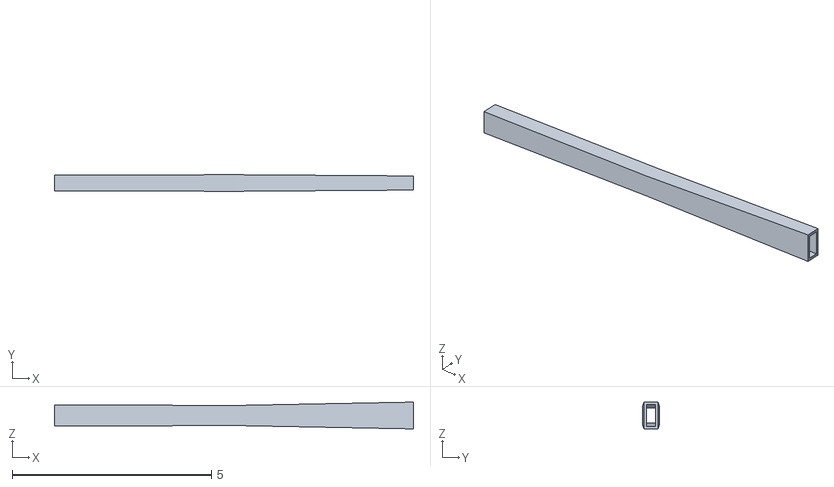
[picture p173: CAD file, 2026-04-24]
best-designs-20/design-packages/17_overall_rank__print_safe_contiguous_closed_tube_seed2502__eval_1066__w_0.04048__fos_1.674/17_overall_rank__print_safe_contiguous_closed_tube_seed2502__eval_1066__w_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
9.00 x 0.417 x 0.672
