NikhilVeeram/MEEN-305-FINAL/best-designs-20/3d-models/18_overall_rank__continuous_uniform_both_load_cases_9in_corrected__eval_0441__w_0.04079__fos_1.503.stl

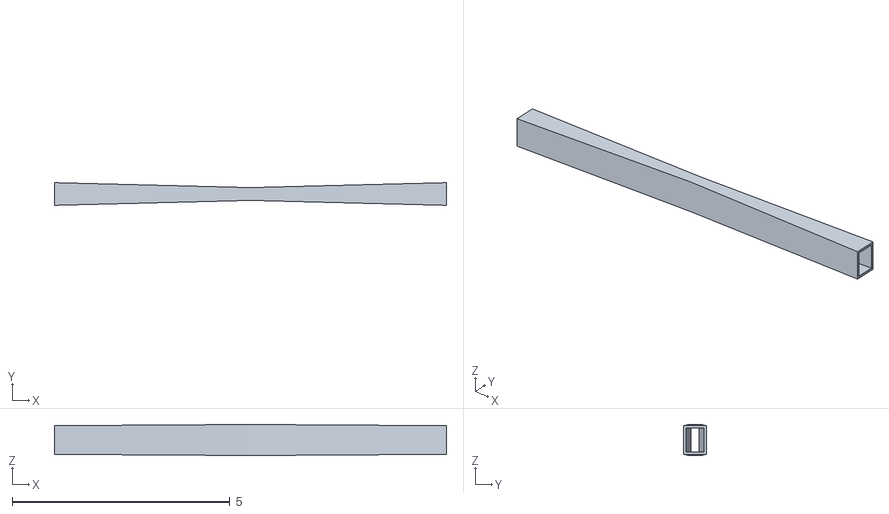
[picture p174: CAD file, 2026-04-24]
best-designs-20/design-packages/18_overall_rank__continuous_uniform_both_load_cases_9in_corrected__eval_0441__w_0.04079__fos_1.503/18_overall_rank__continuous_uniform_both_load_cases_9in_corrected__e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
9.00 x 0.521 x 0.712
