NikhilVeeram/MEEN-305-FINAL/best-designs-20/3d-models/19_overall_rank__ultra_light_full_infill_seed2432__eval_2513__w_0.04121__fos_1.565.stl

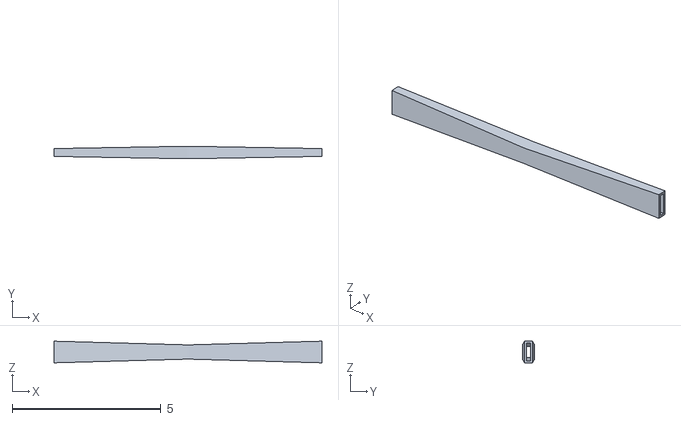
[picture p175: CAD file, 2026-04-24]
best-designs-20/design-packages/19_overall_rank__ultra_light_full_infill_seed2432__eval_2513__w_0.04121__fos_1.565/19_overall_rank__ultra_light_full_infill_seed2432__eval_2513__w_0.04121__fos_1.565.s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
9.00 x 0.419 x 0.728
