NikhilVeeram/MEEN-305-FINAL/best-designs-20/3d-models/20_overall_rank__ultra_light_run3_lowheight_seed2426__eval_1611__w_0.04175__fos_2.633.stl

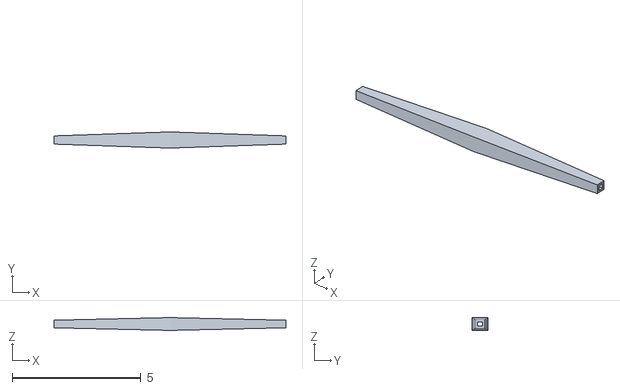
[picture p176: CAD file, 2026-04-24]
best-designs-20/design-packages/20_overall_rank__ultra_light_run3_lowheight_seed2426__eval_1611__w_0.04175__fos_2.633/20_overall_rank__ultra_light_run3_lowheight_seed2426__eval_1611__w_0.04175__fos_2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
9.00 x 0.624 x 0.496
