NikhilVeeram/MEEN-305-FINAL/best-designs-20/3d-models-print-oriented/Completed_Pins_Sliced_Items.3mf

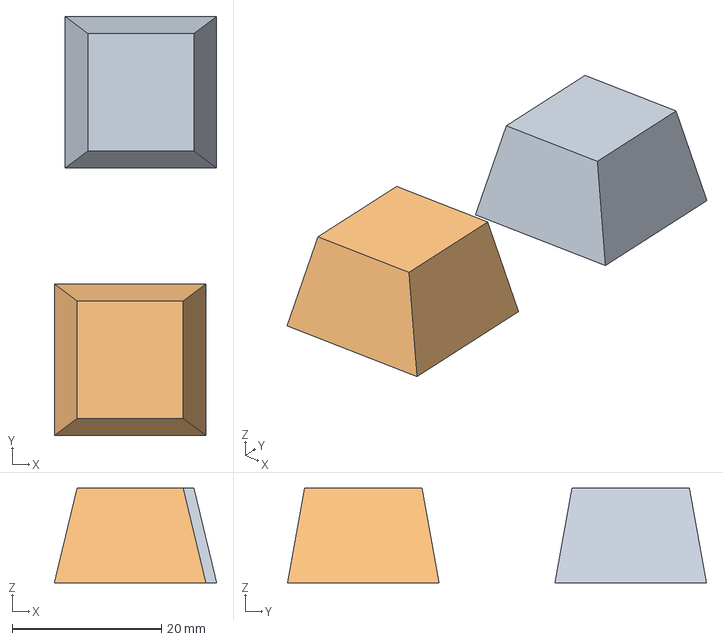
[picture p177: CAD file, 2026-04-24]
best-designs-20/3d-models-print-oriented/Completed_Pins_Sliced_Items.3mf
21.8 x 56.2 x 12.7 mm
support_block_single_tapered_flat_top.obj x 2
