NikhilVeeram/MEEN-305-FINAL/designs/model_exports/continuous_mesh_exports/continuous_uniform_load_case_1.stl

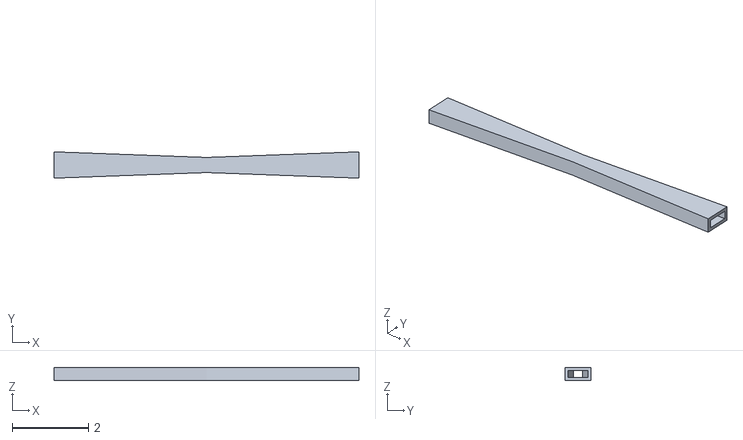
[picture p178: CAD file, 2026-04-22]
designs/model_exports/continuous_mesh_exports/continuous_uniform_load_case_1.stl
8.00 x 0.69 x 0.35
