NikhilVeeram/MEEN-305-FINAL/designs/model_exports/continuous_mesh_exports_9in_practical_buffer/continuous_uniform_both_load_cases_9in_practical_buffer.stl

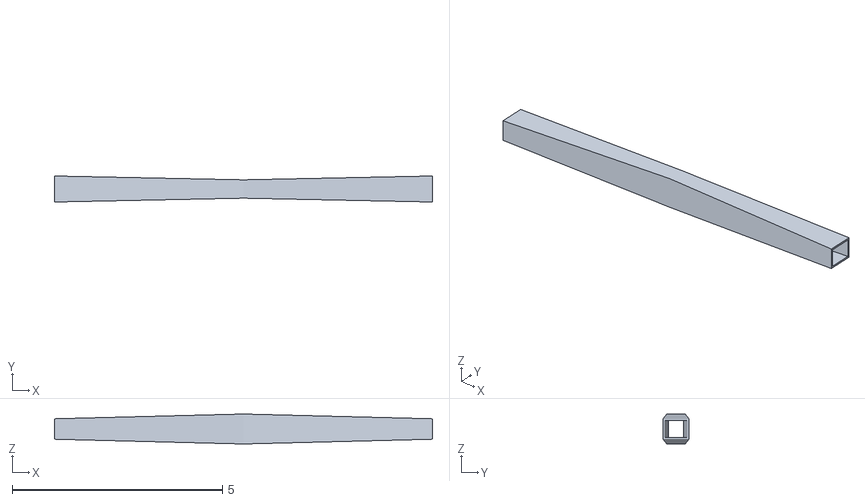
[picture p179: CAD file, 2026-04-26]
designs/model_exports/continuous_mesh_exports_9in_practical_buffer/continuous_uniform_both_load_cases_9in_practical_buffer.stl
9.00 x 0.62 x 0.713
