NikhilVeeram/MEEN-305-FINAL/designs/packages/continuous_design_deliverables/continuous_uniform_both_load_cases/continuous_uniform_both_load_cases.stl

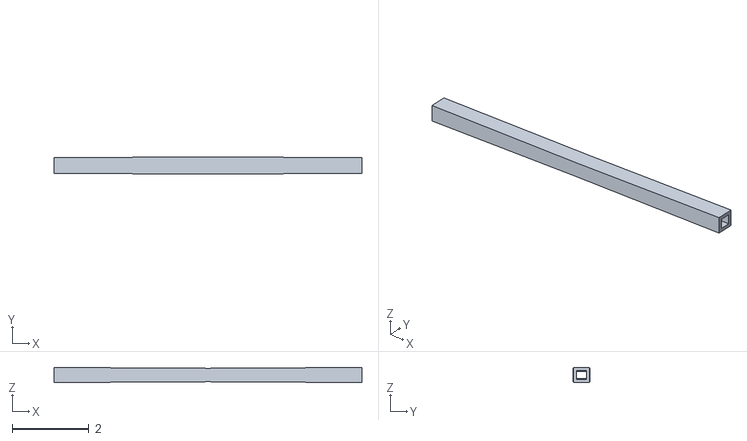
[picture p180: CAD file, 2026-04-22]
designs/packages/continuous_design_deliverables/continuous_uniform_both_load_cases/continuous_uniform_both_load_cases.stl
8.00 x 0.433 x 0.392
