NikhilVeeram/MEEN-305-FINAL/designs/packages/continuous_design_deliverables/continuous_uniform_load_case_2/continuous_uniform_load_case_2.stl

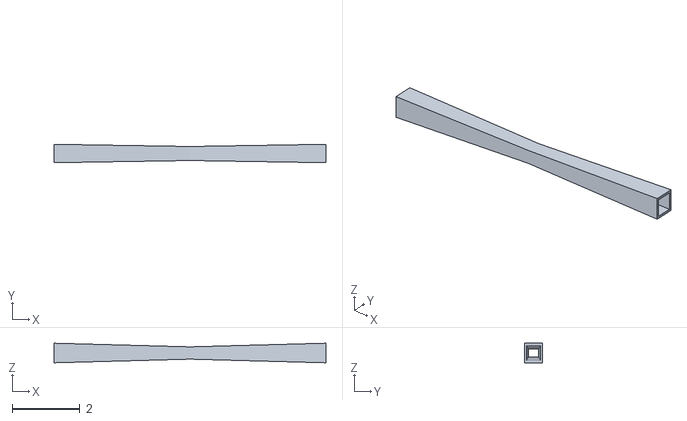
[picture p181: CAD file, 2026-04-22]
designs/packages/continuous_design_deliverables/continuous_uniform_load_case_2/continuous_uniform_load_case_2.stl
8.00 x 0.541 x 0.577
