NikhilVeeram/MEEN-305-FINAL/final-champion/champion_beam.stl

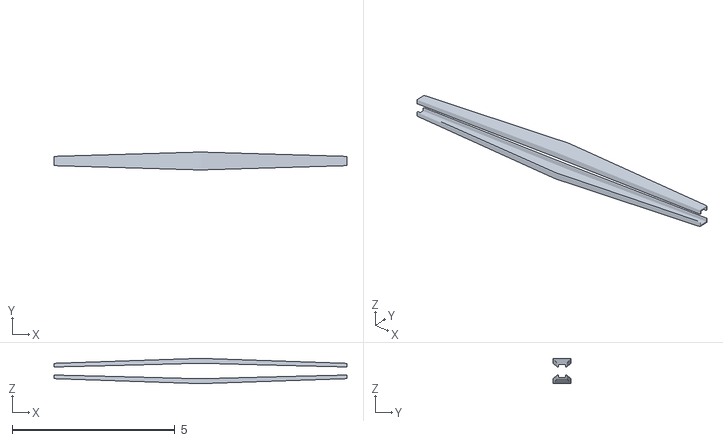
[picture p182: CAD file, 2026-04-24]
final-champion/champion_beam.stl
9.00 x 0.549 x 0.775
