NikhilVeeram/MEEN-305-FINAL/models_3d/optimization_connected_v2_3030.stl

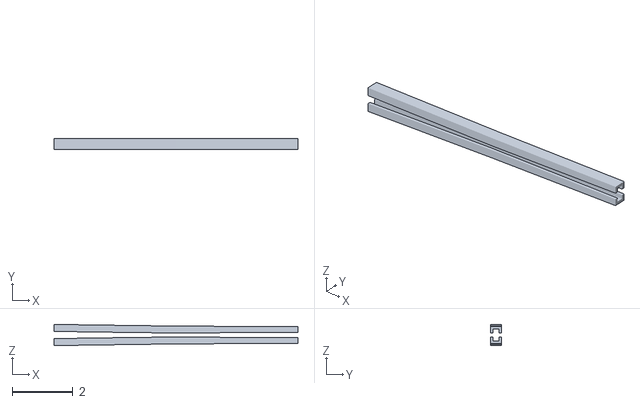
[picture p183: CAD file, 2026-04-21]
models_3d/optimization_connected_v2_3030.stl
8.00 x 0.351 x 0.694
