NikhilVeeram/MEEN-305-FINAL/models_3d/optimization_v2_p.stl

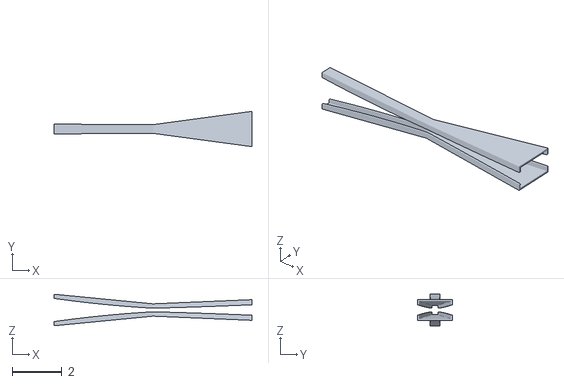
[picture p184: CAD file, 2026-04-21]
models_3d/optimization_v2_p.stl
8.00 x 1.43 x 1.27
