NikhilVeeram/MEEN-305-FINAL/models_3d/optimization_final.stl

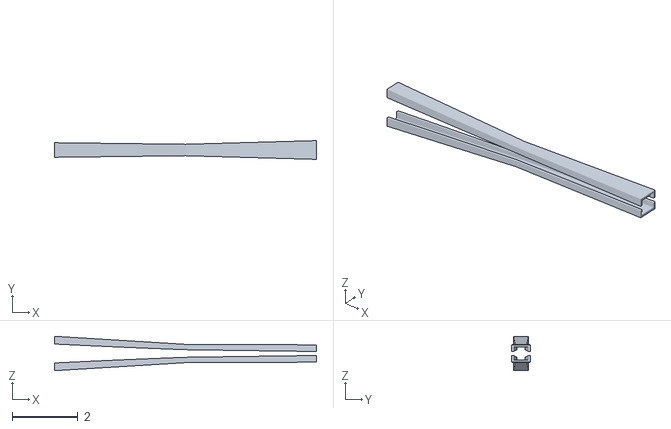
[picture p185: CAD file, 2026-04-21]
models_3d/optimization_final.stl
8.00 x 0.572 x 1.05
