NikhilVeeram/MEEN-305-FINAL/models_3d/optimization_connected_v2_9191.stl

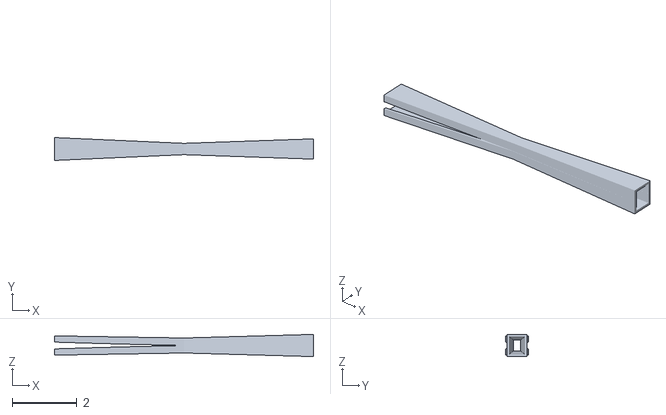
[picture p186: CAD file, 2026-04-21]
models_3d/optimization_connected_v2_9191.stl
8.00 x 0.707 x 0.685
