NikhilVeeram/MEEN-305-FINAL/models_3d/optimization_v2_j.stl

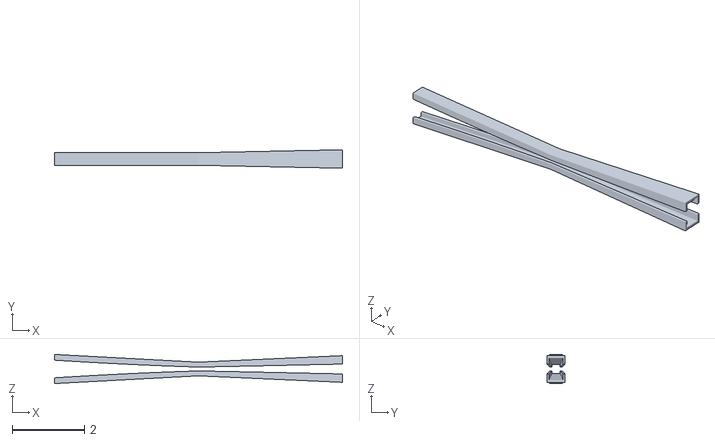
[picture p187: CAD file, 2026-04-21]
models_3d/optimization_v2_j.stl
8.00 x 0.512 x 0.809
