NikhilVeeram/MEEN-305-FINAL/models_3d/optimization_connected_v3.stl

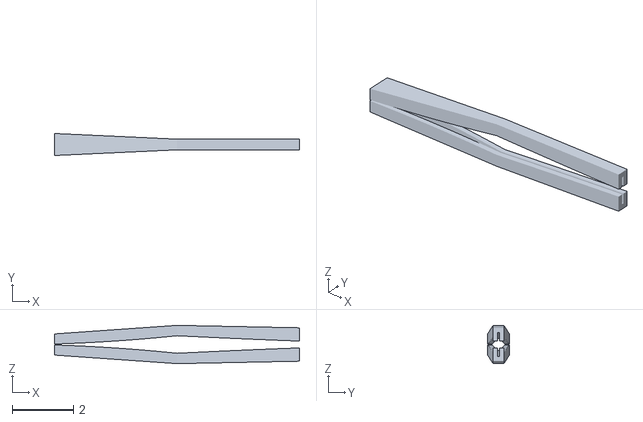
[picture p188: CAD file, 2026-04-21]
models_3d/optimization_connected_v3.stl
8.00 x 0.719 x 1.25
