NikhilVeeram/MEEN-305-FINAL/models_3d/optimization_connected_7777.stl

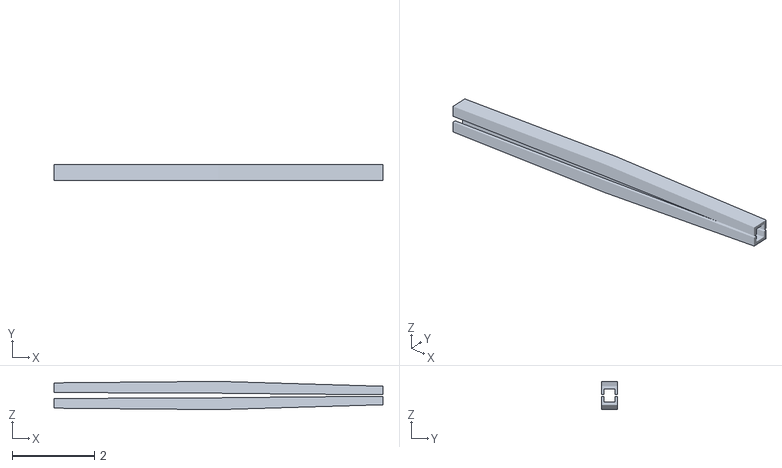
[picture p189: CAD file, 2026-04-21]
models_3d/optimization_connected_7777.stl
8.00 x 0.4 x 0.687
