NikhilVeeram/MEEN-305-FINAL/models_3d/optimization_opening_smoke.stl

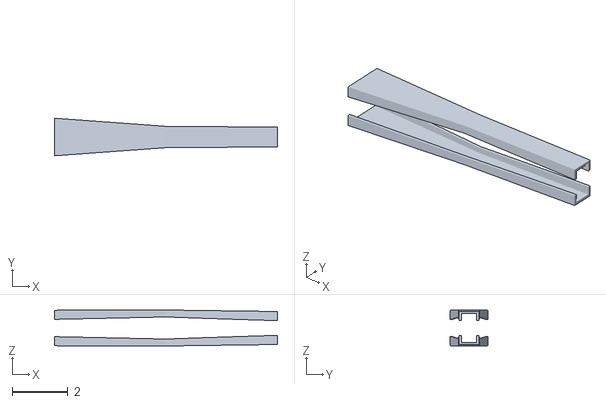
[picture p190: CAD file, 2026-04-21]
models_3d/optimization_opening_smoke.stl
8.00 x 1.35 x 1.29
