NikhilVeeram/MEEN-305-FINAL/models_3d/optimization_v2_k.stl

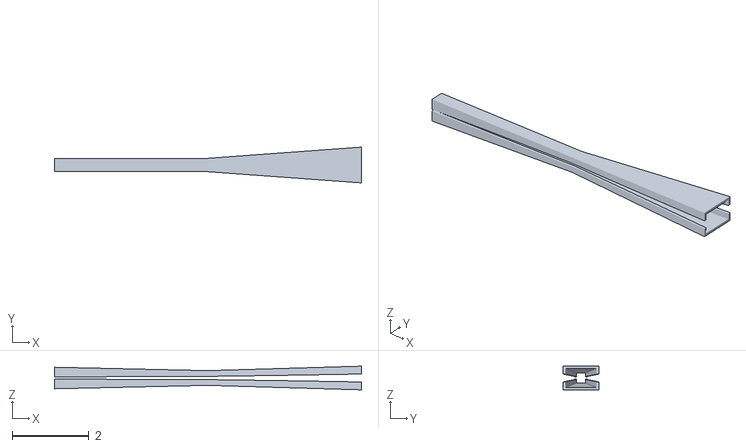
[picture p191: CAD file, 2026-04-21]
models_3d/optimization_v2_k.stl
8.00 x 0.932 x 0.617
