NikhilVeeram/MEEN-305-FINAL/models_3d/optimization_v2_h.stl

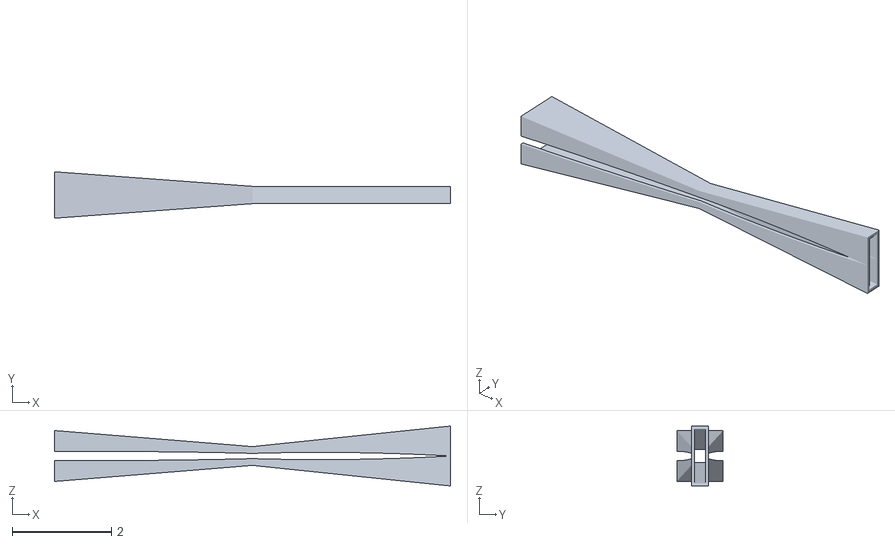
[picture p192: CAD file, 2026-04-21]
models_3d/optimization_v2_h.stl
8.00 x 0.938 x 1.21
