NikhilVeeram/MEEN-305-FINAL/models_3d/optimization_smoke_test.stl

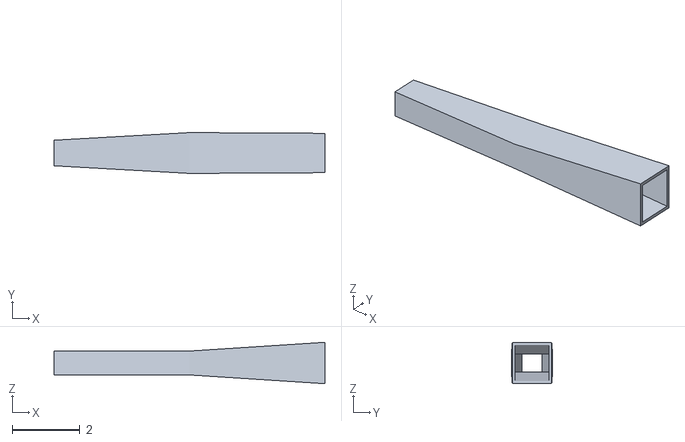
[picture p193: CAD file, 2026-04-21]
models_3d/optimization_smoke_test.stl
8.00 x 1.21 x 1.22
