NikhilVeeram/MEEN-305-FINAL/models_3d/optimization_connected_4242.stl

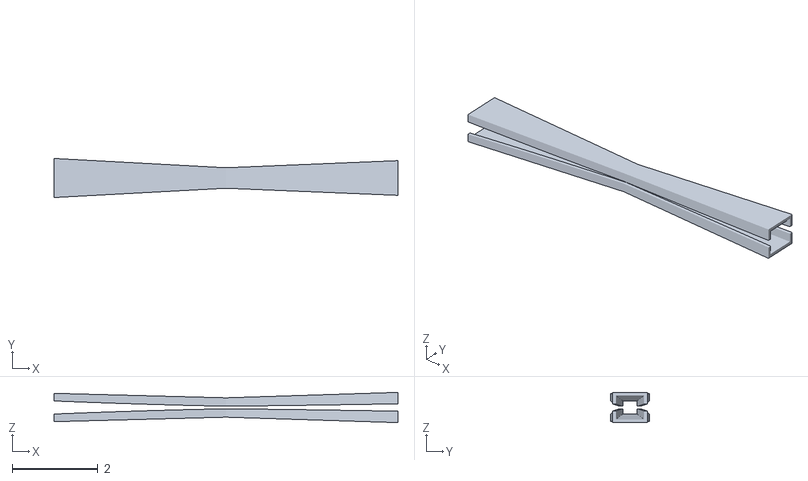
[picture p194: CAD file, 2026-04-21]
models_3d/optimization_connected_4242.stl
8.00 x 0.909 x 0.703
