NikhilVeeram/MEEN-305-FINAL/models_3d/optimization_targeted.stl

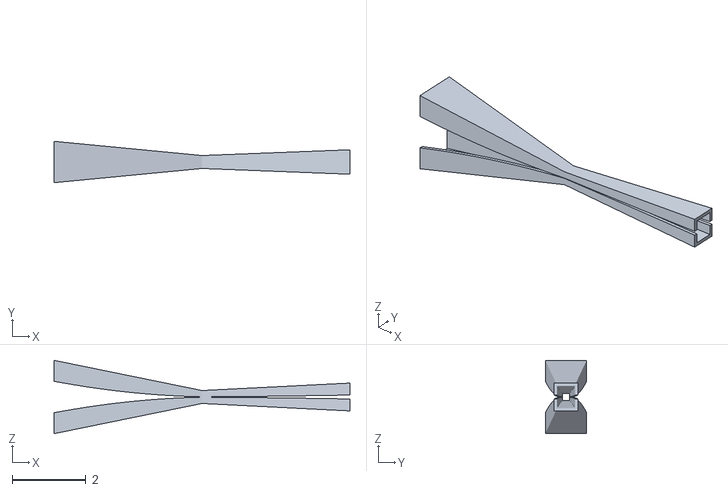
[picture p196: CAD file, 2026-04-21]
models_3d/optimization_targeted.stl
8.00 x 1.12 x 1.98
