NikhilVeeram/MEEN-305-FINAL/models_3d/optimization_v2_n.stl

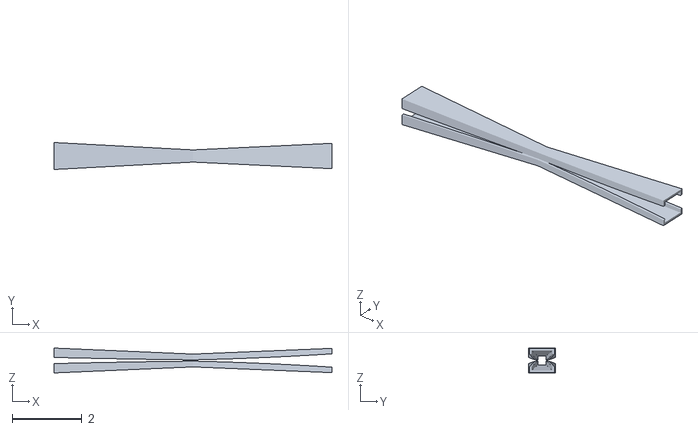
[picture p198: CAD file, 2026-04-21]
models_3d/optimization_v2_n.stl
8.00 x 0.777 x 0.716
