NikhilVeeram/MEEN-305-FINAL/models_3d/optimization_outputs.stl

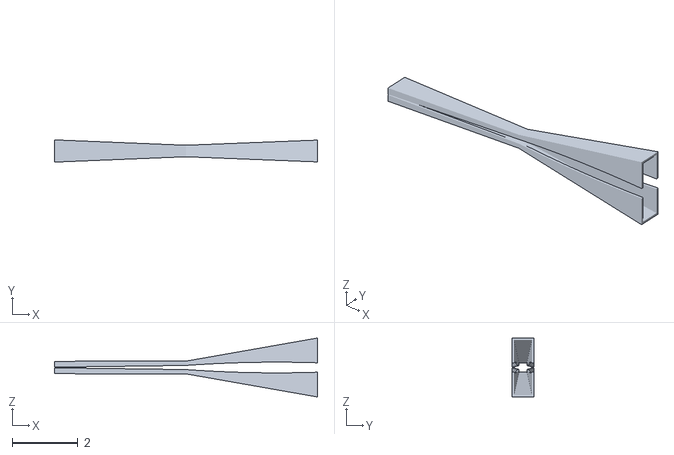
[picture p199: CAD file, 2026-04-21]
models_3d/optimization_outputs.stl
8.00 x 0.676 x 1.79
