NikhilVeeram/MEEN-305-FINAL/models_3d/optimization_v2_q42.stl

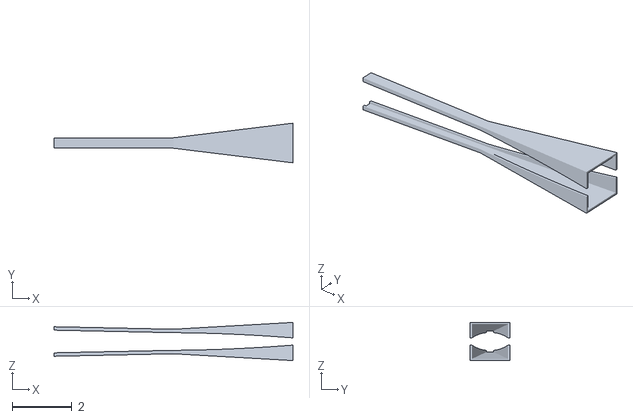
[picture p200: CAD file, 2026-04-21]
models_3d/optimization_v2_q42.stl
8.00 x 1.33 x 1.28
