NikhilVeeram/MEEN-305-FINAL/models_3d/optimization_v2_c.stl

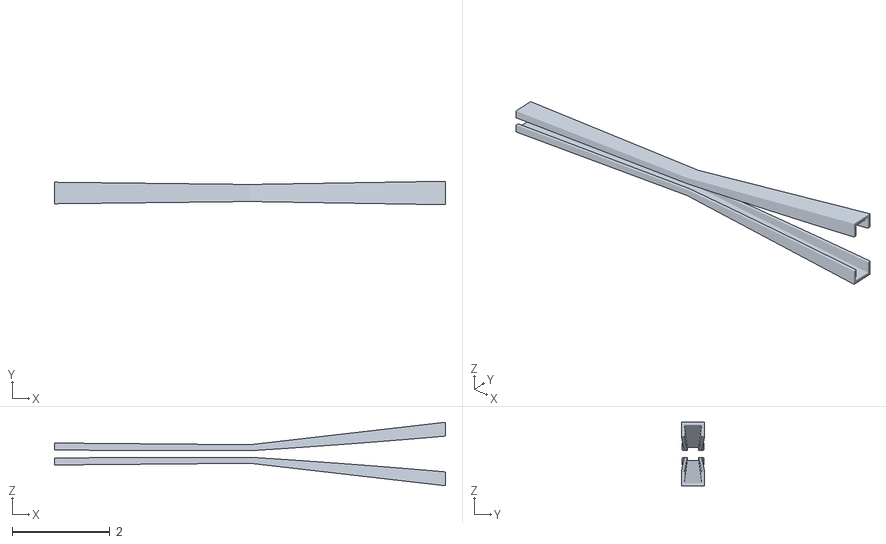
[picture p201: CAD file, 2026-04-21]
models_3d/optimization_v2_c.stl
8.00 x 0.48 x 1.30
