NikhilVeeram/MEEN-305-FINAL/models_3d/optimization_v2_d.stl

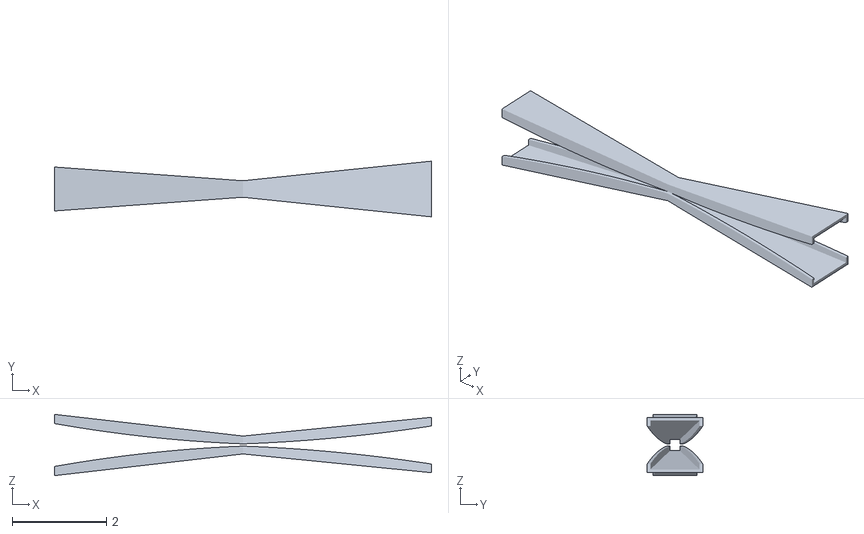
[picture p202: CAD file, 2026-04-21]
models_3d/optimization_v2_d.stl
8.00 x 1.18 x 1.30
