NikhilVeeram/MEEN-305-FINAL/models_3d/optimization_v2_l.stl

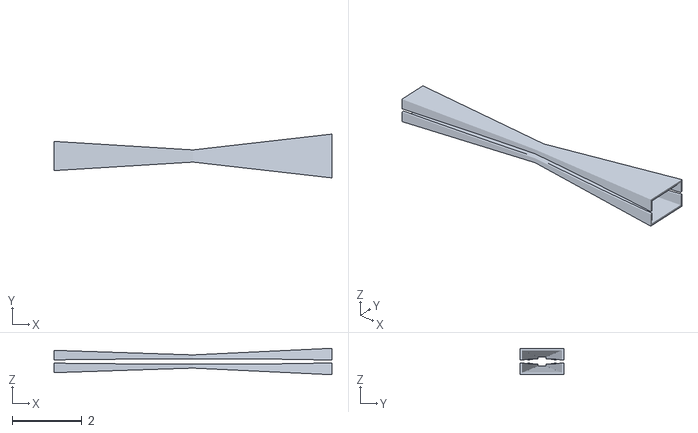
[picture p203: CAD file, 2026-04-21]
models_3d/optimization_v2_l.stl
8.00 x 1.26 x 0.762
