NikhilVeeram/MEEN-305-FINAL/models_3d/optimization_v2_q7777.stl

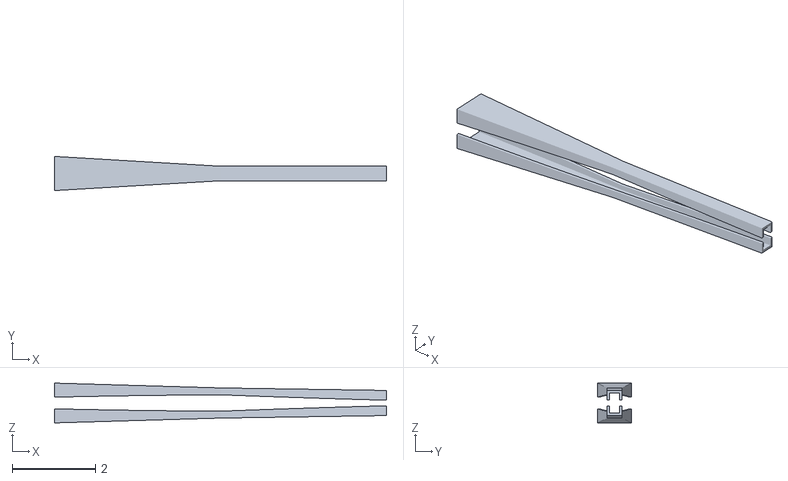
[picture p204: CAD file, 2026-04-21]
models_3d/optimization_v2_q7777.stl
8.00 x 0.823 x 0.959
