NikhilVeeram/MEEN-305-FINAL/models_3d/optimization_v2_e.stl

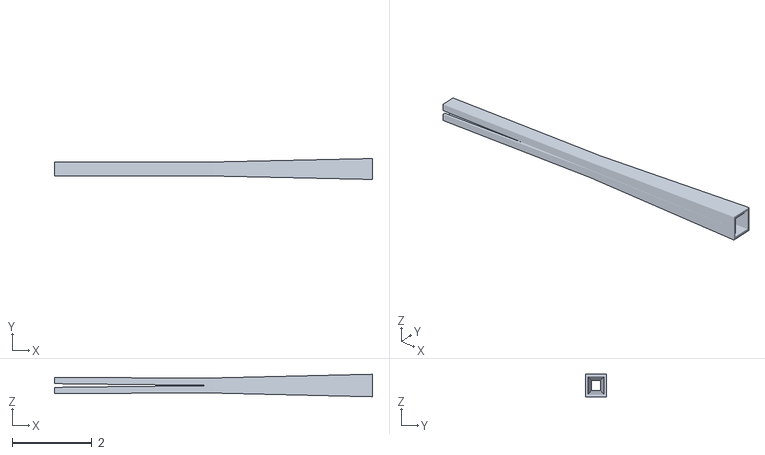
[picture p205: CAD file, 2026-04-21]
models_3d/optimization_v2_e.stl
8.00 x 0.527 x 0.567
