NikhilVeeram/MEEN-305-FINAL/models_3d/optimization_v2_f.stl

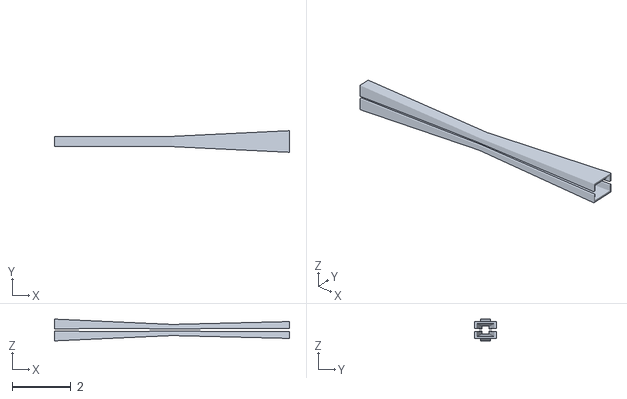
[picture p206: CAD file, 2026-04-21]
models_3d/optimization_v2_f.stl
8.00 x 0.737 x 0.743
