NikhilVeeram/MEEN-305-FINAL/models_3d/optimization_v2_i.stl

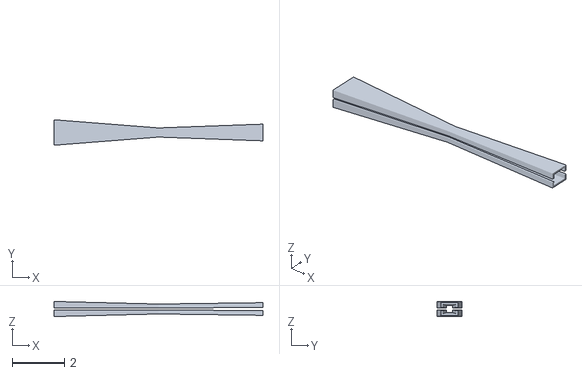
[picture p207: CAD file, 2026-04-21]
models_3d/optimization_v2_i.stl
8.00 x 0.975 x 0.577
