NikhilVeeram/MEEN-305-FINAL/models_3d/optimization_connected_2026.stl

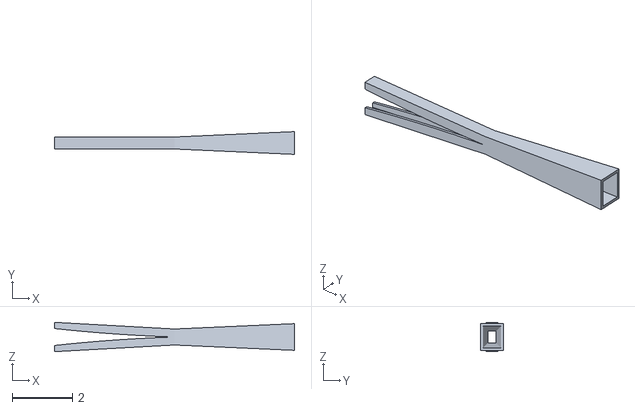
[picture p208: CAD file, 2026-04-21]
models_3d/optimization_connected_2026.stl
8.00 x 0.759 x 0.978
