NikhilVeeram/MEEN-305-FINAL/models_3d/sample_geometry.stl

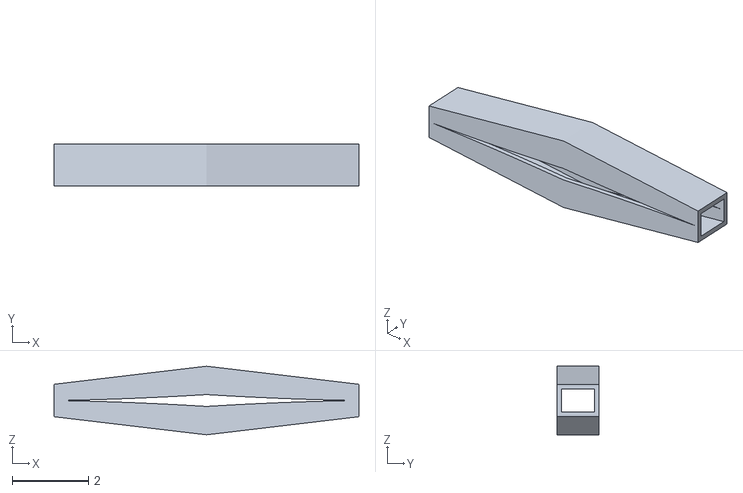
[picture p210: CAD file, 2026-04-21]
models_3d/sample_geometry.stl
8.00 x 1.10 x 1.80
