NikhilVeeram/MEEN-305-FINAL/models_3d/optimization_v2_b.stl

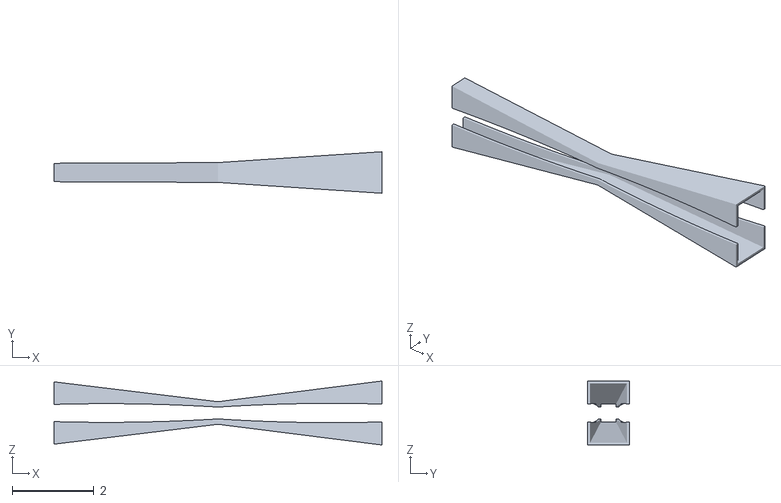
[picture p211: CAD file, 2026-04-21]
models_3d/optimization_v2_b.stl
8.00 x 1.01 x 1.56
