NikhilVeeram/MEEN-305-FINAL/models_3d/optimization_v2_q2025.stl

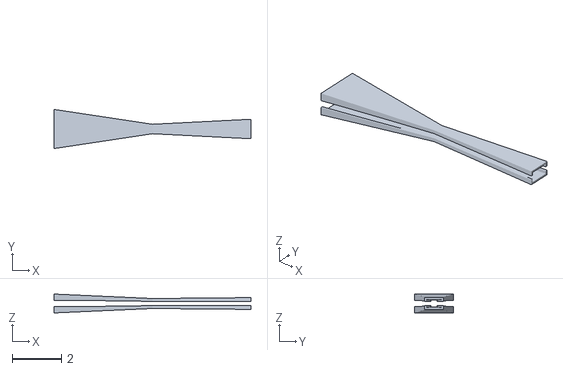
[picture p212: CAD file, 2026-04-21]
models_3d/optimization_v2_q2025.stl
8.00 x 1.59 x 0.768
