NikhilVeeram/MEEN-305-FINAL/best-designs-20/ranked-designs/17_overall_rank__print_safe_contiguous_closed_tube_seed2502__eval_1066__w_0.04048__fos_1.674/README.md

# Rank 17: print_safe_contiguous_closed_tube_seed2502 eval 1066

- Weight-first rank score: `0.040480`
- Weight: `0.04048 lbf`
- Minimum FoS: `1.674`
- Max deflection: `0.12217 in`
- LC2 FoS, x=3..7: mean `2.294`, std `0.438`, range `1.590`
- Print checks: wall `0.060 in`, max opening `0.000`, min ligament `0.191 in`
- Governing case/location: `Load Case 2` at `x = 5.500 in`
- Source run: `print_safe_contiguous_closed_tube_seed2502`
- Source evaluation id: `1066`

This folder is a ranked report artifact generated from a feasible, corrected 9 in design candidate.
