NikhilVeeram/MEEN-305-FINAL/best-designs-20/design-packages/17_overall_rank__print_safe_contiguous_closed_tube_seed2502__eval_1066__w_0.04048__fos_1.674/README.md

# 17_overall_rank__print_safe_contiguous_closed_tube_seed2502__eval_1066__w_0.04048__fos_1.674

- Included files:
  - `17_overall_rank__print_safe_contiguous_closed_tube_seed2502__eval_1066__w_0.04048__fos_1.674.stl`
  - `17_overall_rank__print_safe_contiguous_closed_tube_seed2502__eval_1066__w_0.04048__fos_1.674.obj`
  - `17_overall_rank__print_safe_contiguous_closed_tube_seed2502__eval_1066__w_0.04048__fos_1.674_preview.png`
  - `17_overall_rank__print_safe_contiguous_closed_tube_seed2502__eval_1066__w_0.04048__fos_1.674.dxf`
  - `best_design.json`
  - `optimization_report.md`
  - `optimization_report.tex`
  - `beam_parameter_map.png`
  - `best_design/*.png`

The PNG preview is the 3D look. The DXF file is a lightweight 2D sketch export.
