NikhilVeeram/MEEN-305-FINAL/designs/active_runs/flat_3to7_lc2_ranksearch_print_safe_seed2405/beam_parameter_map.png

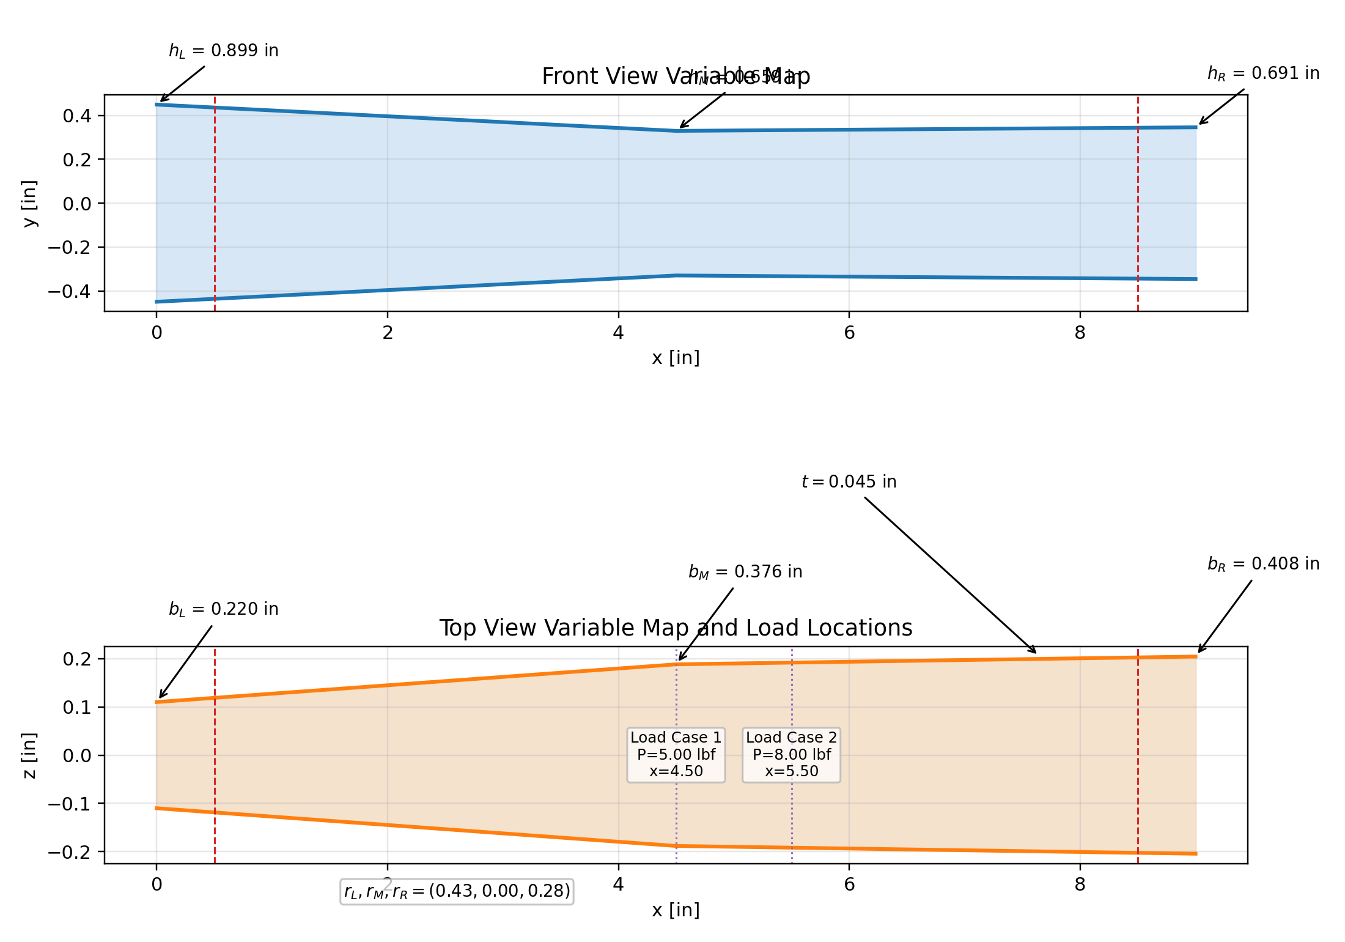
designs/active_runs/flat_3to7_lc2_ranksearch_print_safe_seed2405/beam_parameter_map.png
