NikhilVeeram/MEEN-305-FINAL/designs/active_runs/print_safe_contiguous_low_opening_seed2501/beam_parameter_map.png

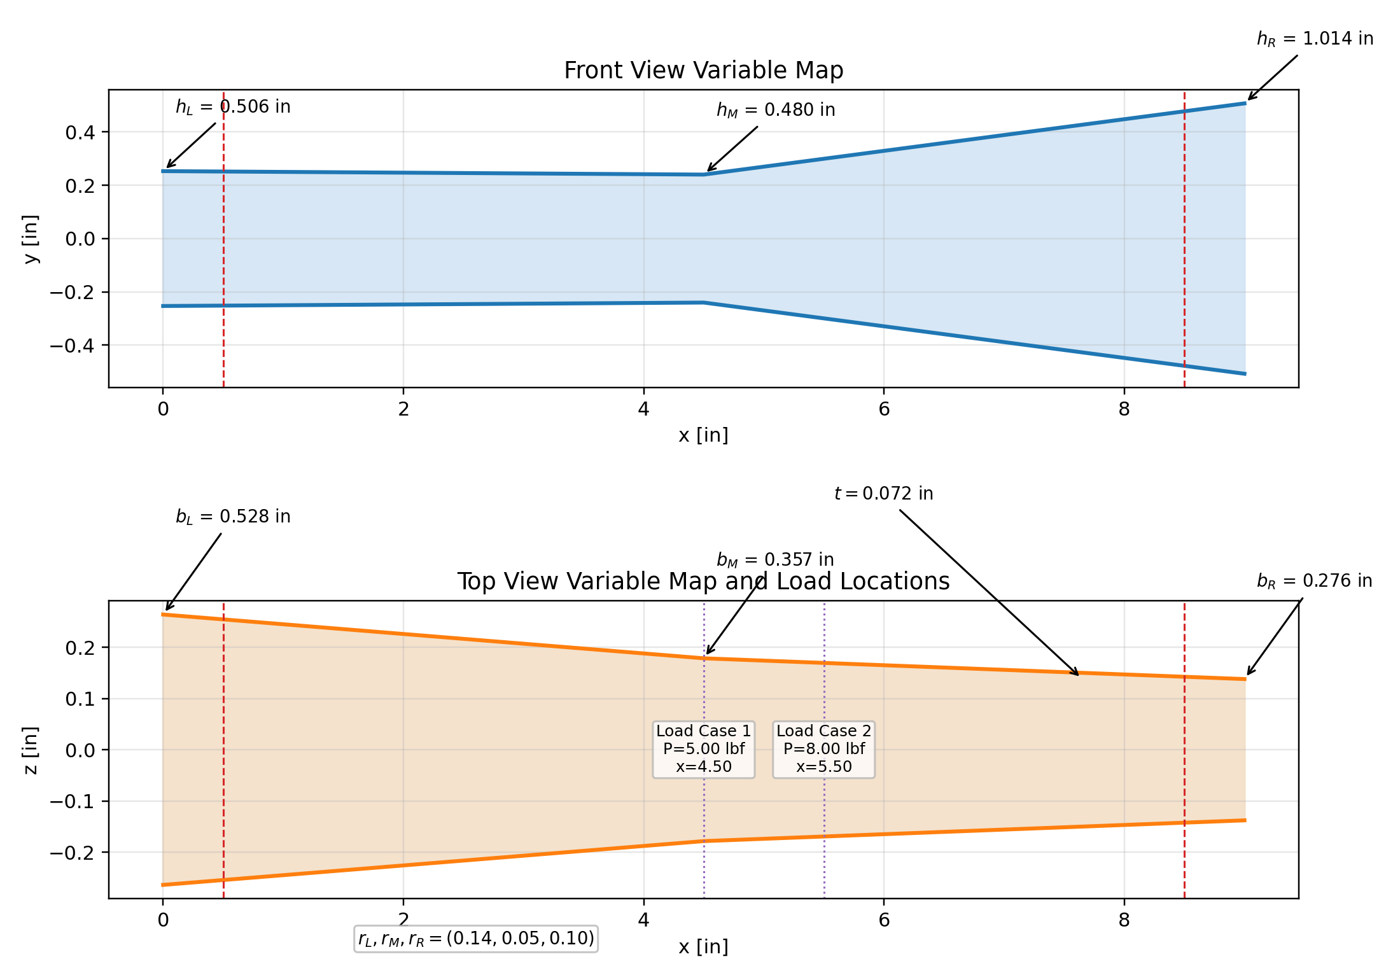
designs/active_runs/print_safe_contiguous_low_opening_seed2501/beam_parameter_map.png
