NikhilVeeram/MEEN-305-FINAL/designs/active_runs/print_safe_contiguous_stiff_seed2503/beam_parameter_map.png

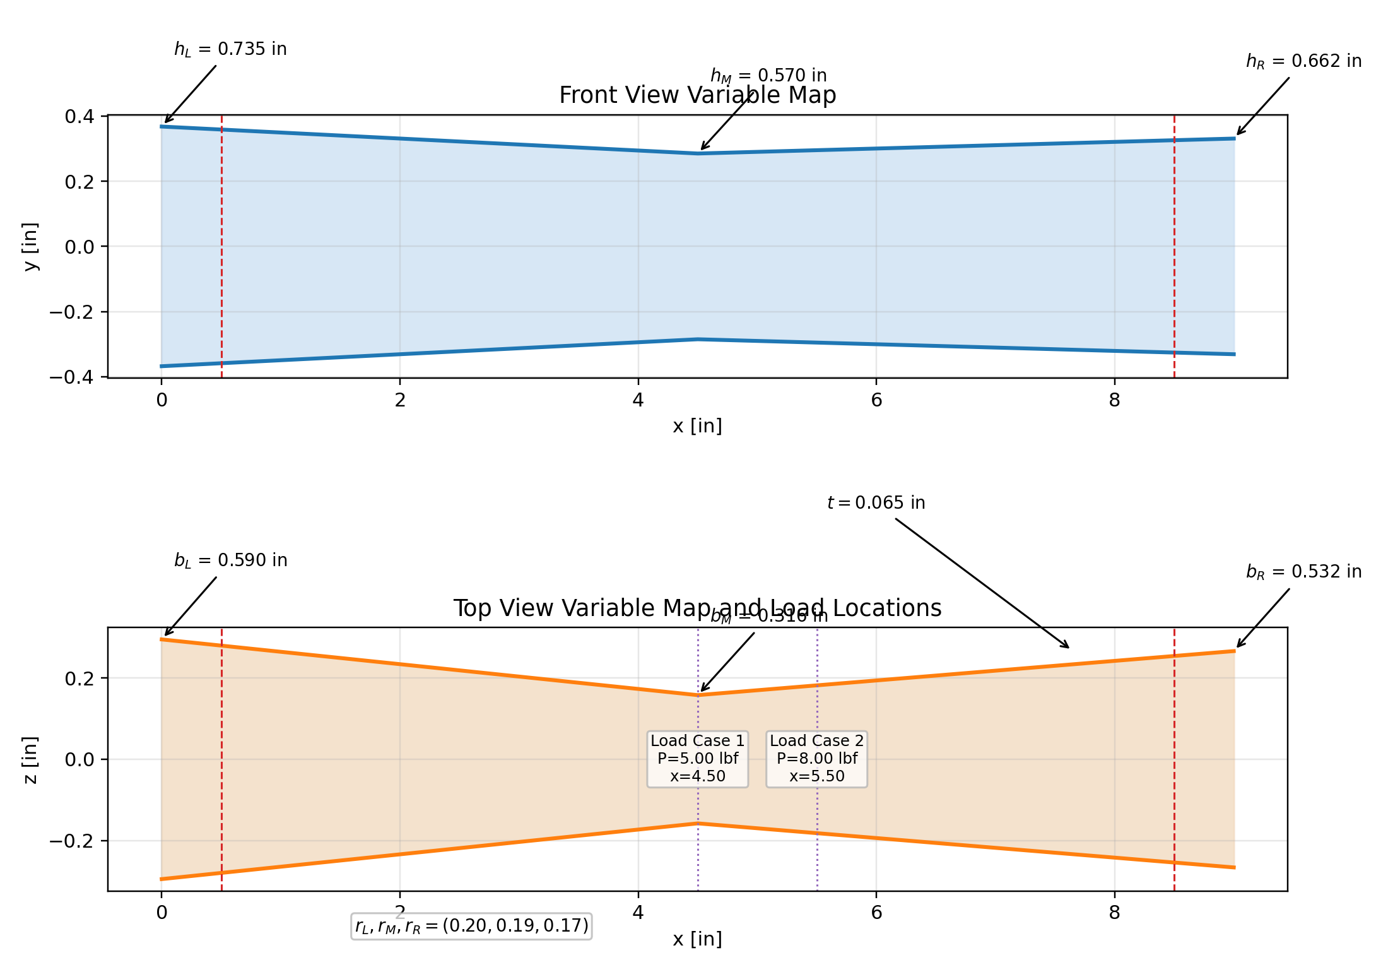
designs/active_runs/print_safe_contiguous_stiff_seed2503/beam_parameter_map.png
