NikhilVeeram/MEEN-305-FINAL/docs/reports/peer_evaluation_team6.tex

\documentclass[letterpaper,11pt]{article}
\usepackage[margin=0in]{geometry}
\usepackage{graphicx}
\usepackage{tikz}
\pagestyle{empty}

\begin{document}
\noindent\raisebox{-\paperheight}[0pt][0pt]{%
  %
}
\begin{tikzpicture}[remember picture,overlay,x=1in,y=1in]

  % Top identification fields.
  \node[anchor=west] at ([xshift=1.55in,yshift=-0.62in]current page.north west) {Nikhil Veeramachaneni};
  \node[anchor=west] at ([xshift=7.75in,yshift=-0.70in]current page.north west) {6};

  % TEAM field.
  \fill[white] ([xshift=1.54in,yshift=-2.81in]current page.north west) rectangle
    ([xshift=1.78in,yshift=-2.54in]current page.north west);
  \node[anchor=west] at ([xshift=1.56in,yshift=-2.65in]current page.north west) {6};

  % Table row coordinates.
  \node[anchor=west,font=\fontsize{6}{7}\selectfont] at ([xshift=1.20in,yshift=-4.25in]current page.north west) {Chauncey Patrick};
  \node[anchor=west,font=\fontsize{6}{7}\selectfont] at ([xshift=1.20in,yshift=-4.43in]current page.north west) {Brennan Stanley};
  \node[anchor=west,font=\fontsize{6}{7}\selectfont] at ([xshift=1.20in,yshift=-4.61in]current page.north west) {Nikhil Veeramachaneni};

  % Scores: analysis, fabrication, testing, writing, tasks, communication, total.
  \foreach \y in {-4.25,-4.43,-4.61} {
    \node[font=\scriptsize] at ([xshift=2.44in,yshift=\y in]current page.north west) {5};
    \node[font=\scriptsize] at ([xshift=3.18in,yshift=\y in]current page.north west) {5};
    \node[font=\scriptsize] at ([xshift=3.90in,yshift=\y in]current page.north west) {5};
    \node[font=\scriptsize] at ([xshift=4.62in,yshift=\y in]current page.north west) {5};
    \node[font=\scriptsize] at ([xshift=5.52in,yshift=\y in]current page.north west) {5};
    \node[font=\scriptsize] at ([xshift=6.53in,yshift=\y in]current page.north west) {5};
    \node[font=\scriptsize] at ([xshift=7.25in,yshift=\y in]current page.north west) {30};
  }

  % Additional comments, five lines maximum.
  \node[anchor=west,font=\small] at ([xshift=1.00in,yshift=-5.97in]current page.north west) {Chauncey Patrick contributed to fabrication planning, testing support, and final documentation.};
  \node[anchor=west,font=\small] at ([xshift=1.00in,yshift=-6.16in]current page.north west) {Brennan Stanley helped with beam fabrication, experimental setup, and report review.};
  \node[anchor=west,font=\small] at ([xshift=1.00in,yshift=-6.37in]current page.north west) {Nikhil Veeramachaneni contributed to analysis, design iteration, testing, and report assembly.};
  \node[anchor=west,font=\small] at ([xshift=1.00in,yshift=-6.58in]current page.north west) {All members communicated reliably and completed assigned work on time.};
  \node[anchor=west,font=\small] at ([xshift=1.00in,yshift=-6.77in]current page.north west) {No concerns; each teammate earned full credit for their project contributions.};
\end{tikzpicture}
\null
\end{document}
