NikhilVeeram/MEEN-305-FINAL/best-designs-20/design-packages/11_overall_rank__continuous_uniform_both_load_cases_9in_corrected__eval_0572__w_0.03504__fos_1.877/best_design/load_case_2_results.png

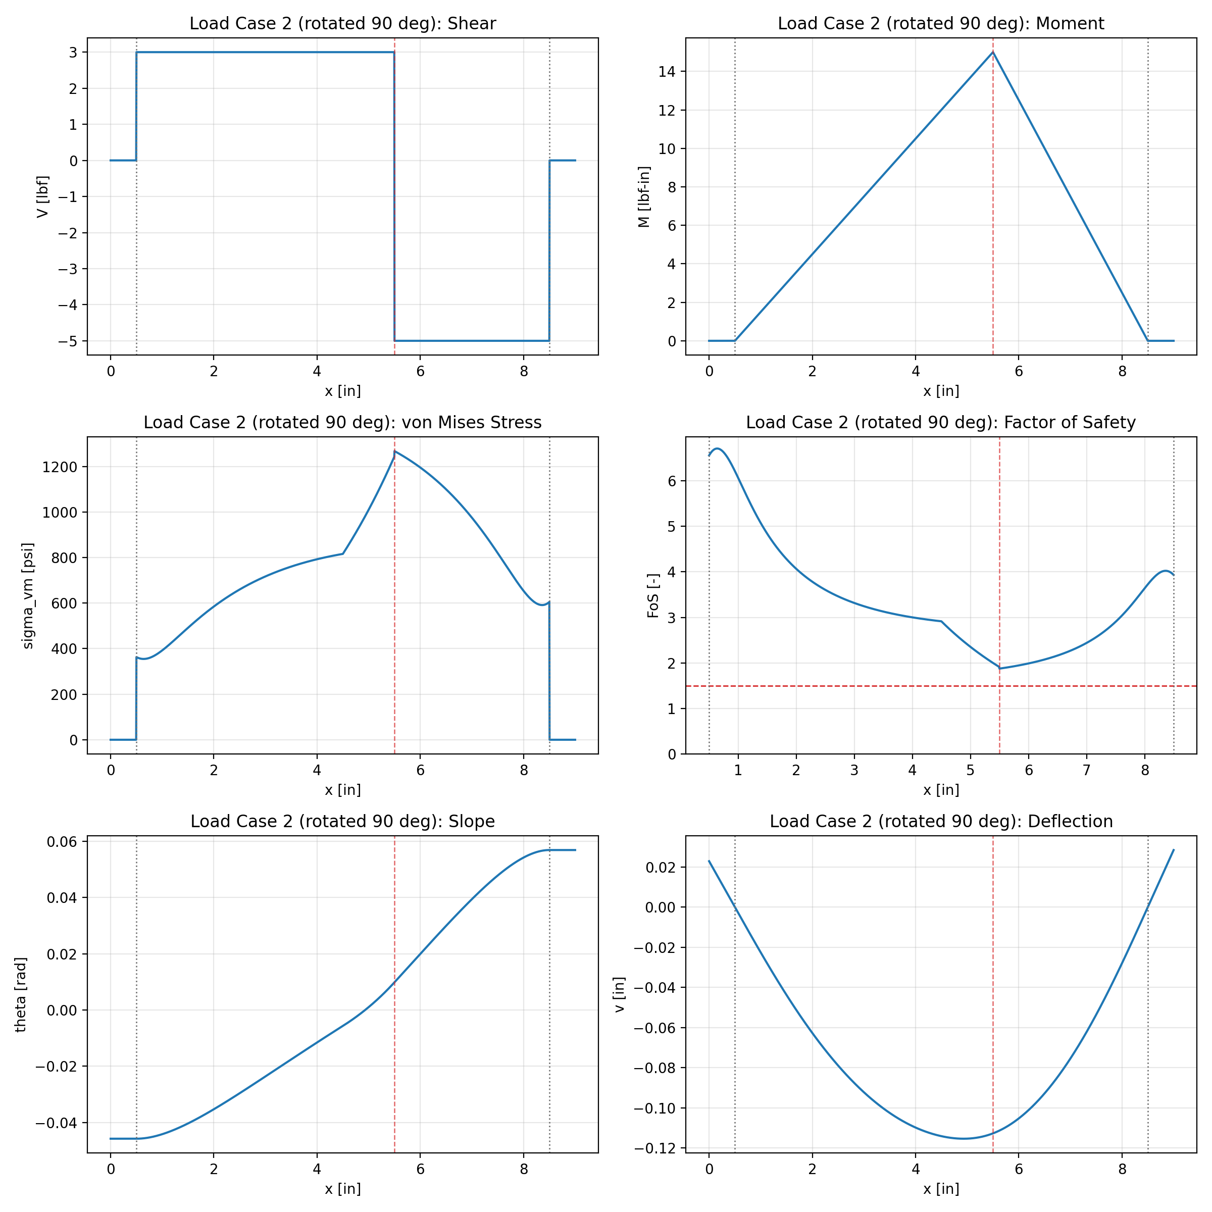
best-designs-20/design-packages/11_overall_rank__continuous_uniform_both_load_cases_9in_corrected__eval_0572__w_0.03504__fos_1.877/best_design/load_case_2_results.png
