NikhilVeeram/MEEN-305-FINAL/best-designs-20/design-packages/13_overall_rank__ultra_light_runa_seed2430__eval_2464__w_0.03652__fos_2.154/best_design/load_case_1_results.png

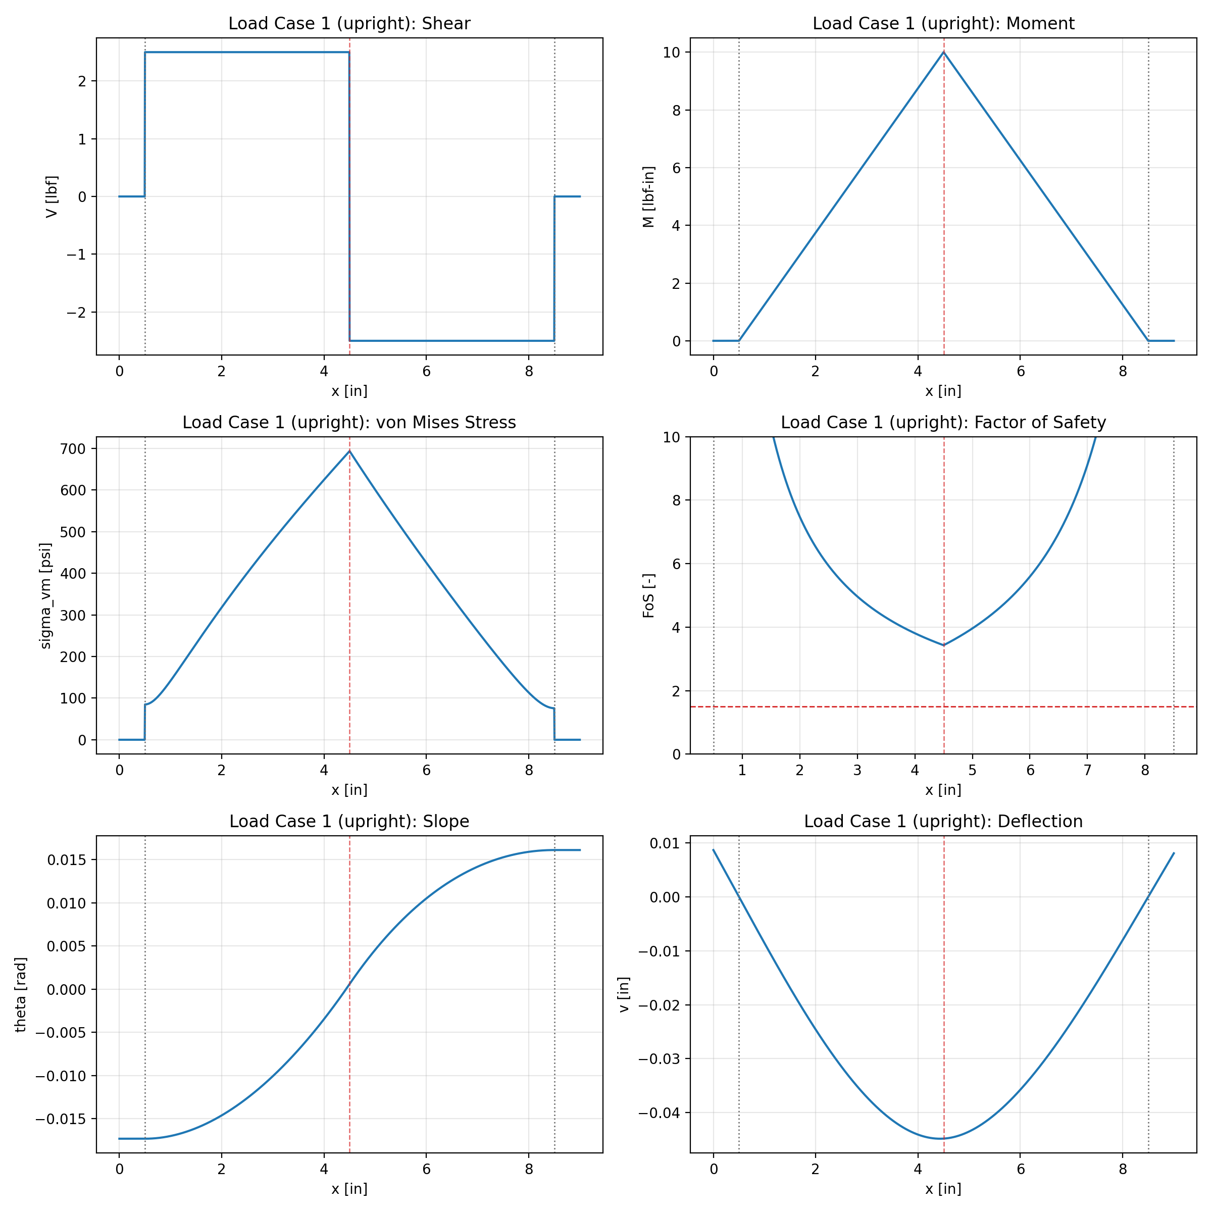
best-designs-20/design-packages/13_overall_rank__ultra_light_runa_seed2430__eval_2464__w_0.03652__fos_2.154/best_design/load_case_1_results.png
