NikhilVeeram/MEEN-305-FINAL/designs/active_runs/continuous_uniform_load_case_1/best_design/load_case_2_results.png

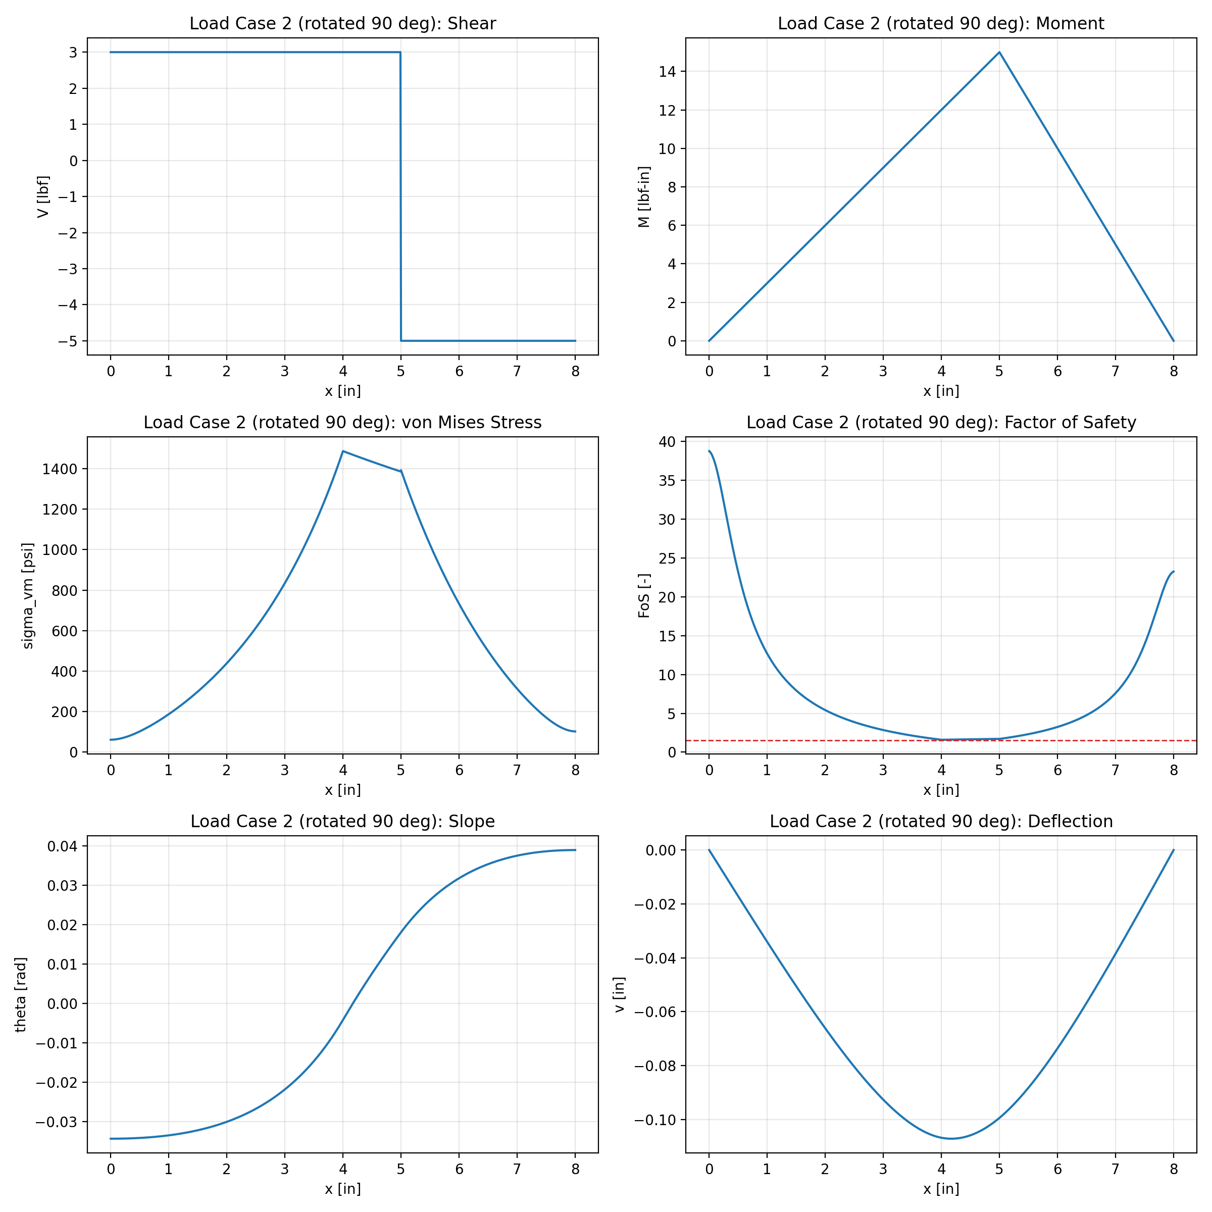
designs/active_runs/continuous_uniform_load_case_1/best_design/load_case_2_results.png
