NikhilVeeram/MEEN-305-FINAL/designs/active_runs/ultra_light_full_infill_seed2432/best_design/load_case_2_results.png

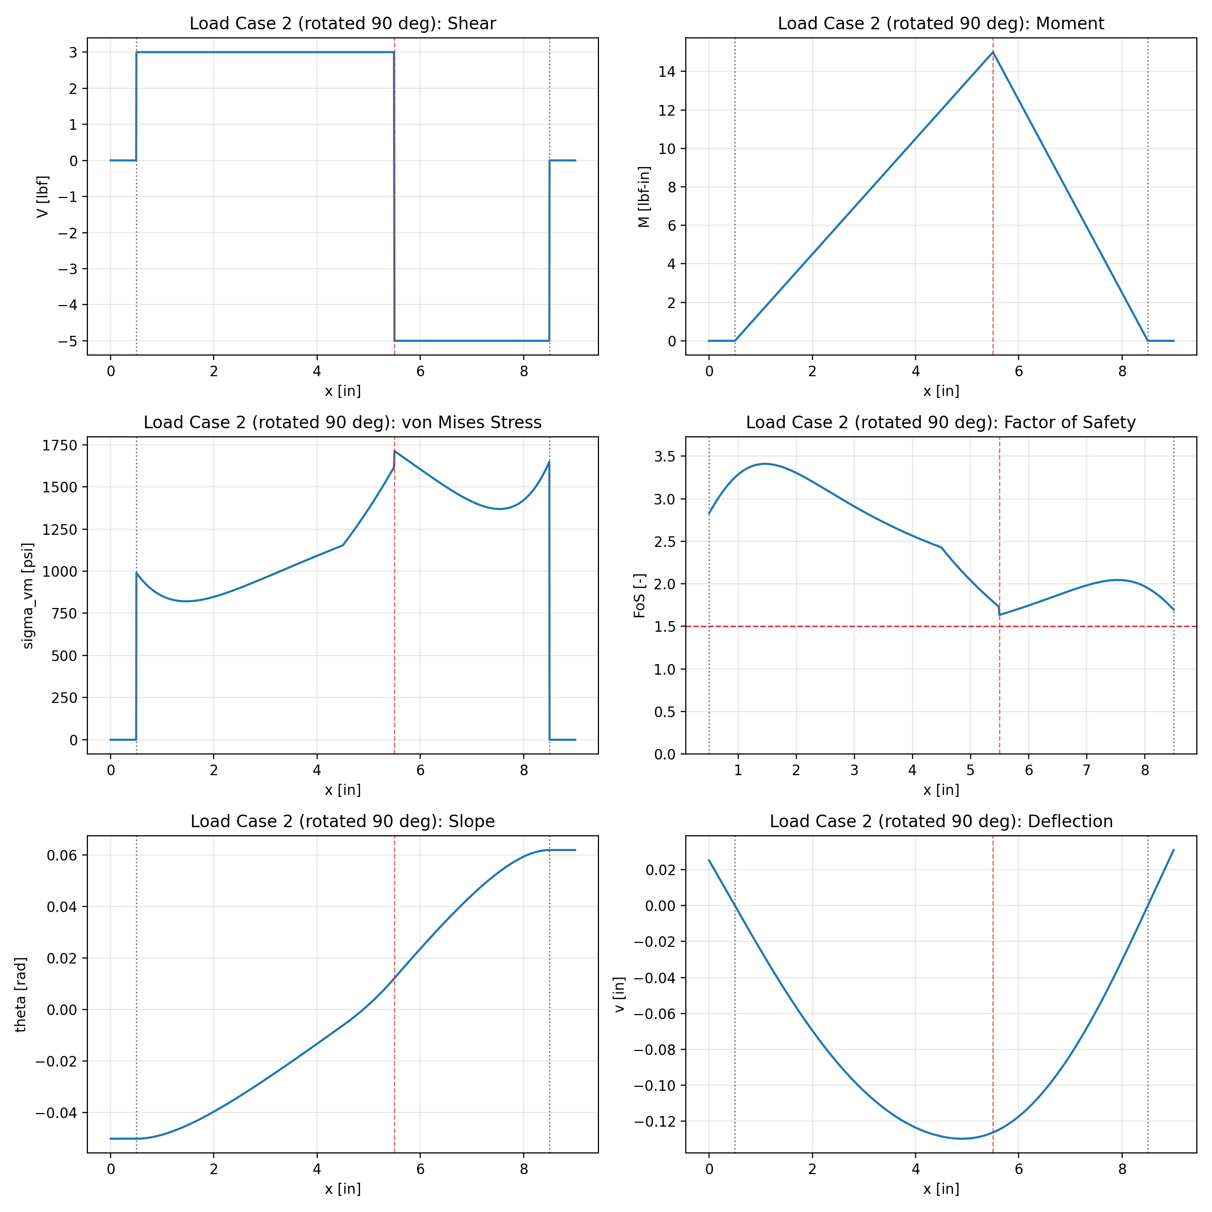
designs/active_runs/ultra_light_full_infill_seed2432/best_design/load_case_2_results.png
