NikhilVeeram/MEEN-305-FINAL/designs/active_runs/ultra_light_run2_seed2425/best_design/load_case_1_results.png

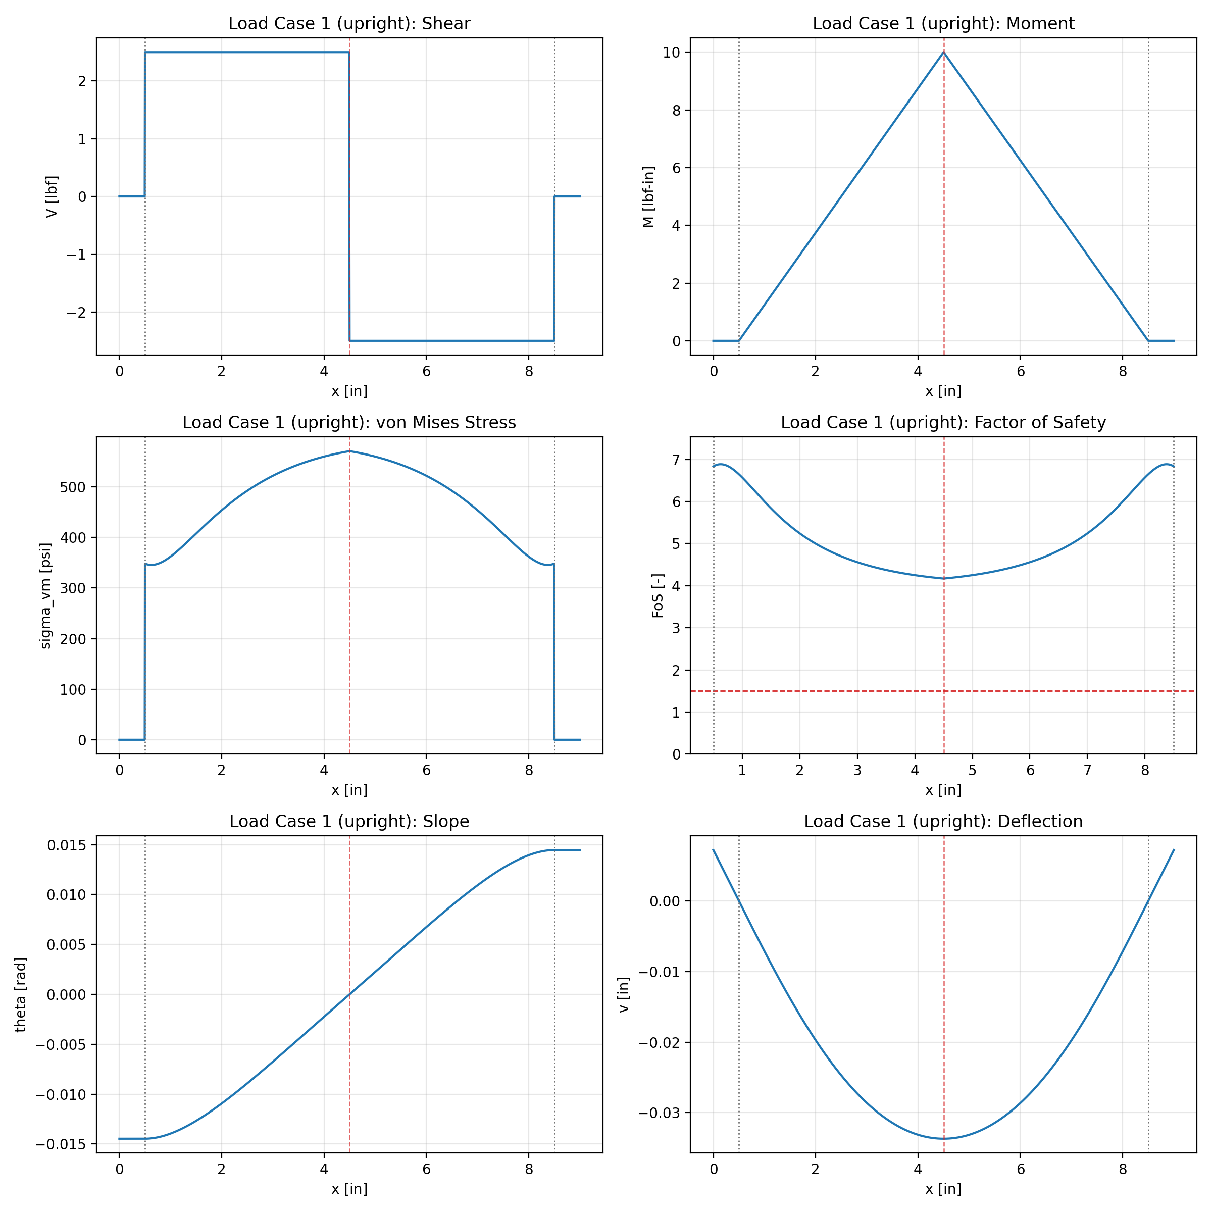
designs/active_runs/ultra_light_run2_seed2425/best_design/load_case_1_results.png
