NikhilVeeram/MEEN-305-FINAL/models_3d/optimization_smoke_test_preview.png

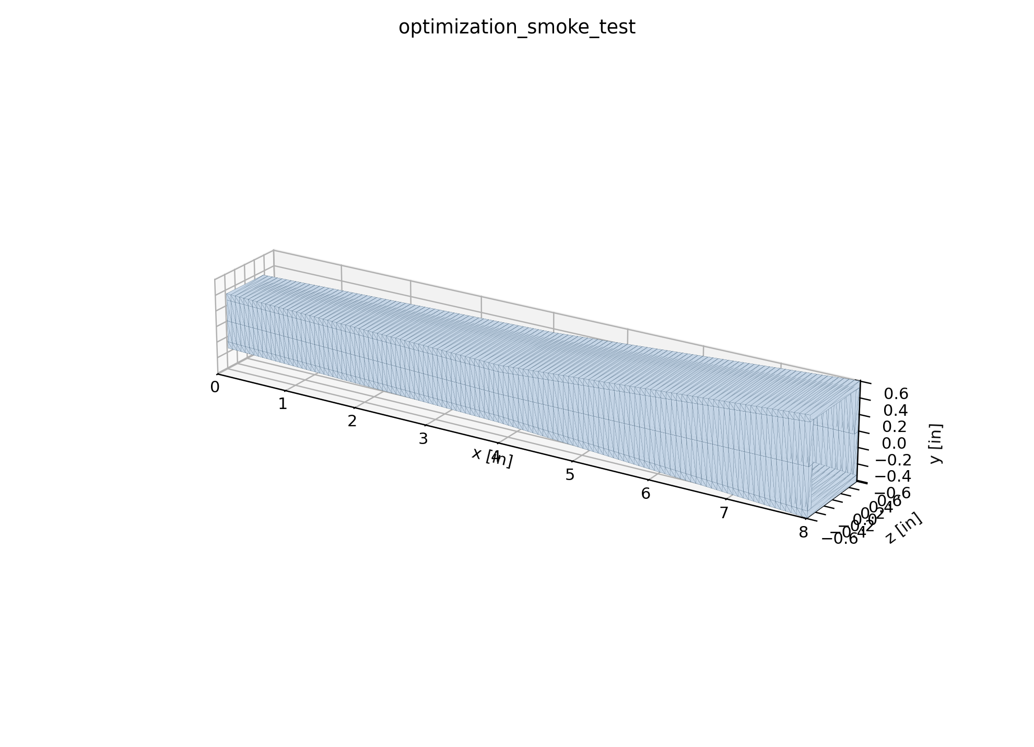
models_3d/optimization_smoke_test_preview.png
