NikhilVeeram/MEEN-305-FINAL/optimization_connected_2026/best_design/load_case_2_results.png

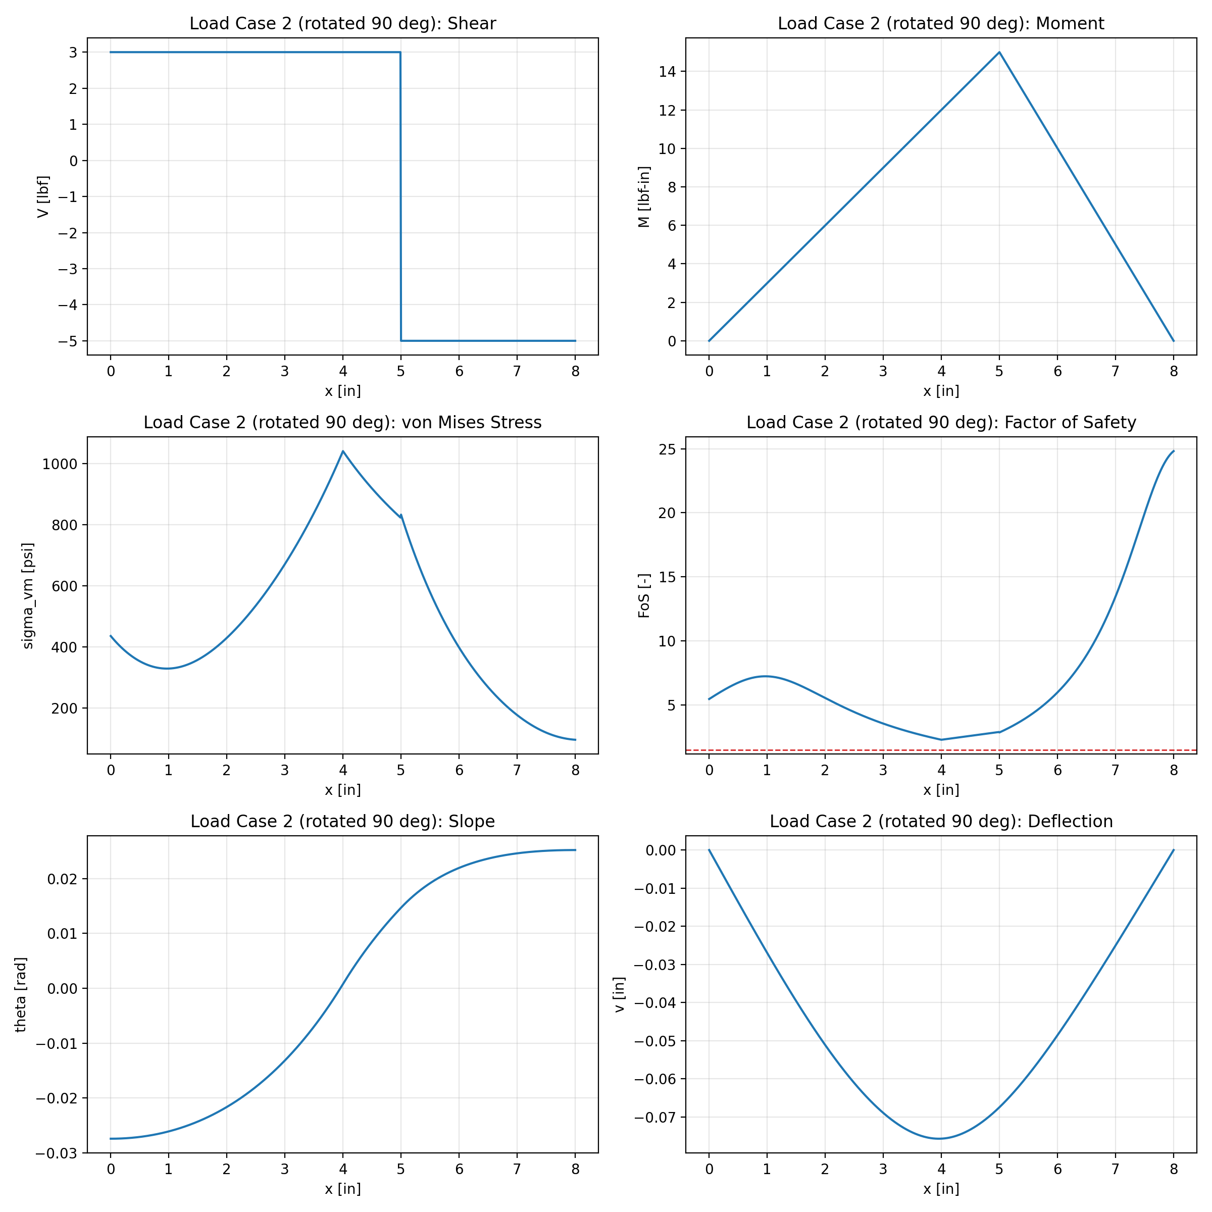
optimization_connected_2026/best_design/load_case_2_results.png
