NikhilVeeram/MEEN-305-FINAL/optimization_connected_v3/best_design/load_case_2_results.png

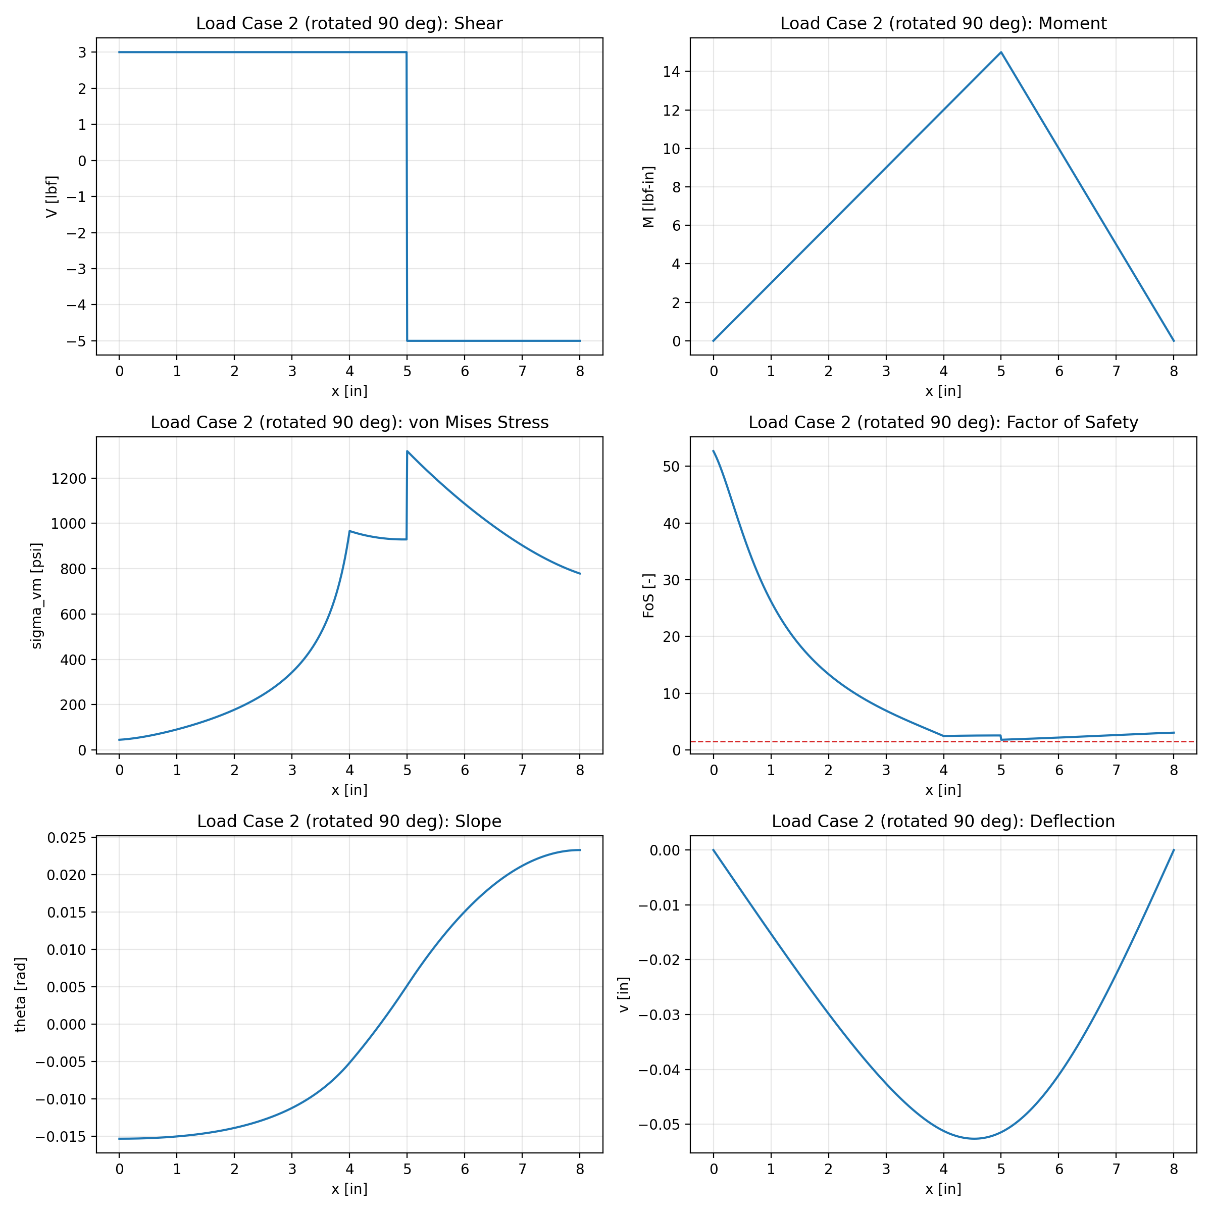
optimization_connected_v3/best_design/load_case_2_results.png
