NikhilVeeram/MEEN-305-FINAL/optimization_final/best_design/load_case_2_results.png

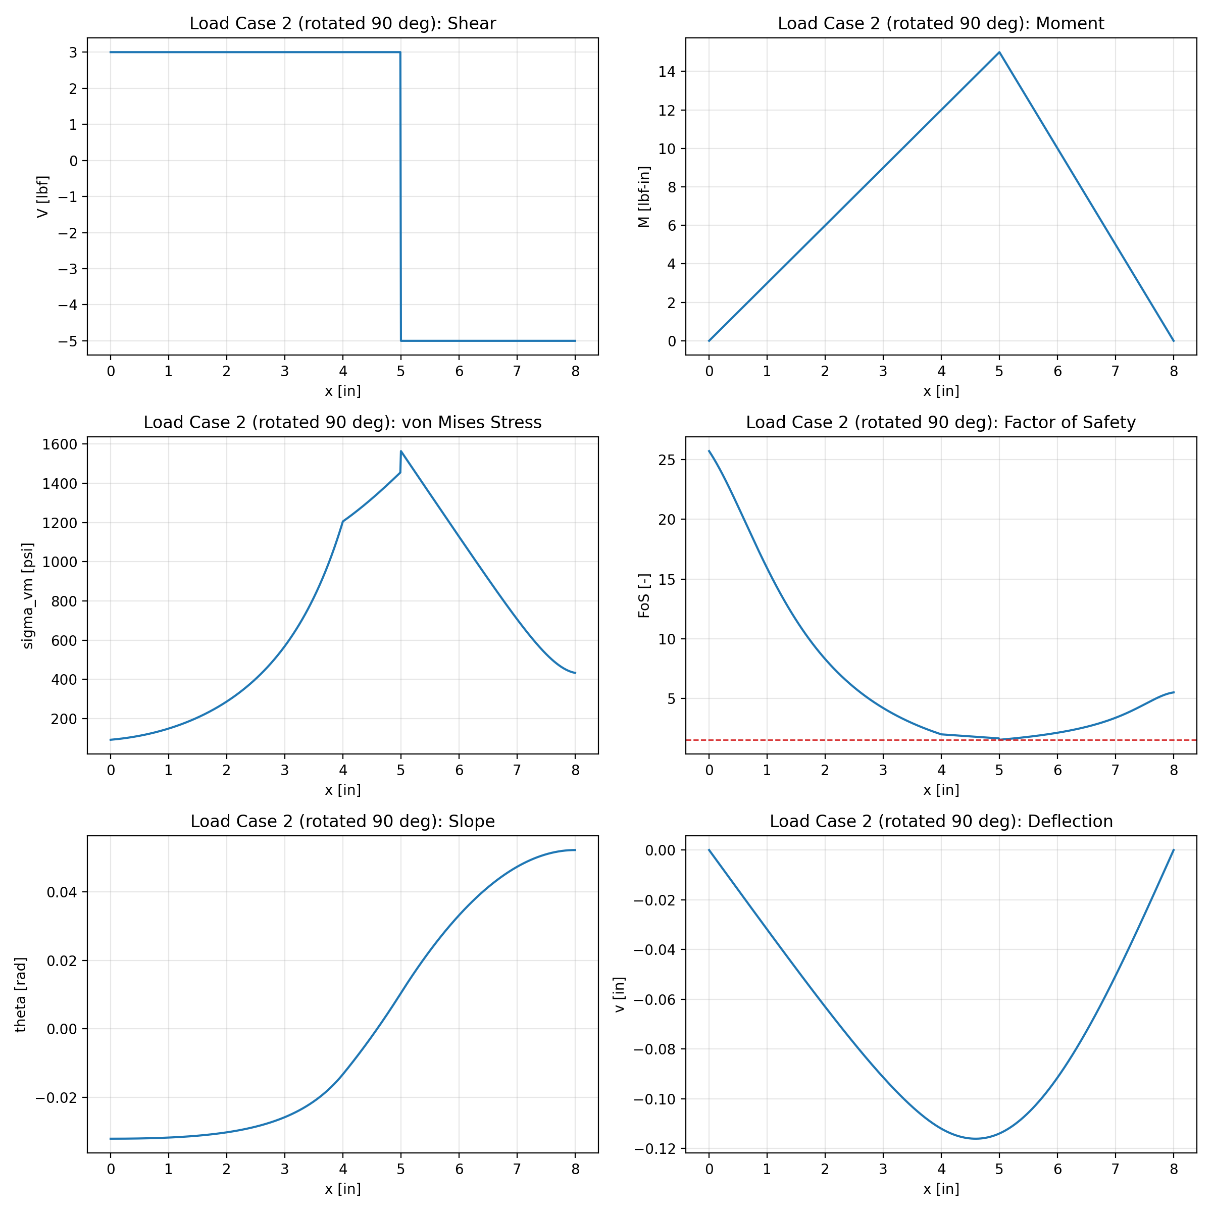
optimization_final/best_design/load_case_2_results.png
