NikhilVeeram/MEEN-305-FINAL/optimization_opening_smoke/best_design/load_case_1_results.png

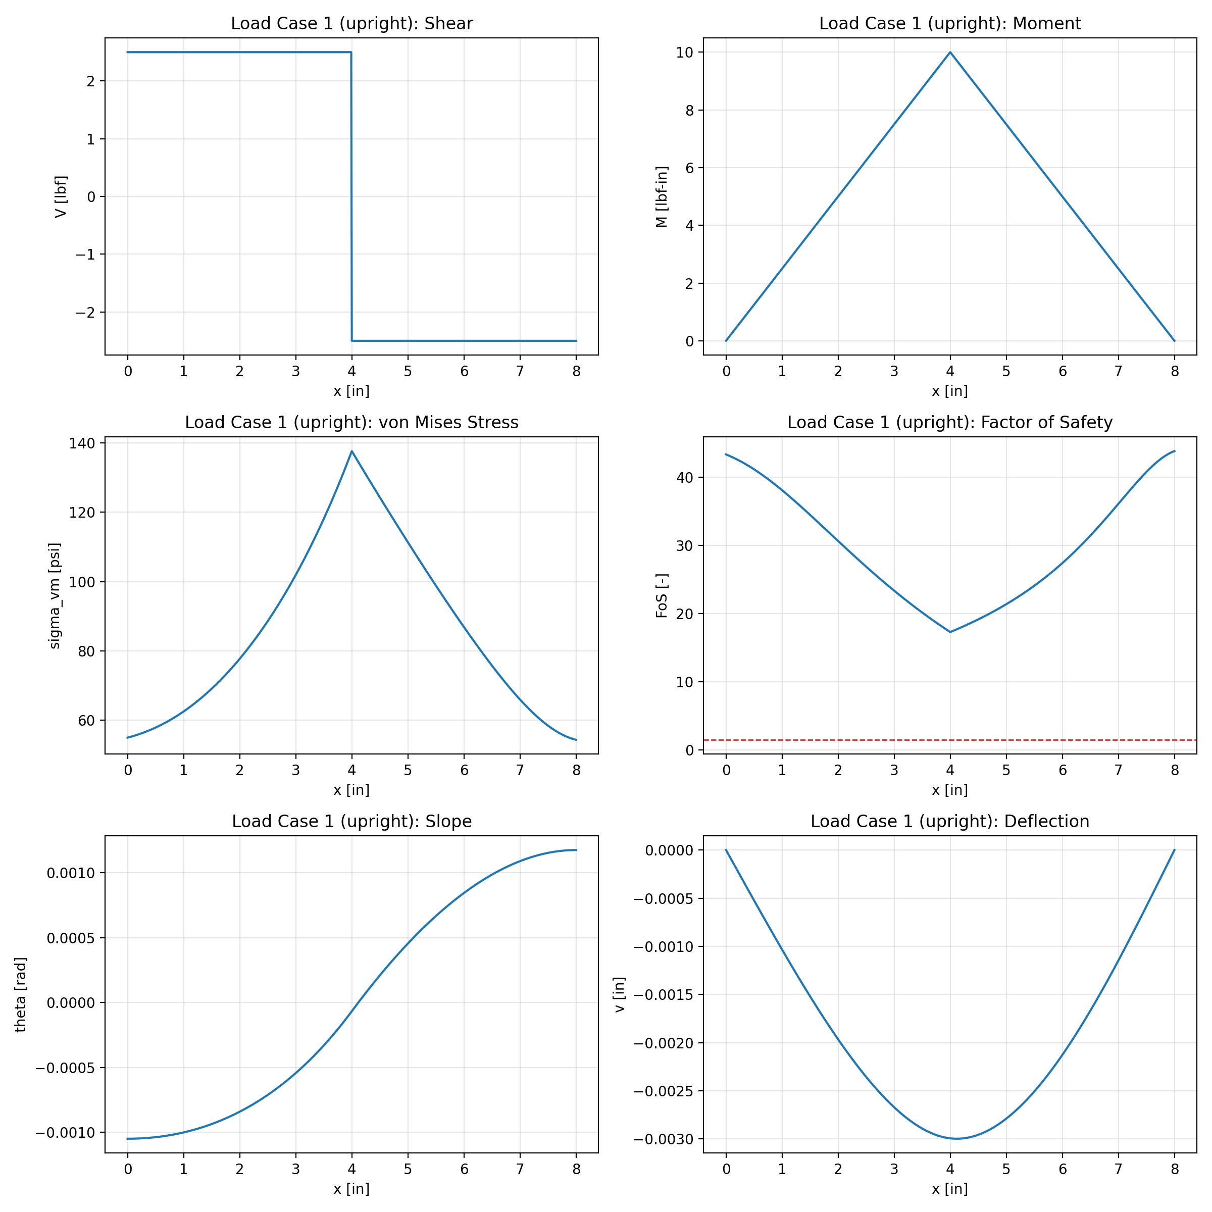
optimization_opening_smoke/best_design/load_case_1_results.png
