NikhilVeeram/MEEN-305-FINAL/optimization_opening_smoke/best_design/load_case_2_results.png

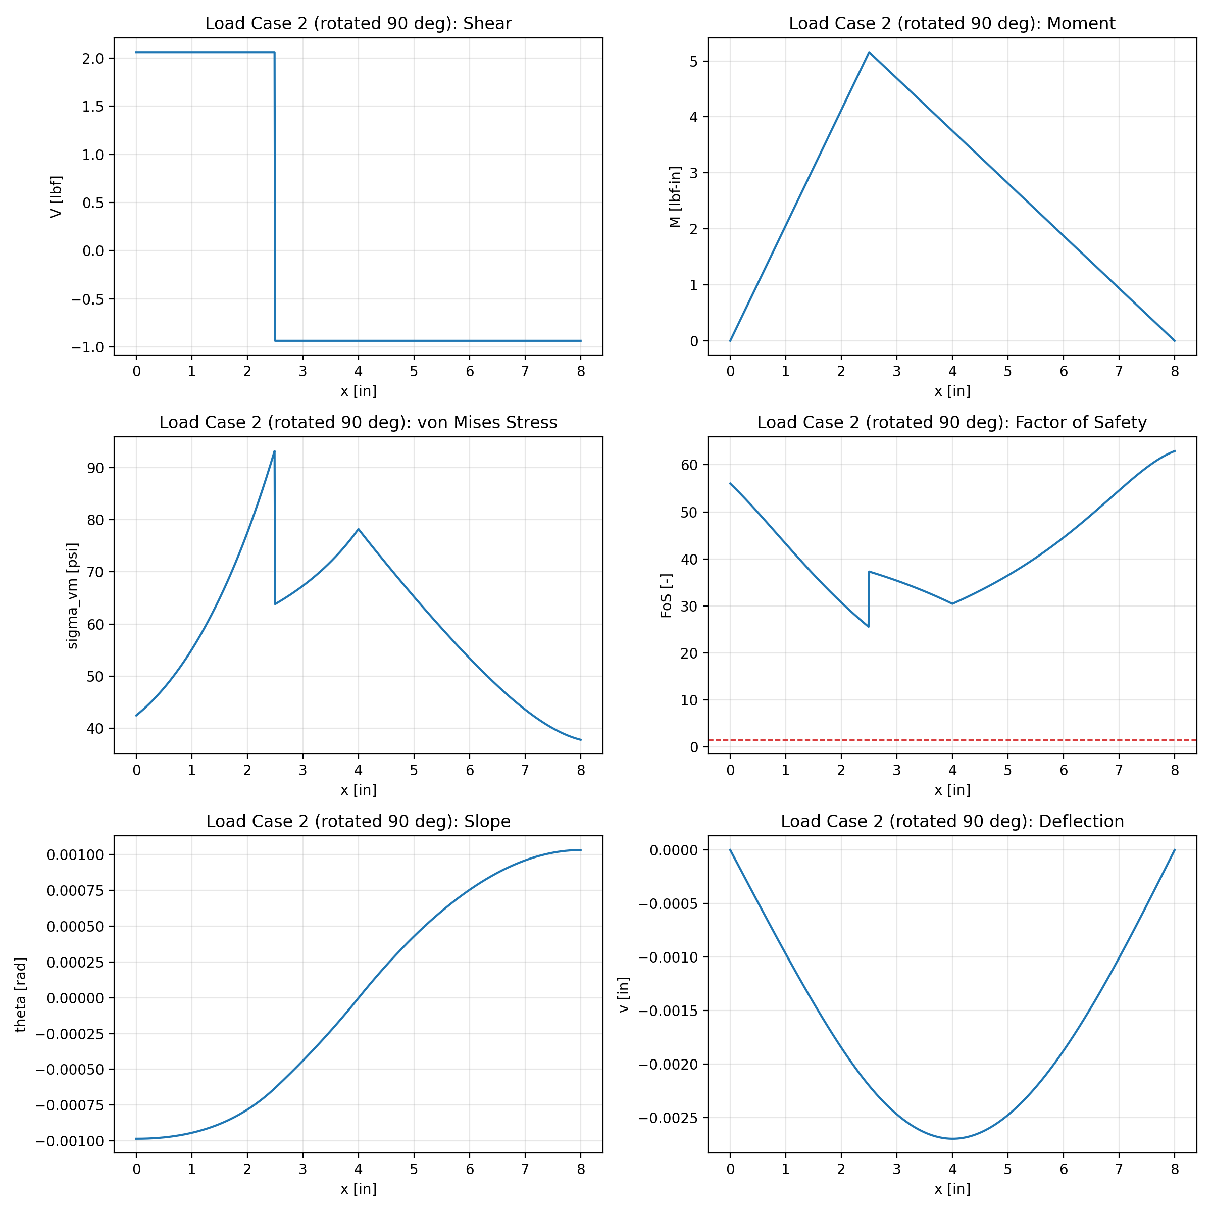
optimization_opening_smoke/best_design/load_case_2_results.png
