NikhilVeeram/MEEN-305-FINAL/optimization_outputs/best_design/load_case_1_results.png

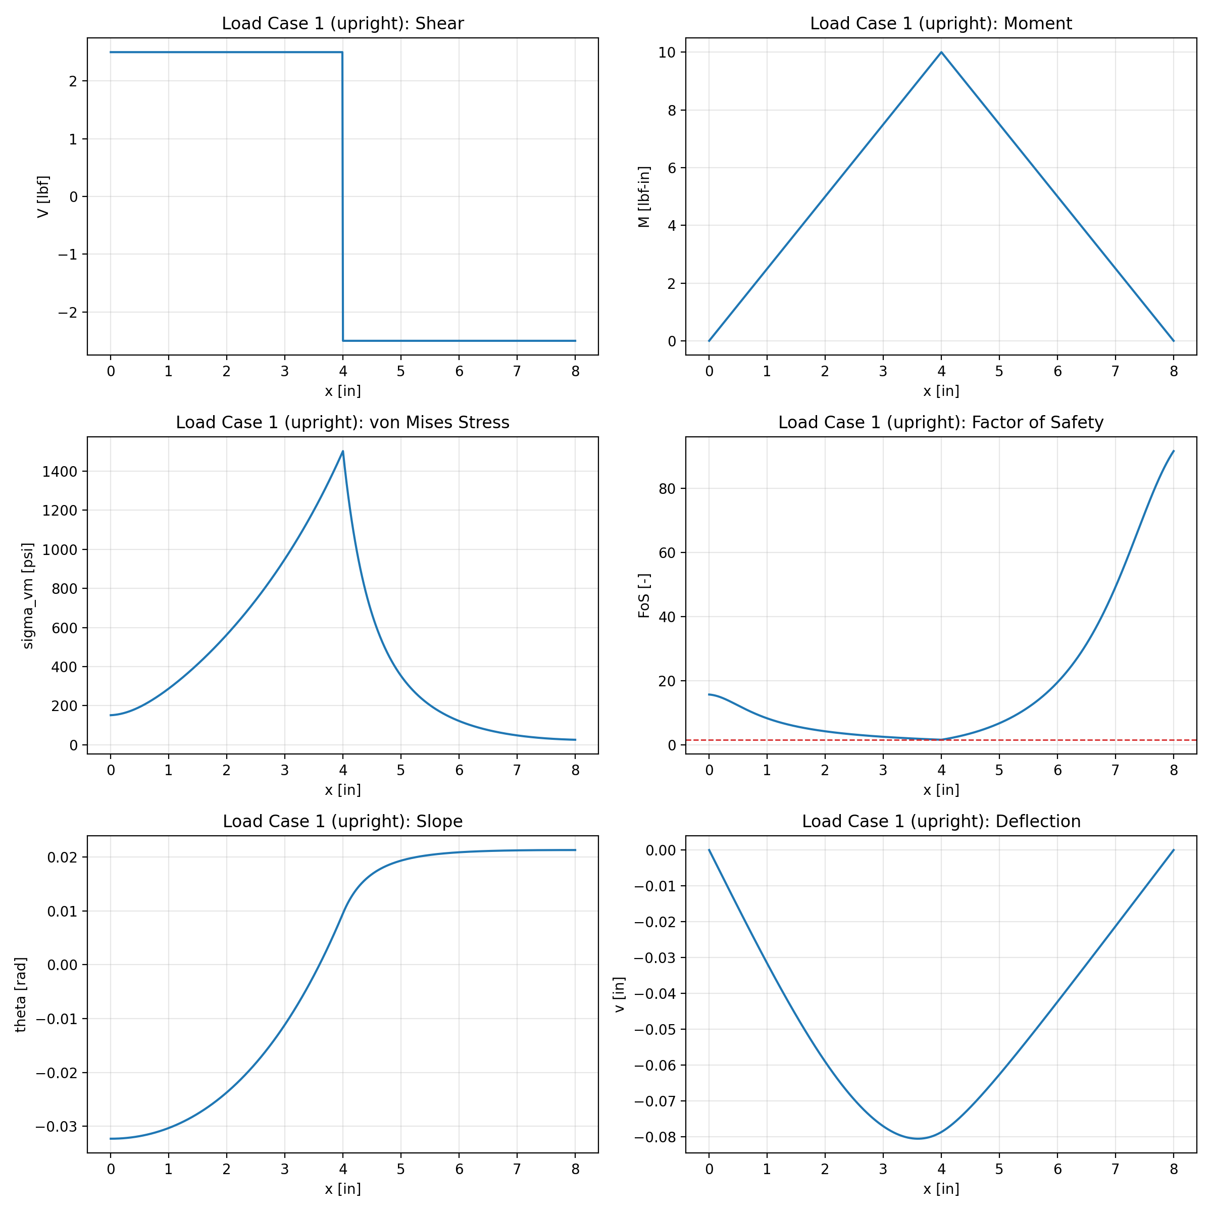
optimization_outputs/best_design/load_case_1_results.png
