NikhilVeeram/MEEN-305-FINAL/optimization_outputs/best_design/load_case_2_results.png

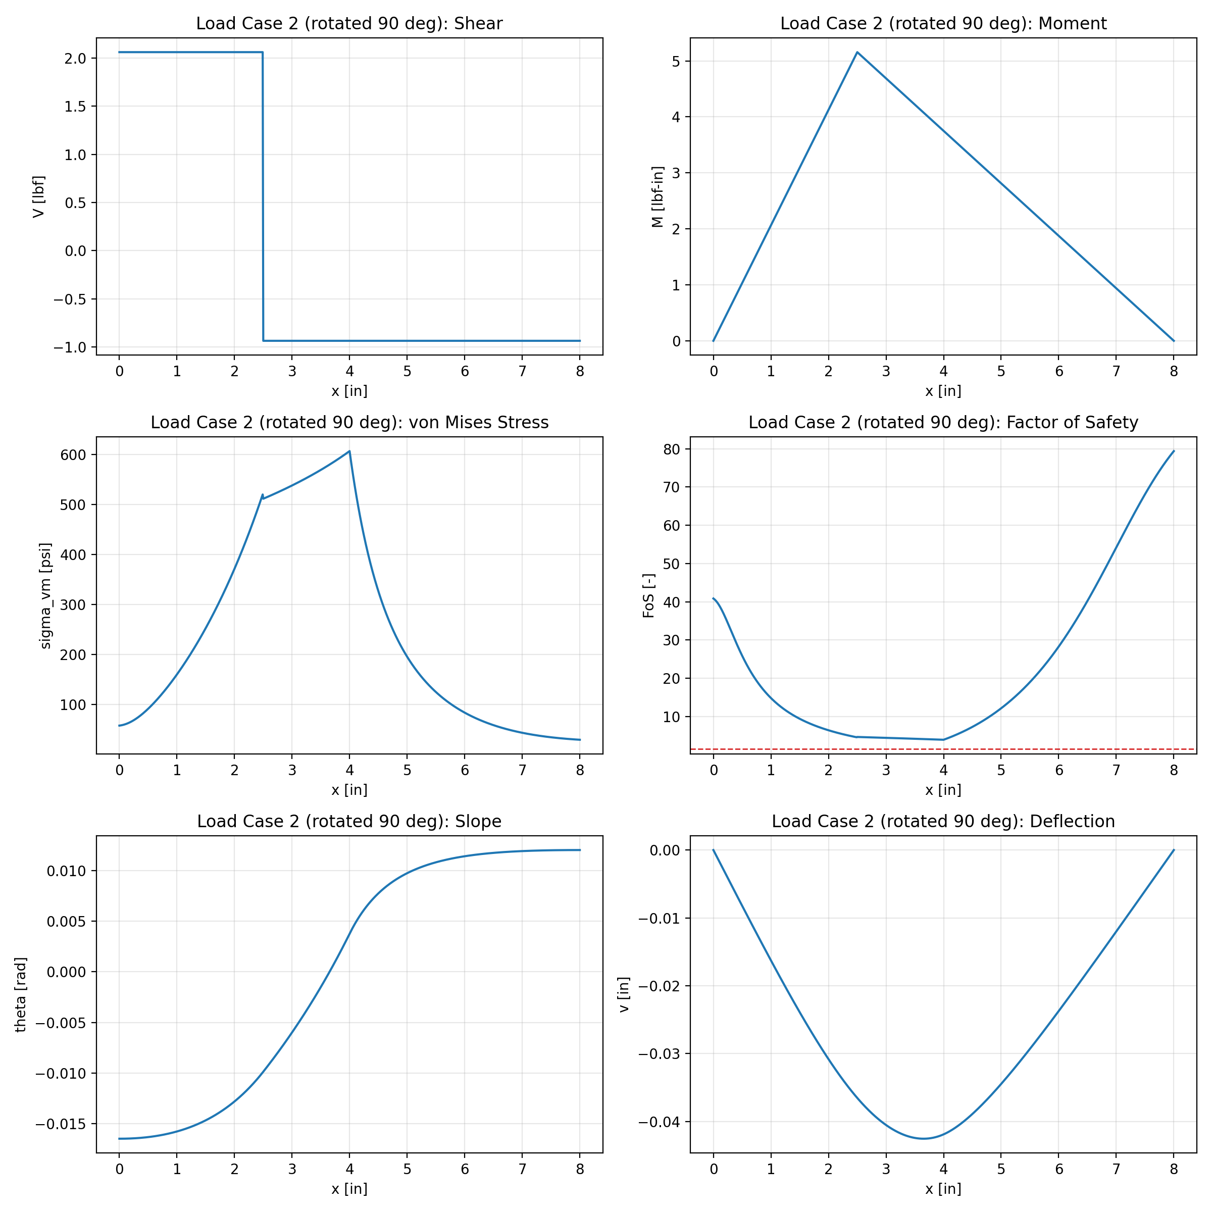
optimization_outputs/best_design/load_case_2_results.png
