NikhilVeeram/MEEN-305-FINAL/optimization_targeted/best_design/load_case_1_results.png

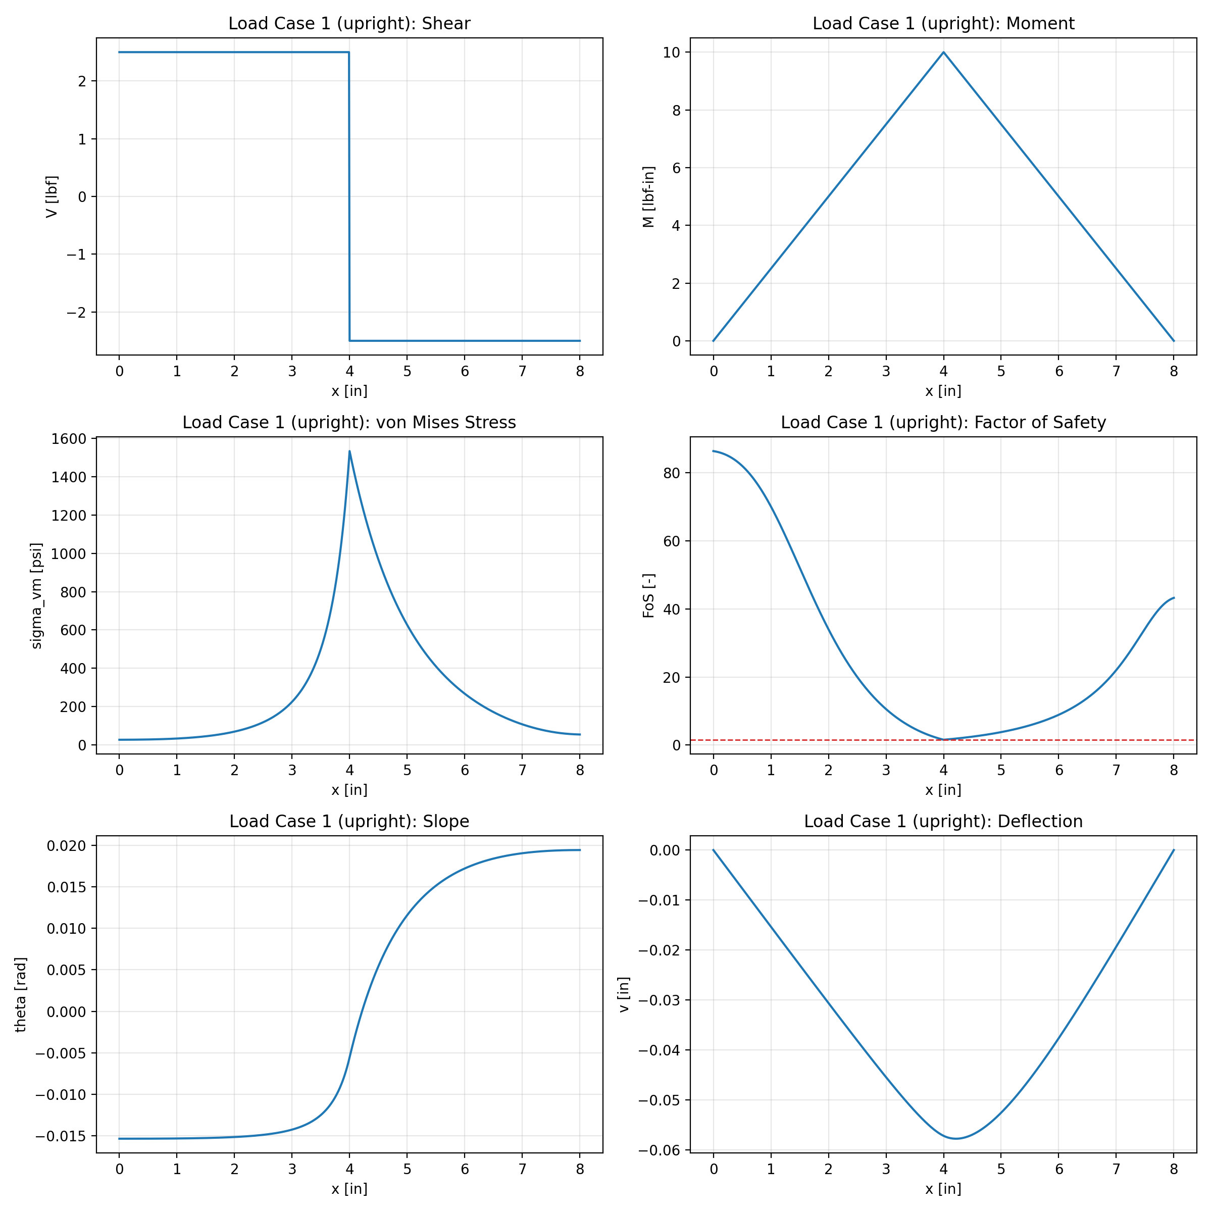
optimization_targeted/best_design/load_case_1_results.png
