NikhilVeeram/MEEN-305-FINAL/optimization_v2_P/best_design/load_case_2_results.png

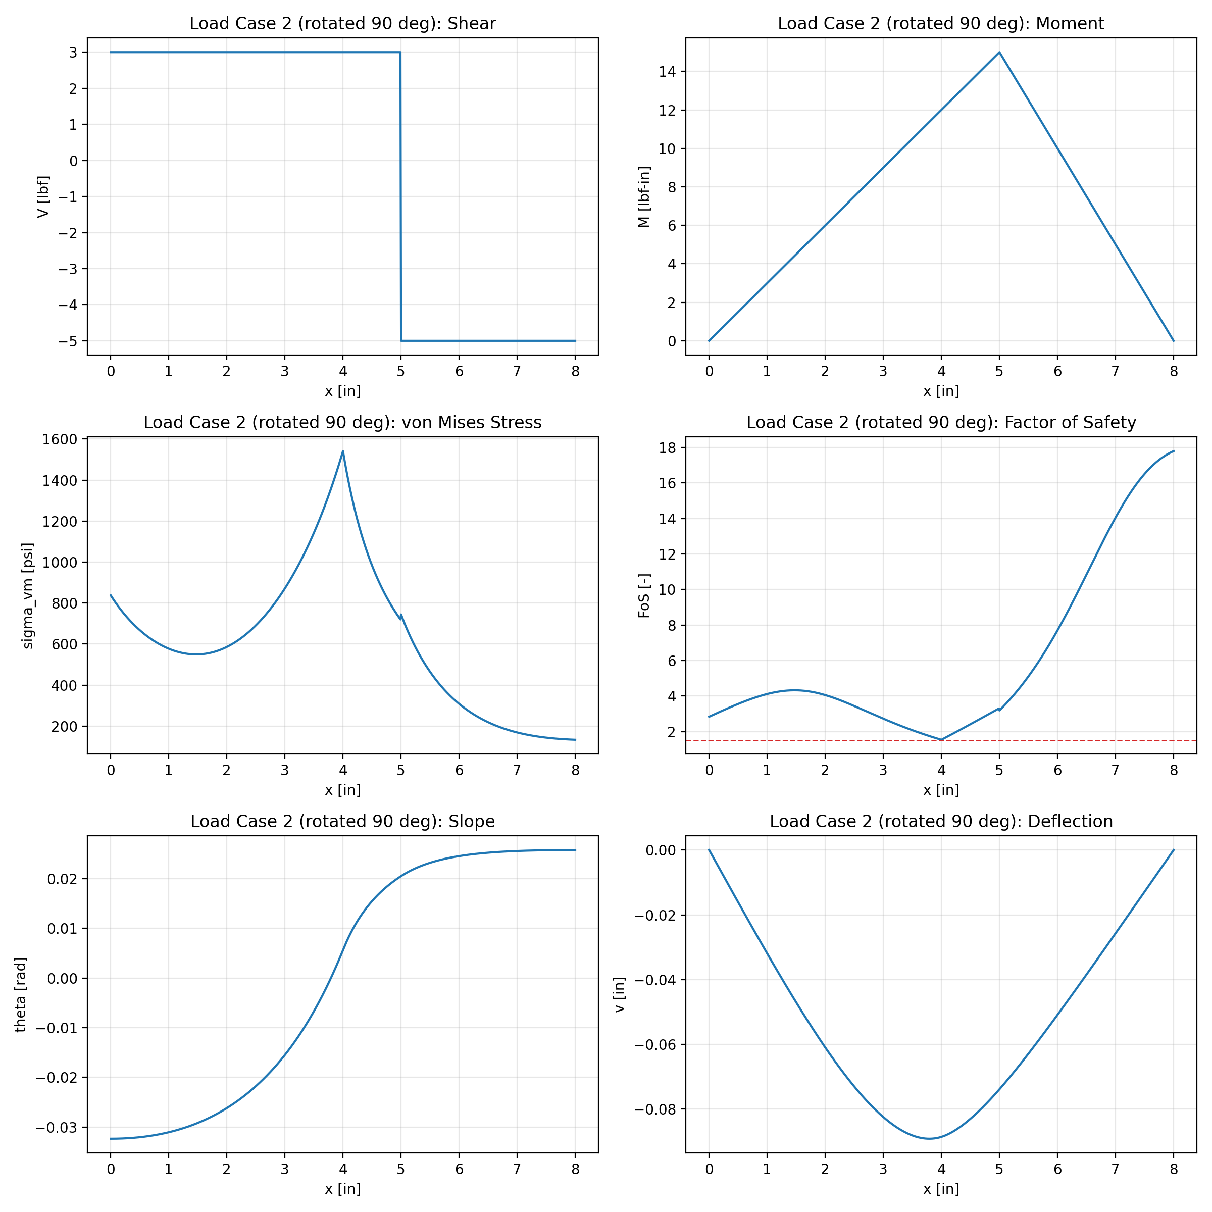
optimization_v2_P/best_design/load_case_2_results.png
