NikhilVeeram/MEEN-305-FINAL/outputs/load_case_2_results.png

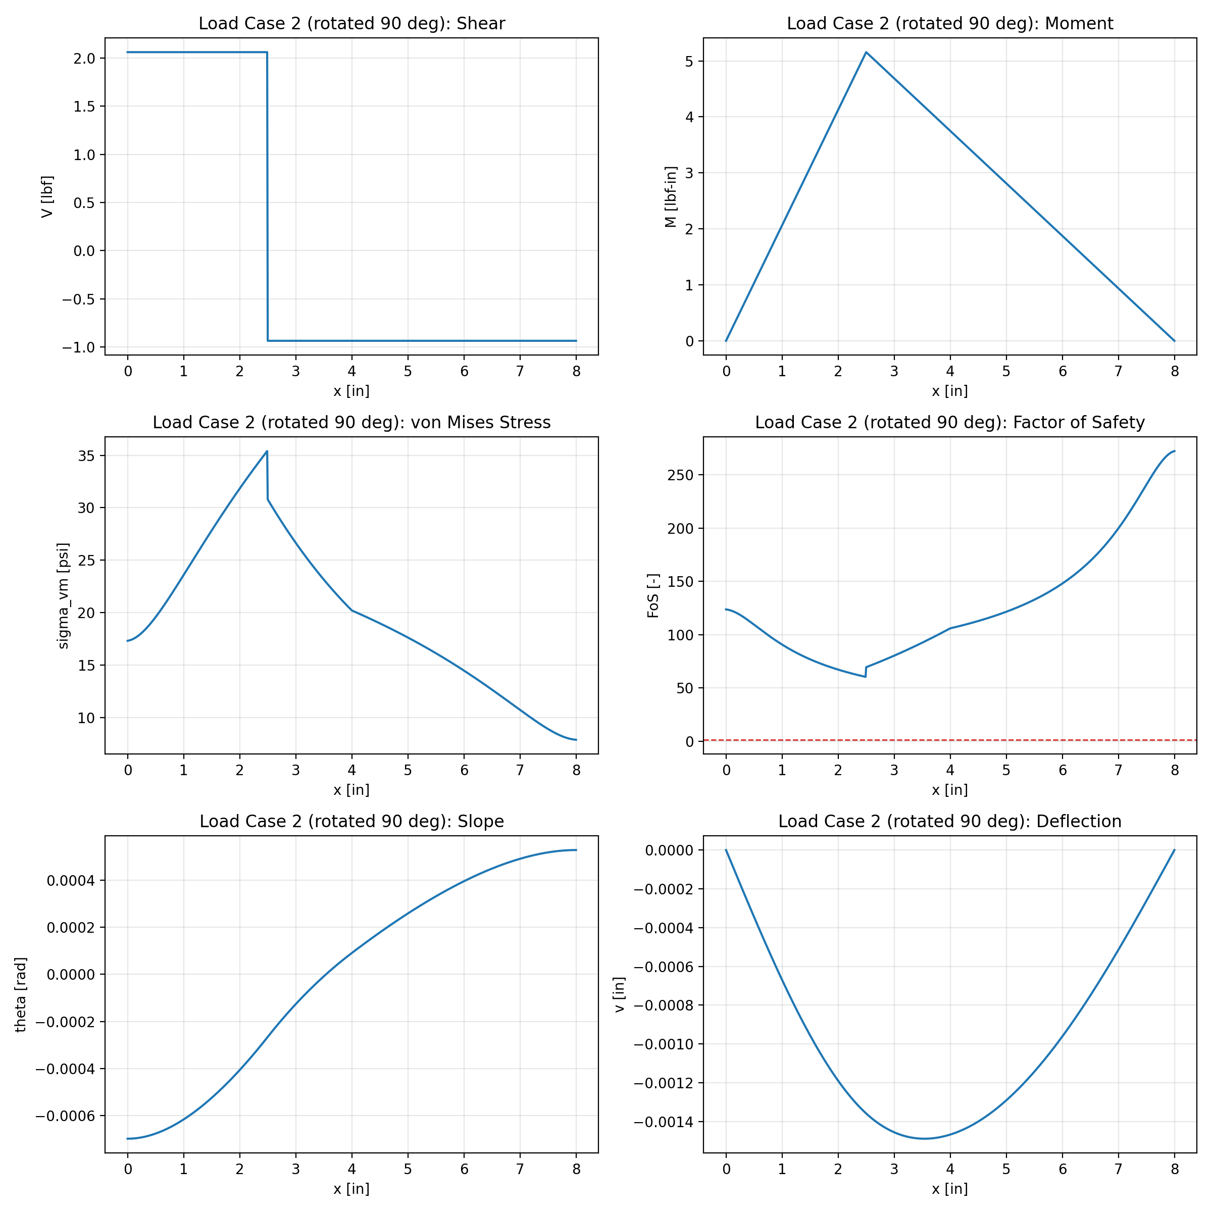
outputs/load_case_2_results.png
