NikhilVeeram/MEEN-305-FINAL/outputs_custom_test/outer_dimension_views.png

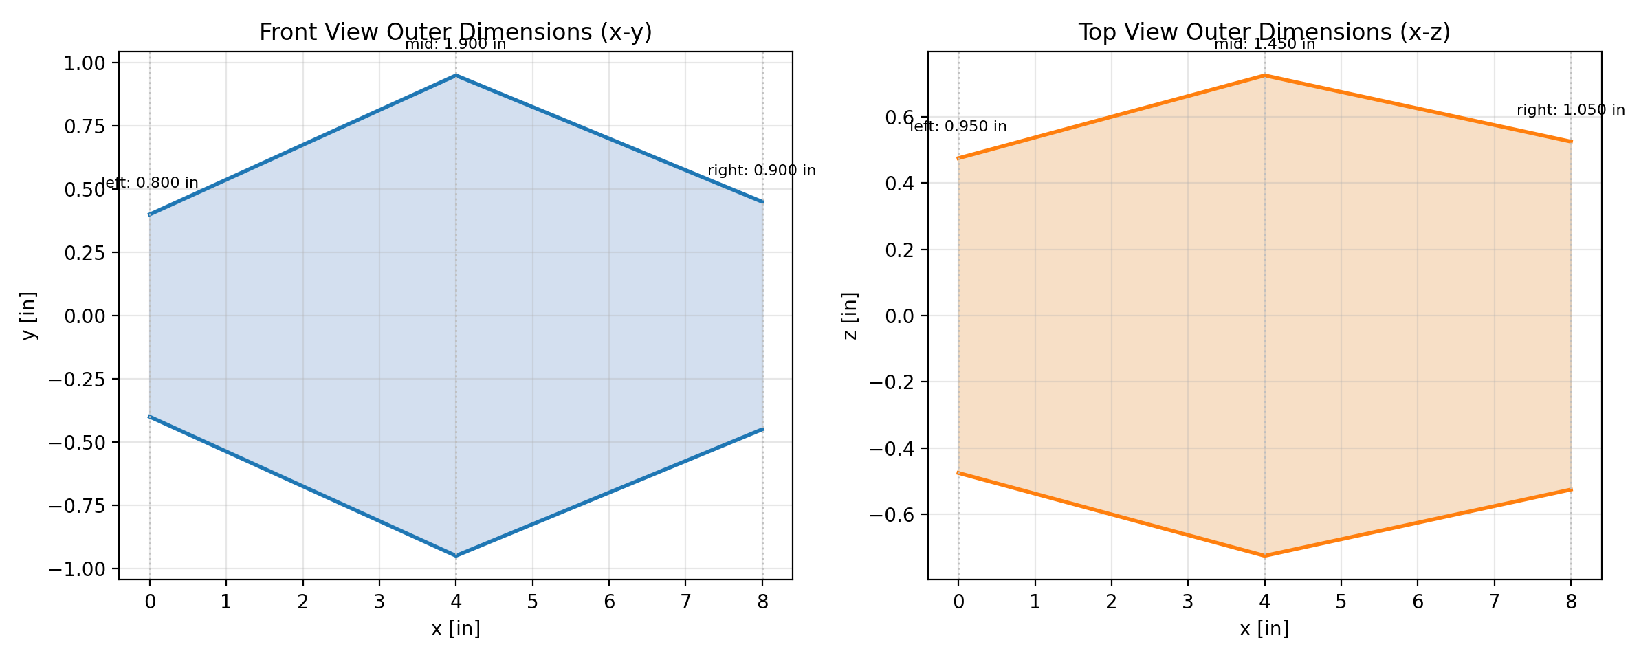
outputs_custom_test/outer_dimension_views.png
